SeByDocKy/pvbrain2/configuration_examples/dashboard/YamBMS_HA_Dashboard_page1_YAMBMS.png

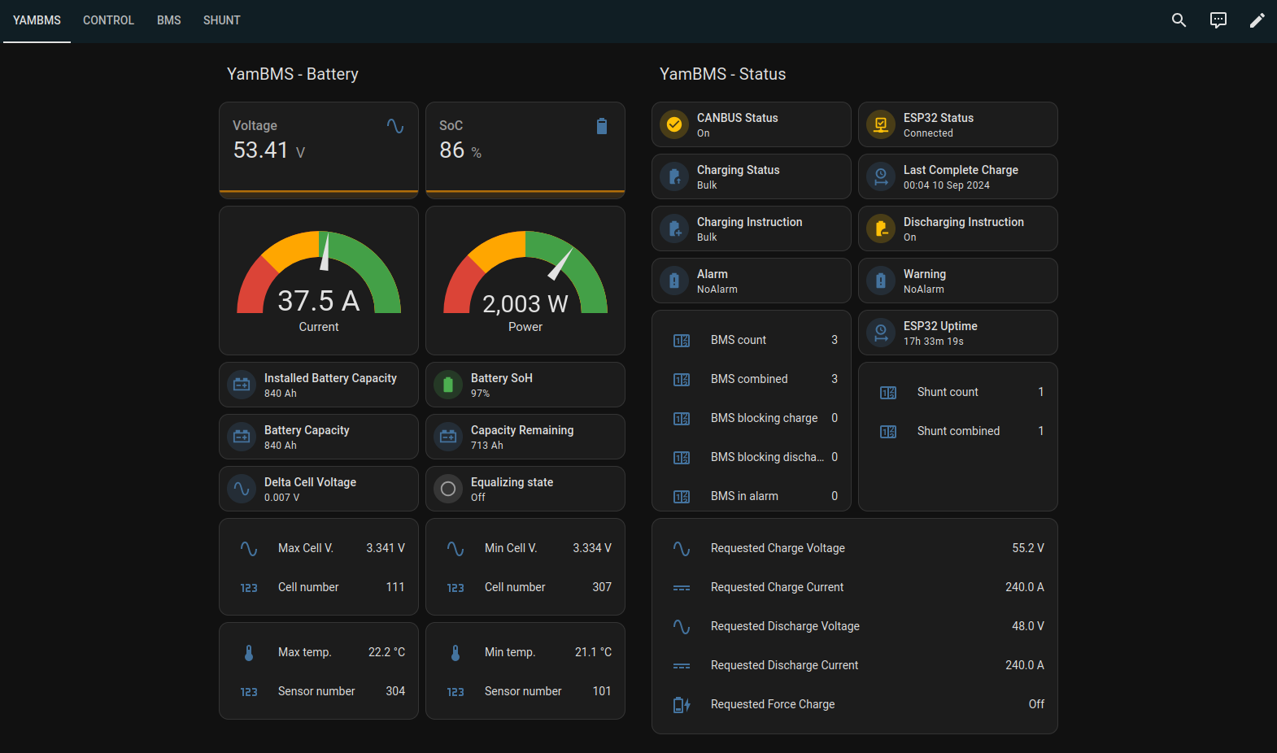
configuration_examples/dashboard/YamBMS_HA_Dashboard_page1_YAMBMS.png
