SeByDocKy/pvbrain2/configuration_examples/dashboard/YamBMS_HA_Dashboard_page2_CONTROL.png

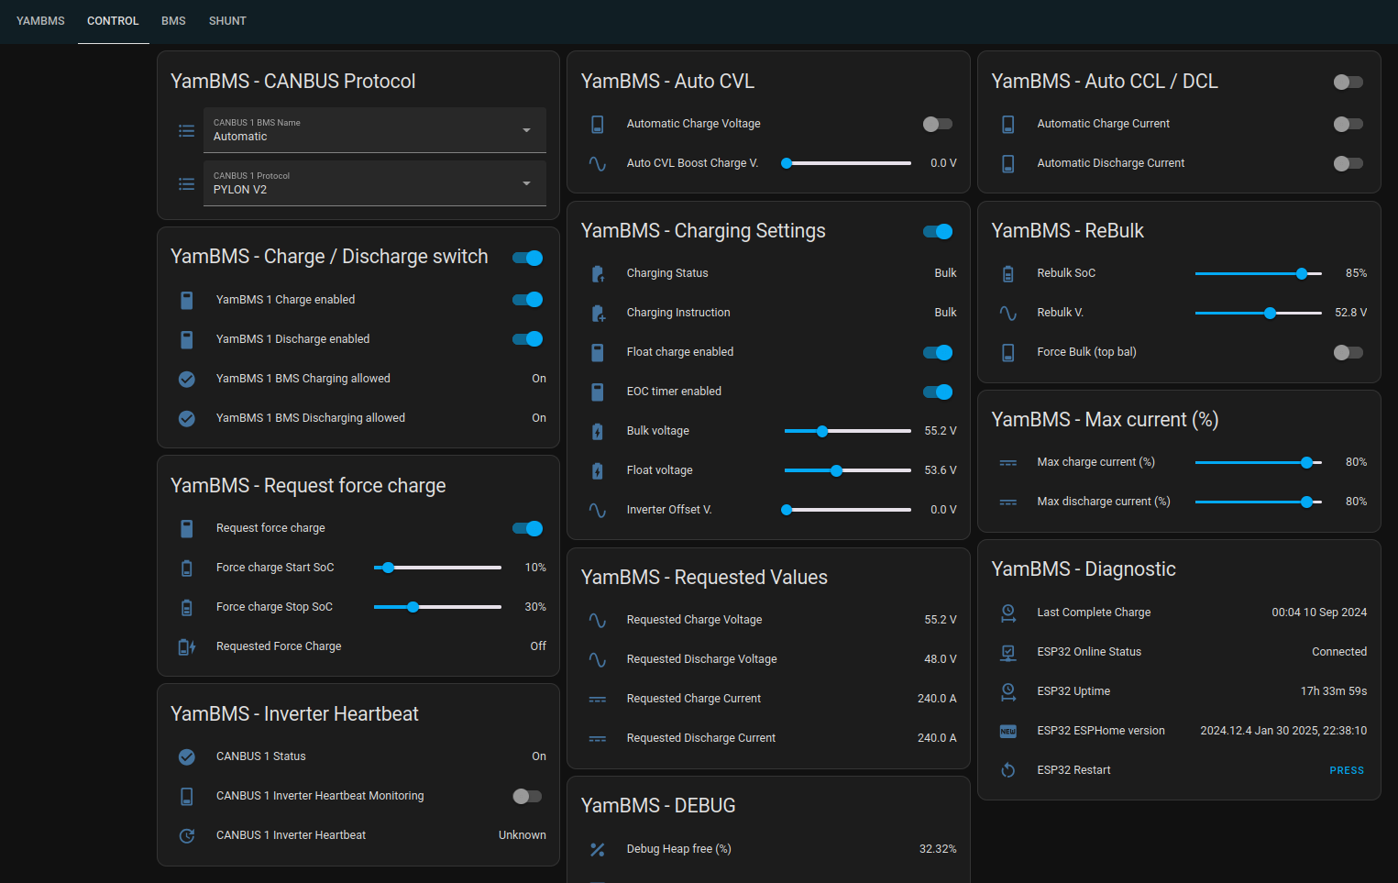
configuration_examples/dashboard/YamBMS_HA_Dashboard_page2_CONTROL.png
