SeByDocKy/pvbrain2/configuration_examples/dashboard/YamBMS_HA_Dashboard_page3_BMS.png

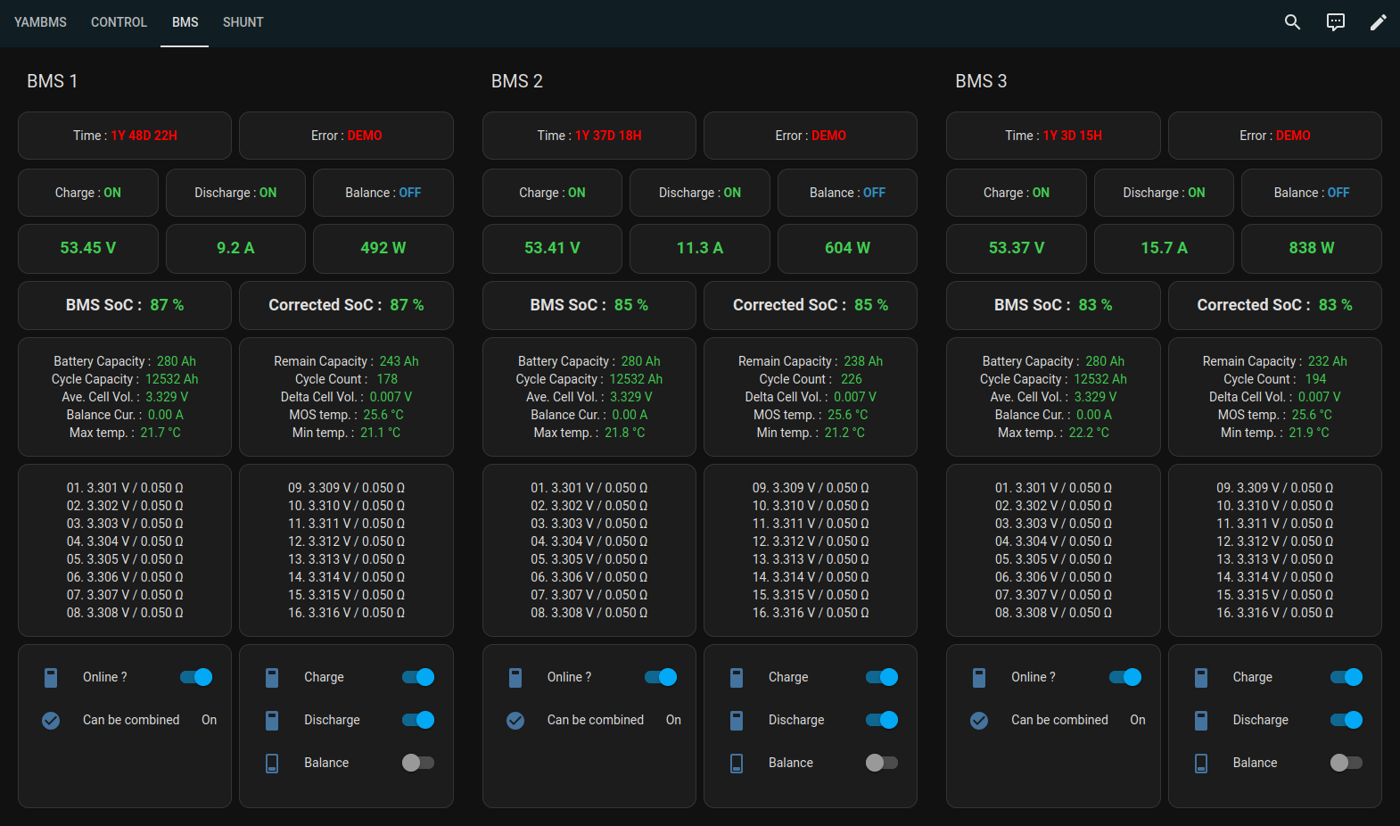
configuration_examples/dashboard/YamBMS_HA_Dashboard_page3_BMS.png
