SeByDocKy/pvbrain2/configuration_examples/dashboard/YamBMS_HA_Dashboard_page4_SHUNT.png

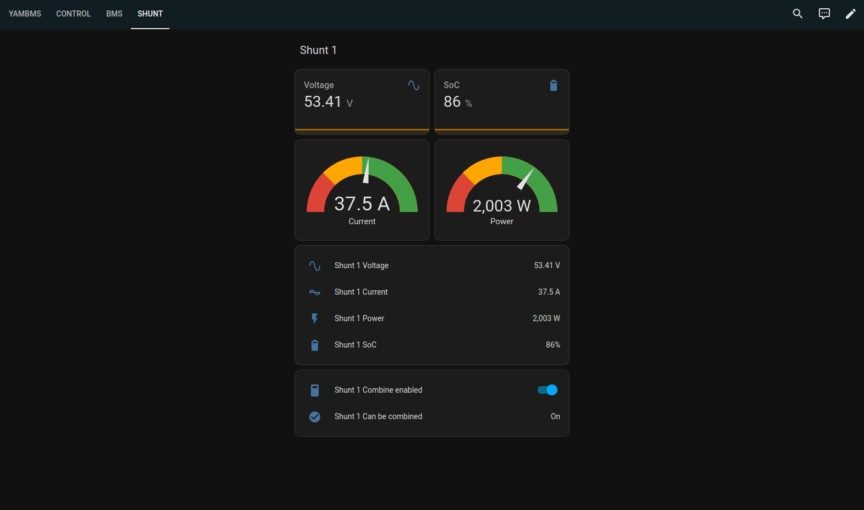
configuration_examples/dashboard/YamBMS_HA_Dashboard_page4_SHUNT.png
