SeByDocKy/pvbrain2/hardware/addon_carte_clamp_meter/clamp_meter_circuit_extend.png

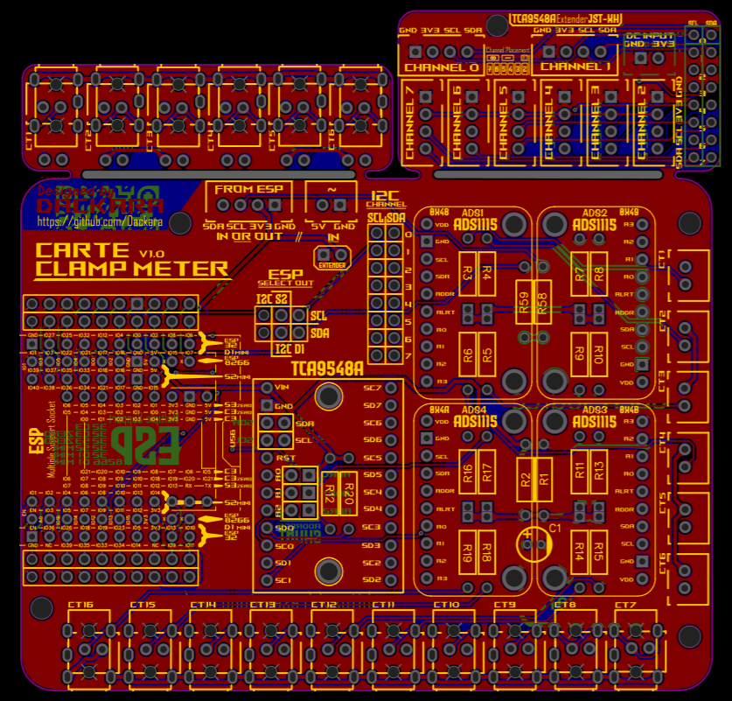
hardware/addon_carte_clamp_meter/clamp_meter_circuit_extend.png
