SeByDocKy/pvbrain2/hardware/addon_carte_fil_pilote/fil_pilote_3d_view.png

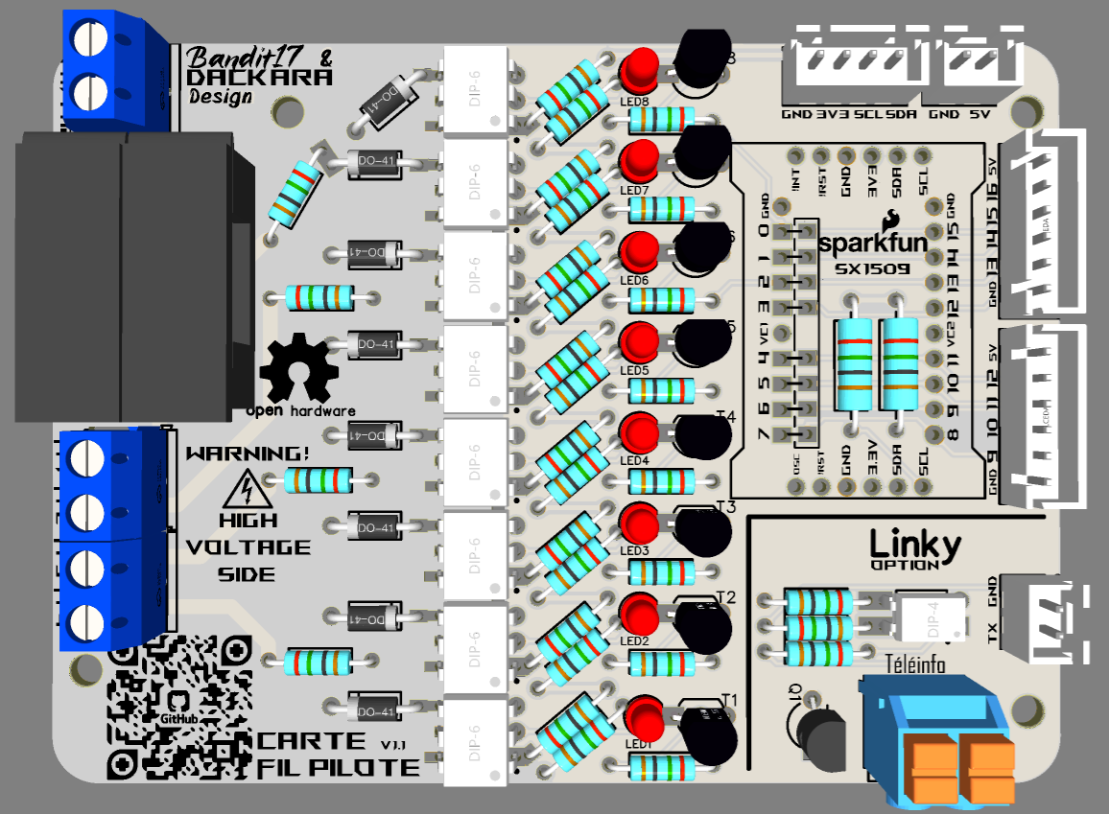
hardware/addon_carte_fil_pilote/fil_pilote_3d_view.png
