SeByDocKy/pvbrain2/hardware/addon_carte_fil_pilote/fil_pilote_photo.jpeg

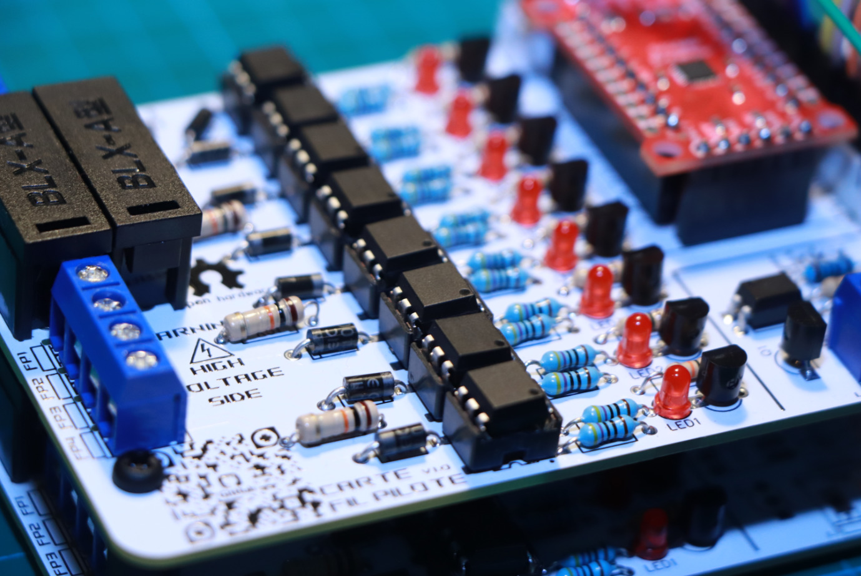
hardware/addon_carte_fil_pilote/fil_pilote_photo.jpeg
