SeByDocKy/pvbrain2/hardware/addon_carte_fil_pilote/fil_pilote_schematic_fp.png

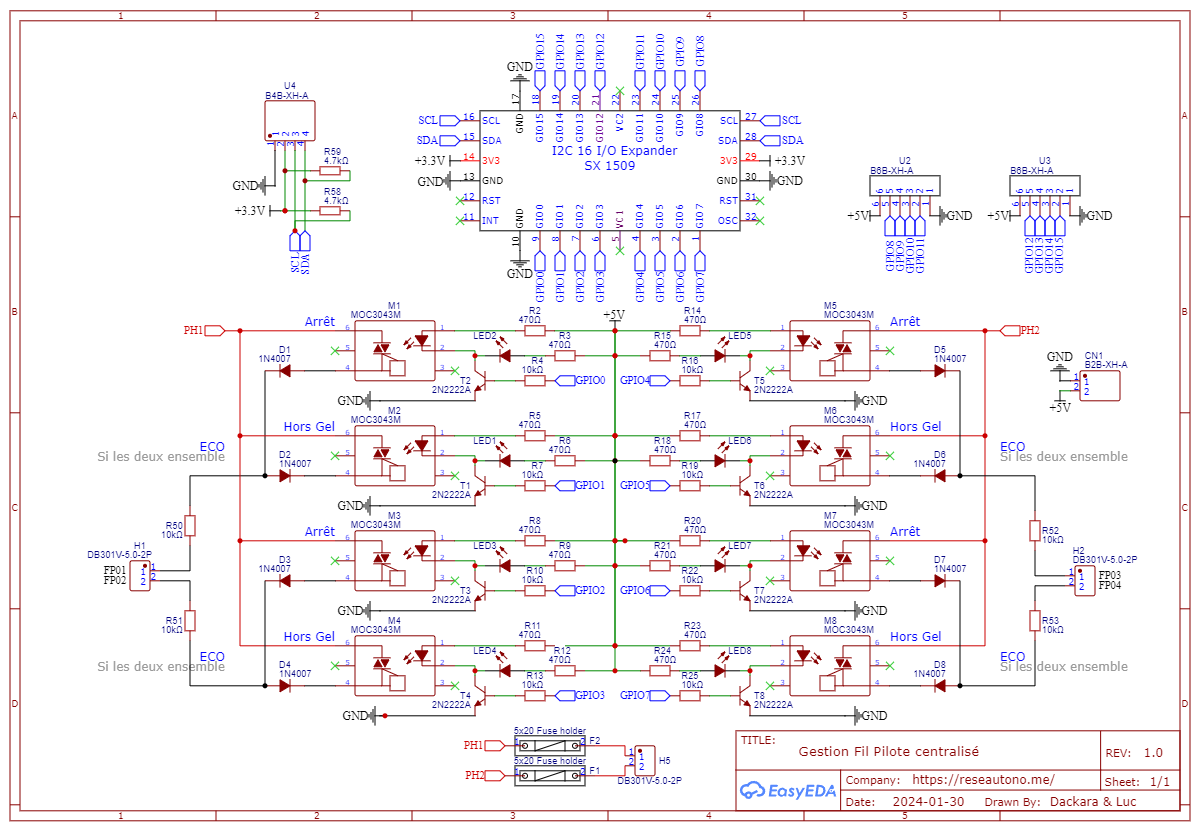
hardware/addon_carte_fil_pilote/fil_pilote_schematic_fp.png
