SeByDocKy/pvbrain2/hardware/addon_carte_fil_pilote/fil_pilote_v1.1_circuit_full.png

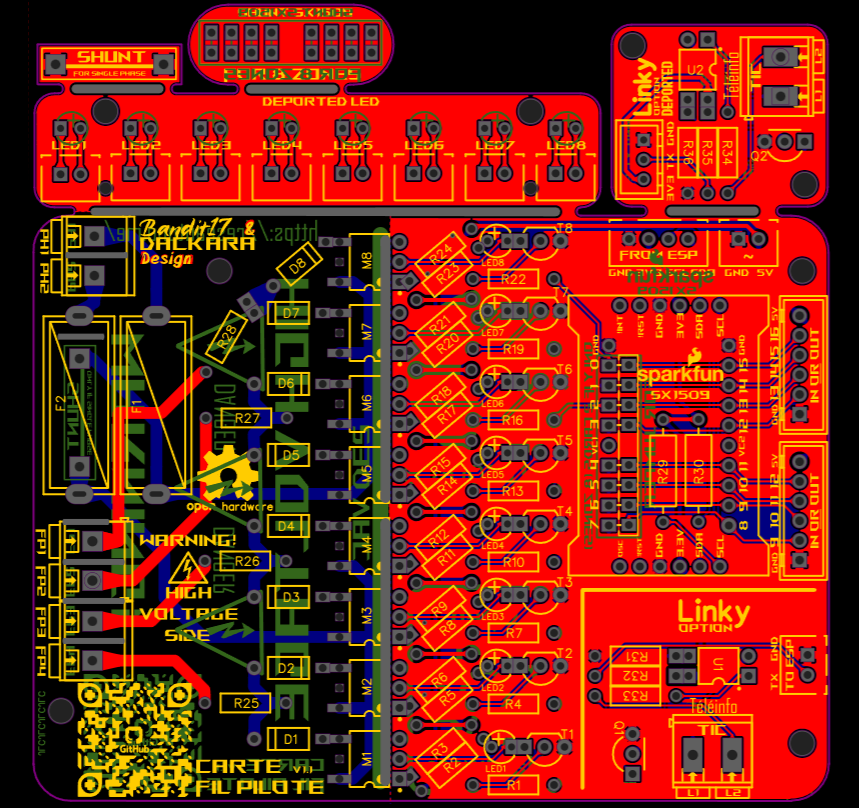
hardware/addon_carte_fil_pilote/fil_pilote_v1.1_circuit_full.png
