SeByDocKy/pvbrain2/hardware/addon_carte_prototype/carte_prototype_front_extend.png

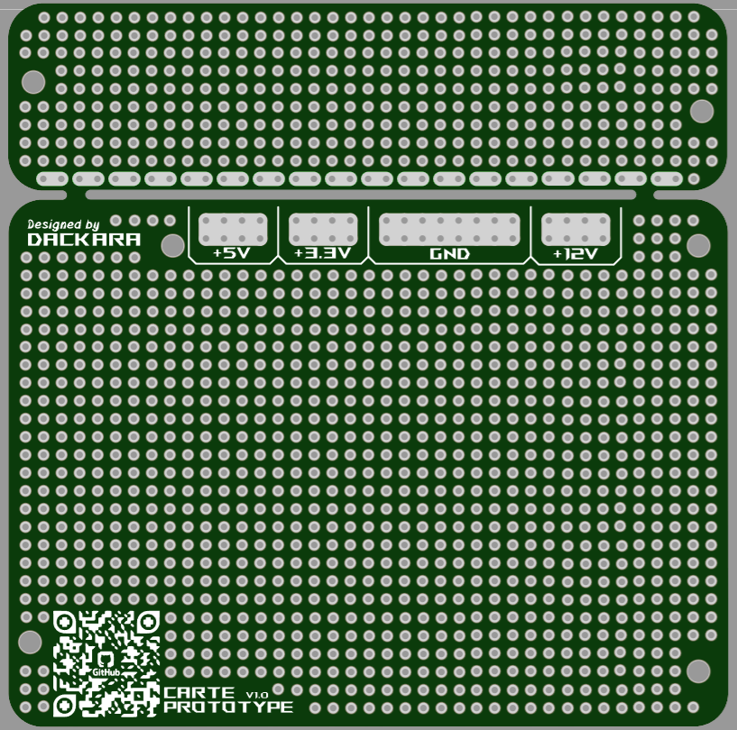
hardware/addon_carte_prototype/carte_prototype_front_extend.png
