SeByDocKy/pvbrain2/hardware/addon_carte_uart_extension/uart_extention_with_isolator-victron/uart_extension_with_victron_3d_view.png

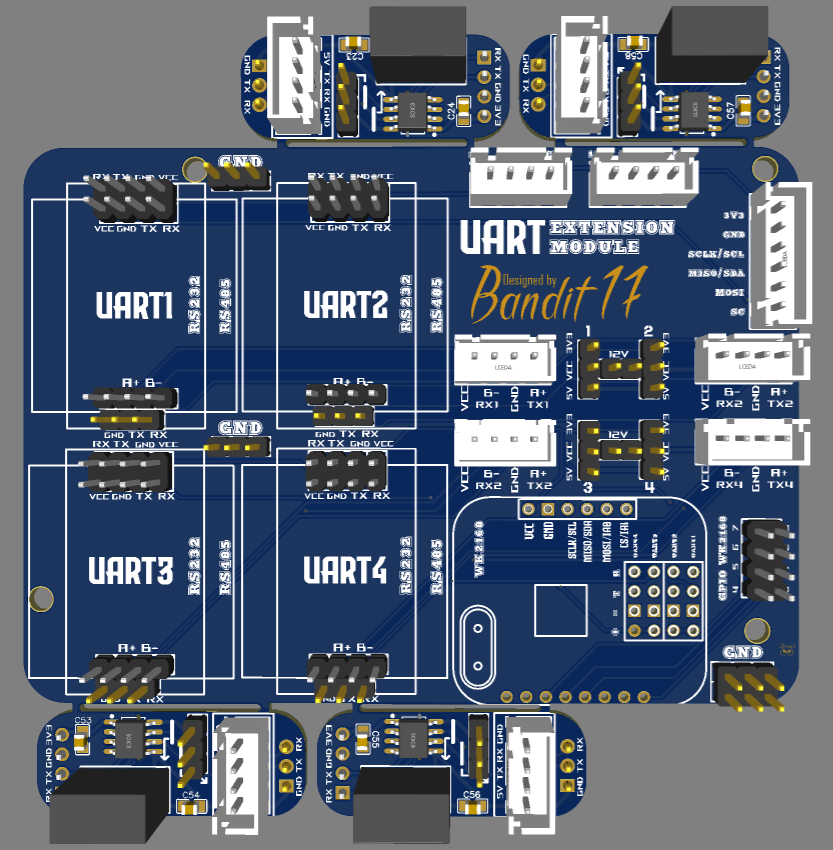
hardware/addon_carte_uart_extension/uart_extention_with_isolator-victron/uart_extension_with_victron_3d_view.png
