SeByDocKy/pvbrain2/hardware/module_wk_2132/wk2132_front.png

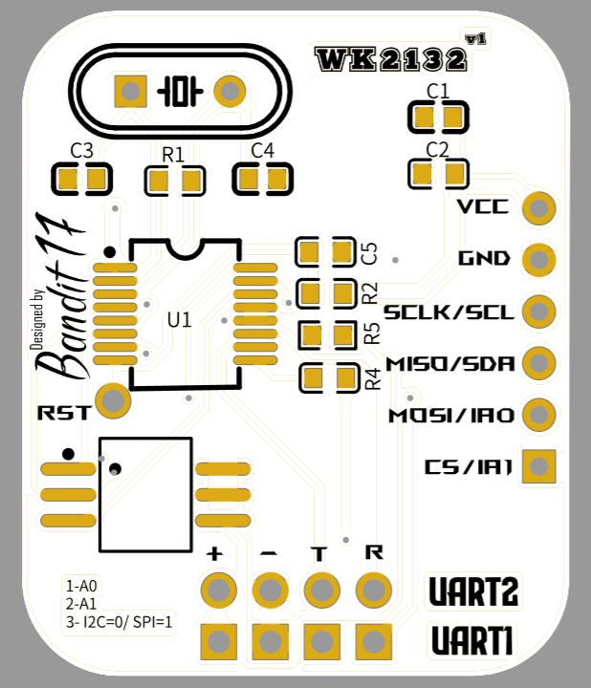
hardware/module_wk_2132/wk2132_front.png
