SeByDocKy/pvbrain2/pictures/pvbrain_all_thing_3d_view.png

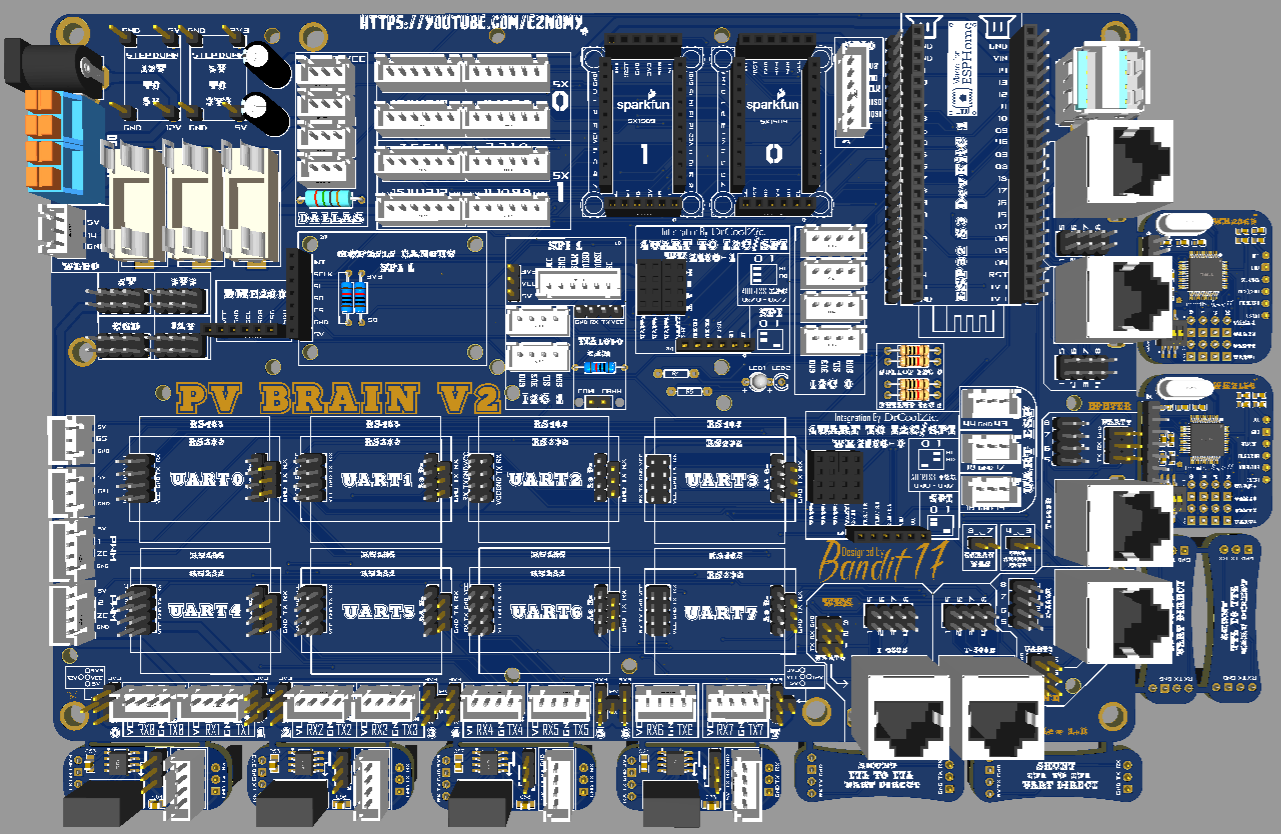
pictures/pvbrain_all_thing_3d_view.png
