SeByDocKy/pvbrain2/pictures/pvbrain_all_thing_back.png

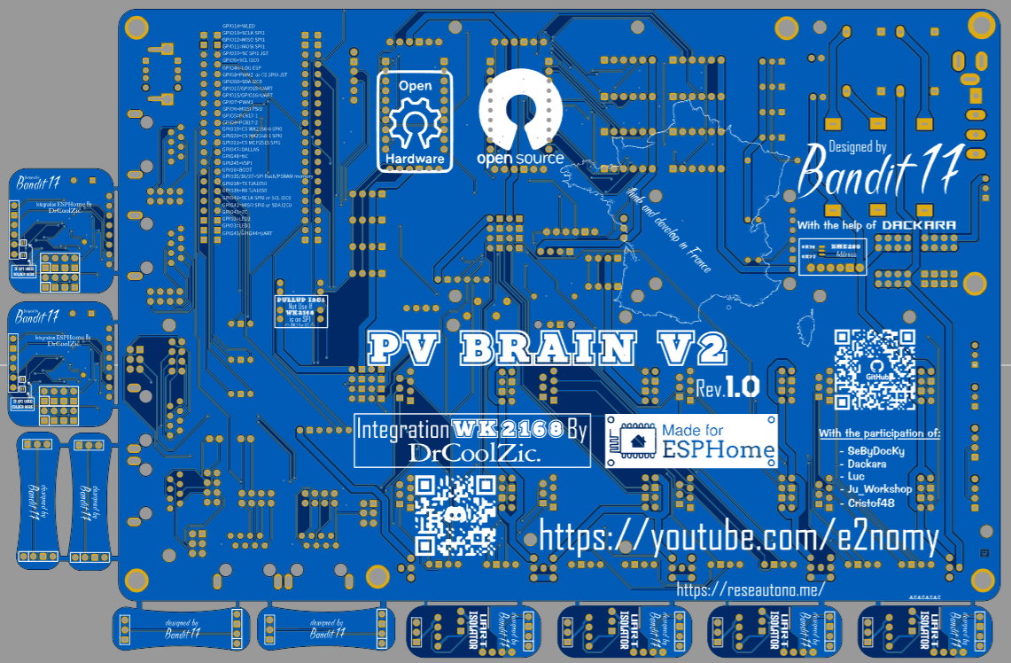
pictures/pvbrain_all_thing_back.png
