SeByDocKy/pvbrain2/pictures/pvbrain_all_thing_front.png

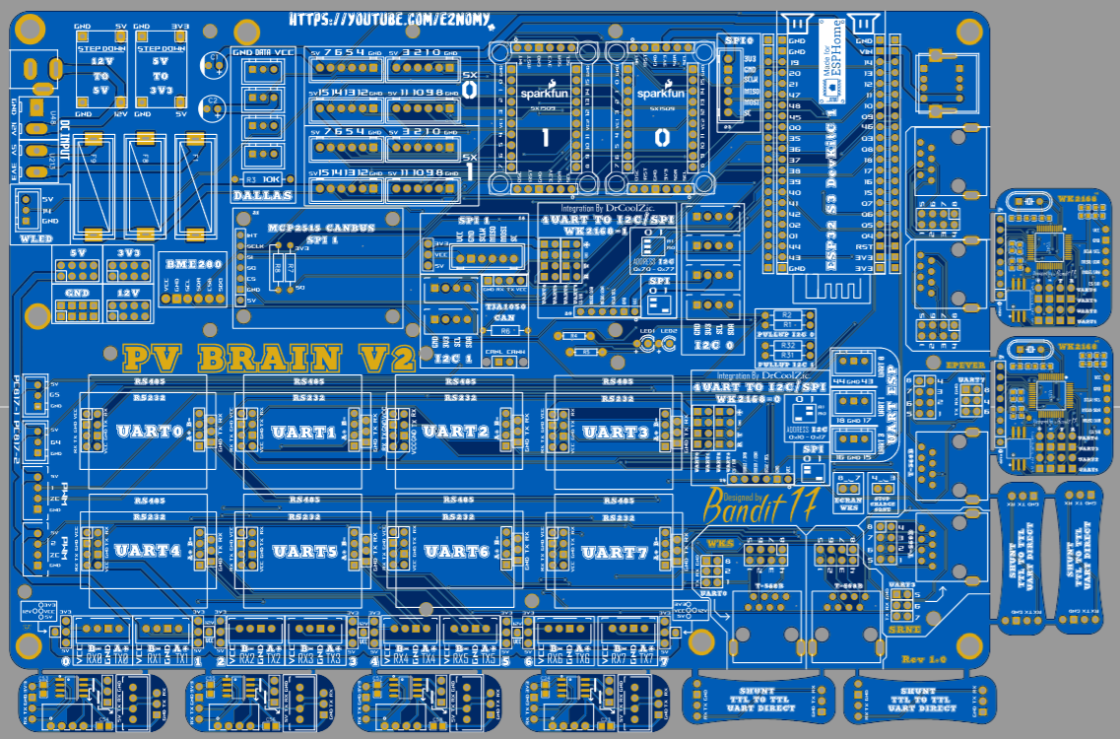
pictures/pvbrain_all_thing_front.png
