SeByDocKy/pvbrain2/pictures/pvbrain_view_bicolor_led.png

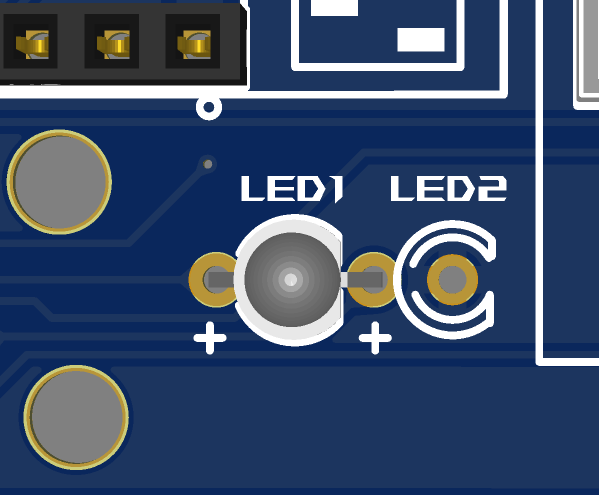
pictures/pvbrain_view_bicolor_led.png
