SeByDocKy/pvbrain2/pictures/pvbrain_view_bme280.png

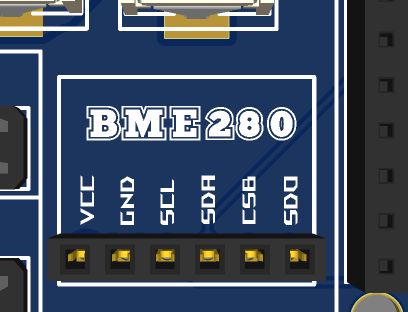
pictures/pvbrain_view_bme280.png
