SeByDocKy/pvbrain2/pictures/pvbrain_view_bme280_change_address.png

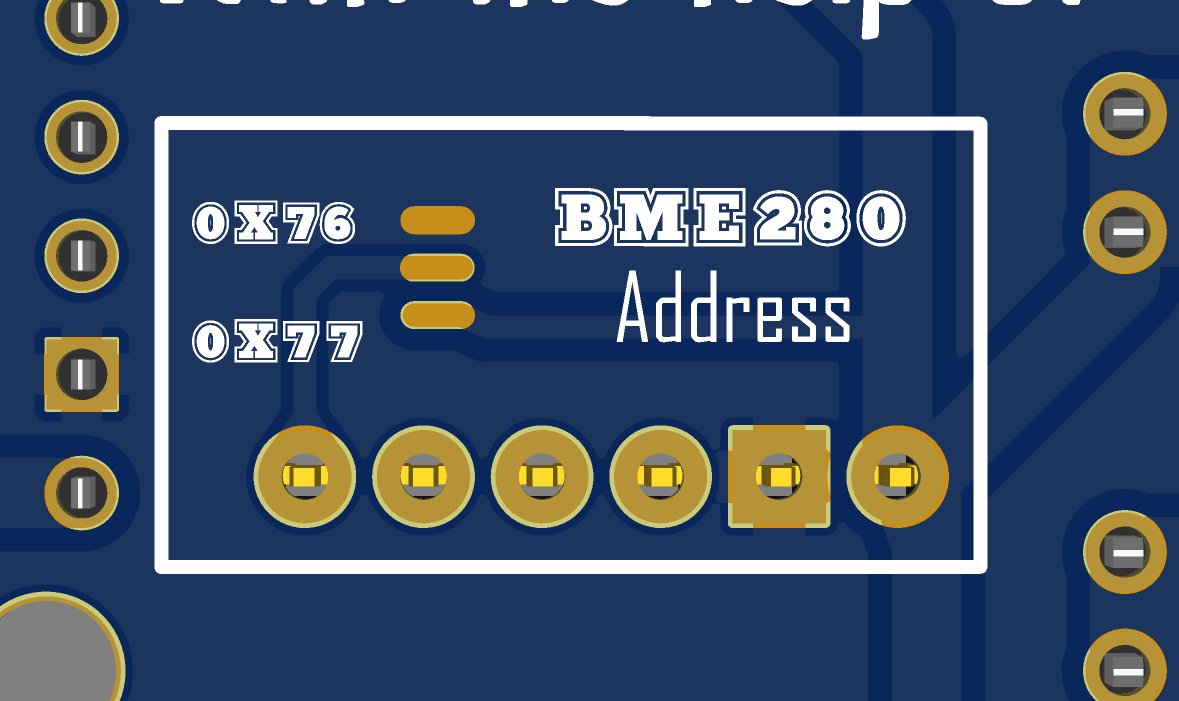
pictures/pvbrain_view_bme280_change_address.png
