SeByDocKy/pvbrain2/pictures/pvbrain_view_can_output.png

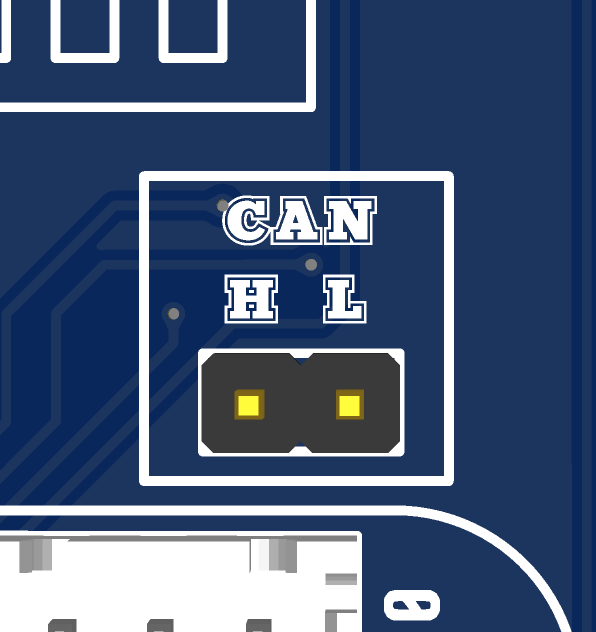
pictures/pvbrain_view_can_output.png
