SeByDocKy/pvbrain2/pictures/pvbrain_view_dallas.png

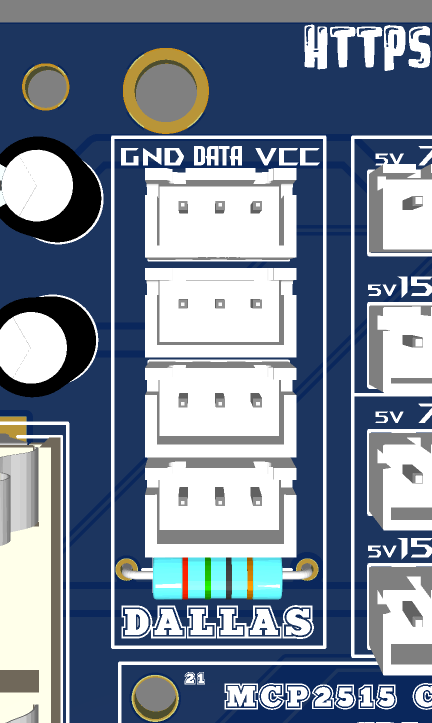
pictures/pvbrain_view_dallas.png
