SeByDocKy/pvbrain2/pictures/pvbrain_view_dc_input.png

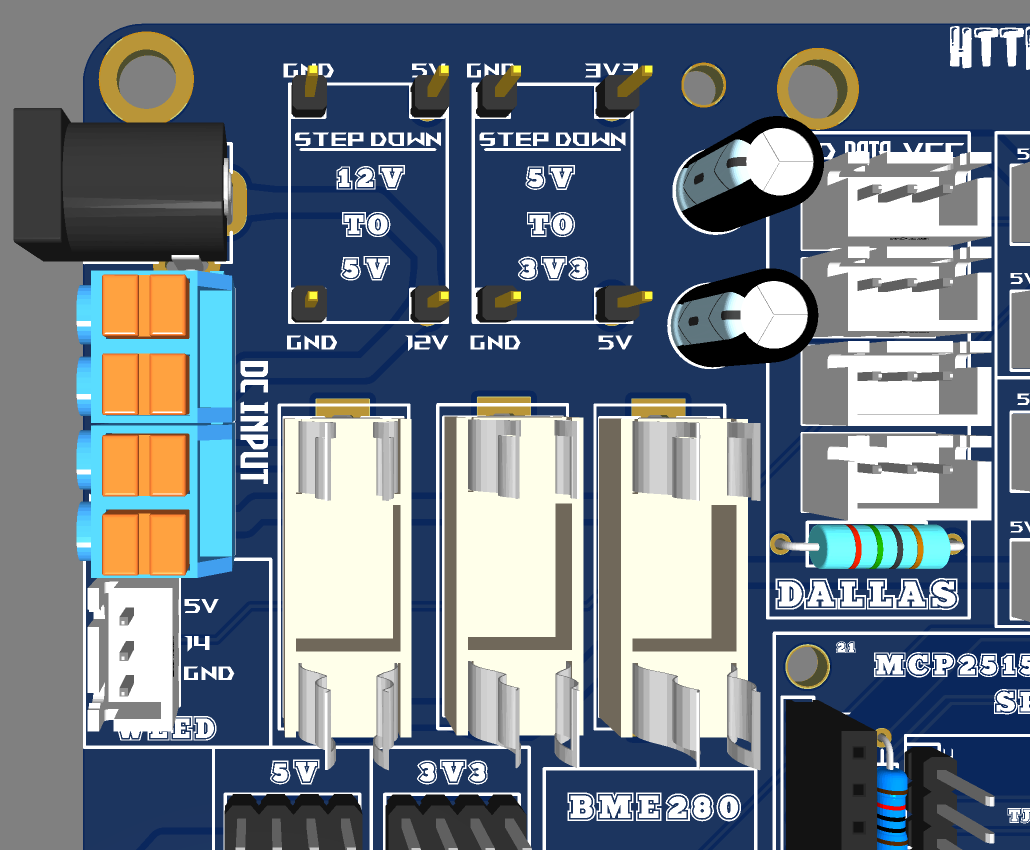
pictures/pvbrain_view_dc_input.png
