SeByDocKy/pvbrain2/pictures/pvbrain_view_dc_output.png

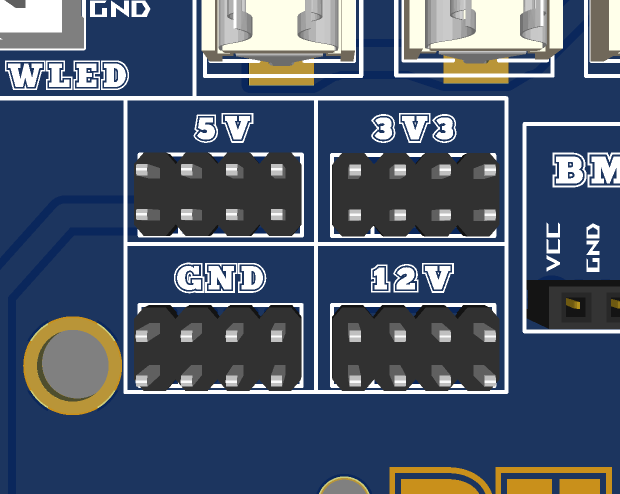
pictures/pvbrain_view_dc_output.png
