SeByDocKy/pvbrain2/pictures/pvbrain_view_epever_output.png

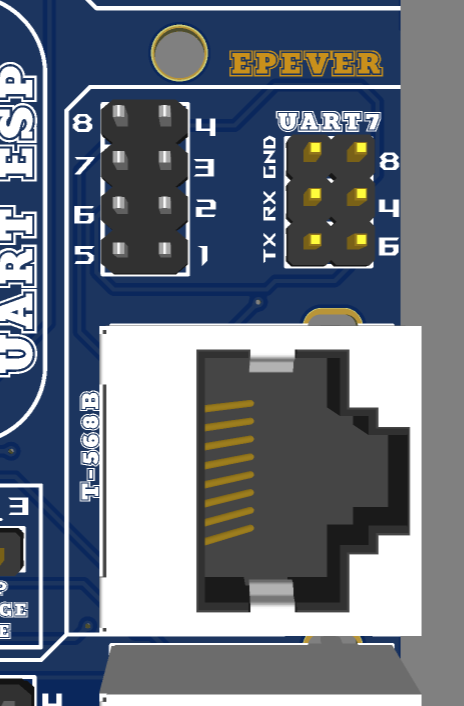
pictures/pvbrain_view_epever_output.png
