SeByDocKy/pvbrain2/pictures/pvbrain_view_esp32s3_socket.png

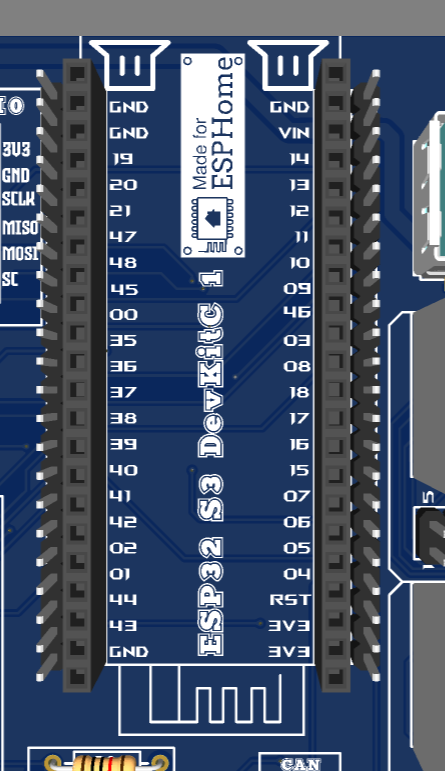
pictures/pvbrain_view_esp32s3_socket.png
