SeByDocKy/pvbrain2/pictures/pvbrain_view_i2c0.png

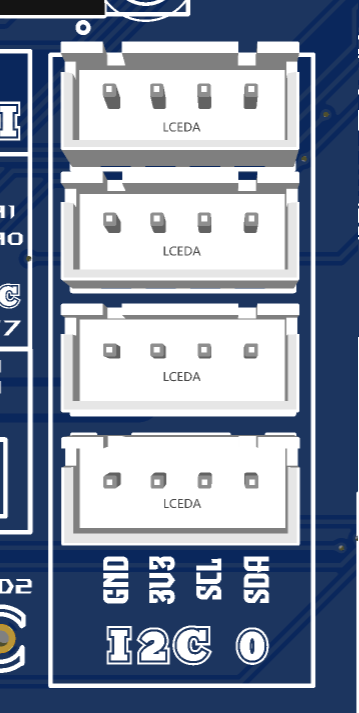
pictures/pvbrain_view_i2c0.png
