SeByDocKy/pvbrain2/pictures/pvbrain_view_i2c1.png

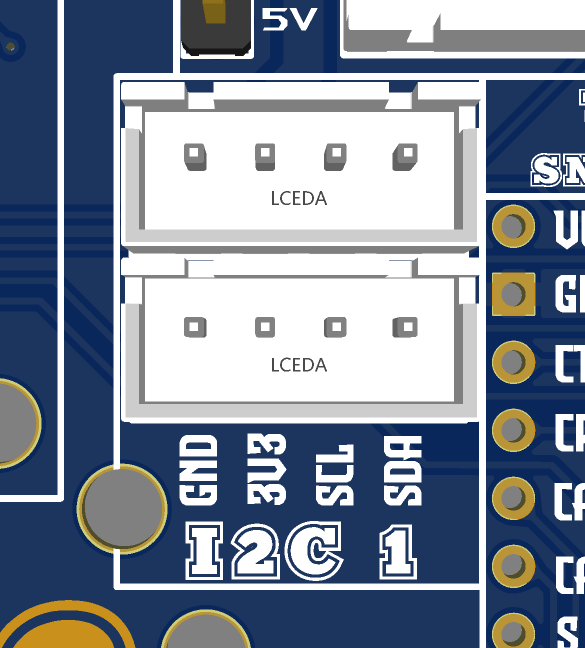
pictures/pvbrain_view_i2c1.png
