SeByDocKy/pvbrain2/pictures/pvbrain_view_isolator_jkbms.png

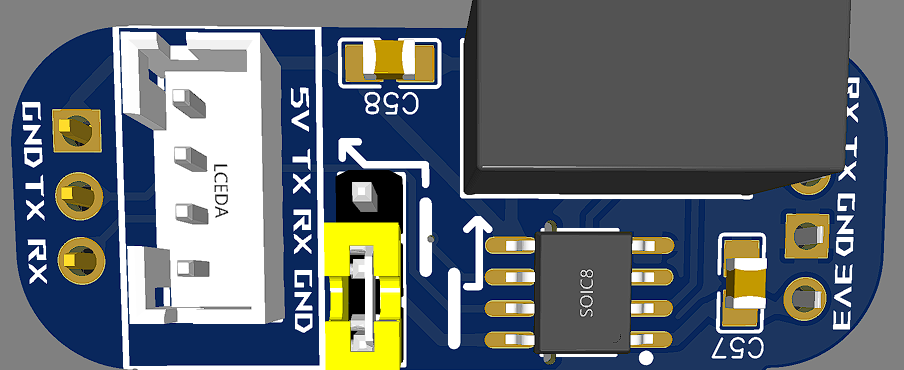
pictures/pvbrain_view_isolator_jkbms.png
