SeByDocKy/pvbrain2/pictures/pvbrain_view_isolator_pzem.png

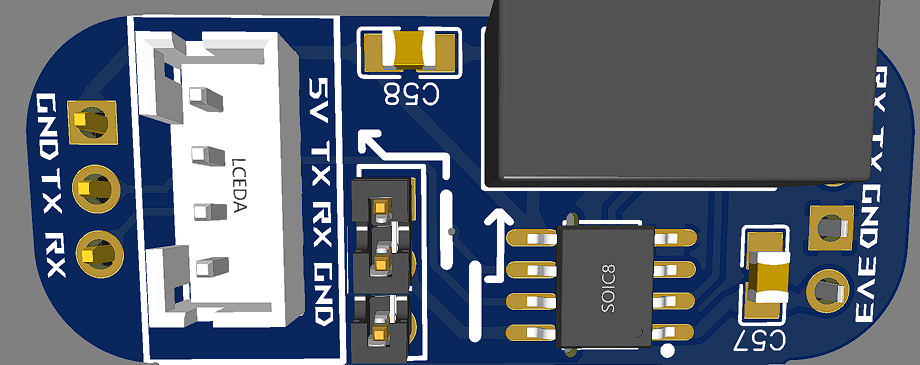
pictures/pvbrain_view_isolator_pzem.png
