SeByDocKy/pvbrain2/pictures/pvbrain_view_isolator_Victron.png

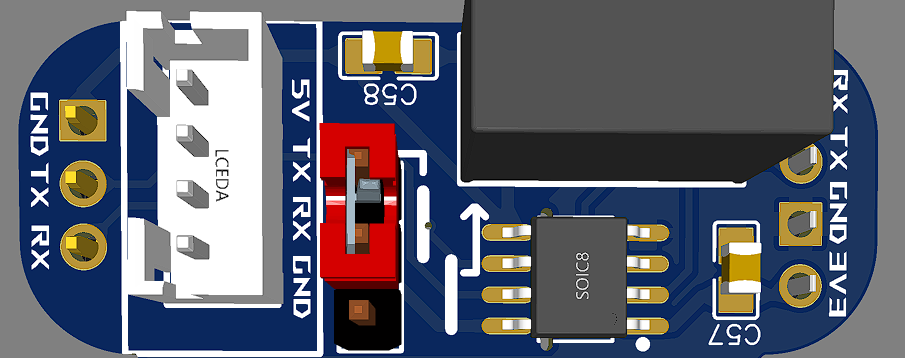
pictures/pvbrain_view_isolator_Victron.png
