SeByDocKy/pvbrain2/pictures/pvbrain_view_mcp2515.png

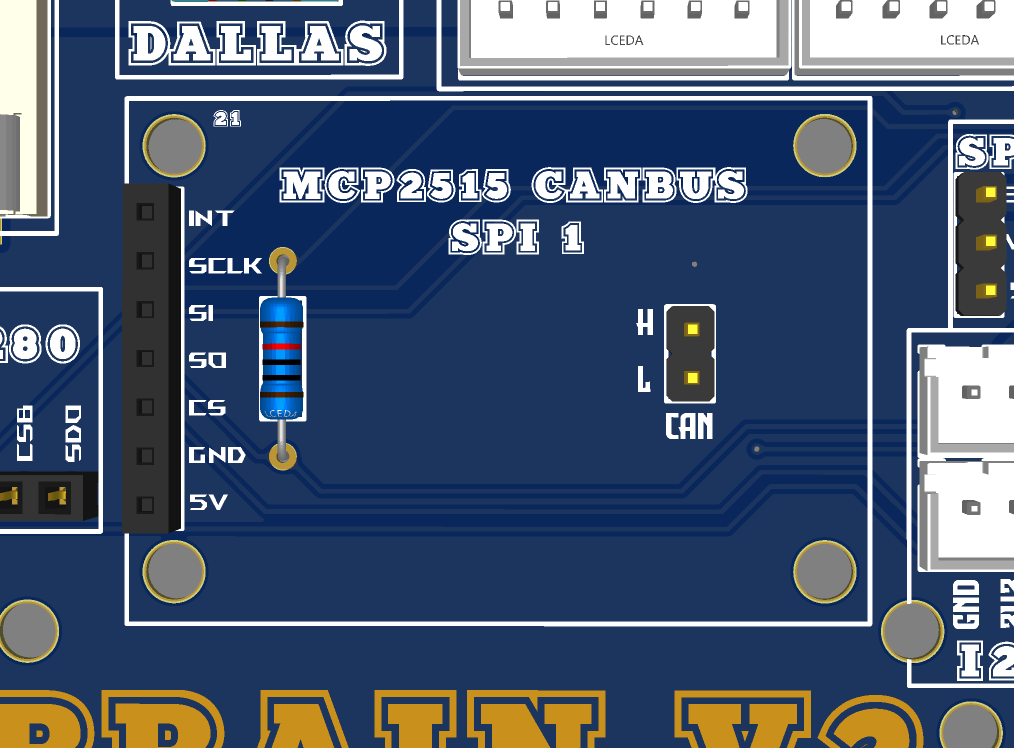
pictures/pvbrain_view_mcp2515.png
