SeByDocKy/pvbrain2/pictures/pvbrain_view_opto_output.png

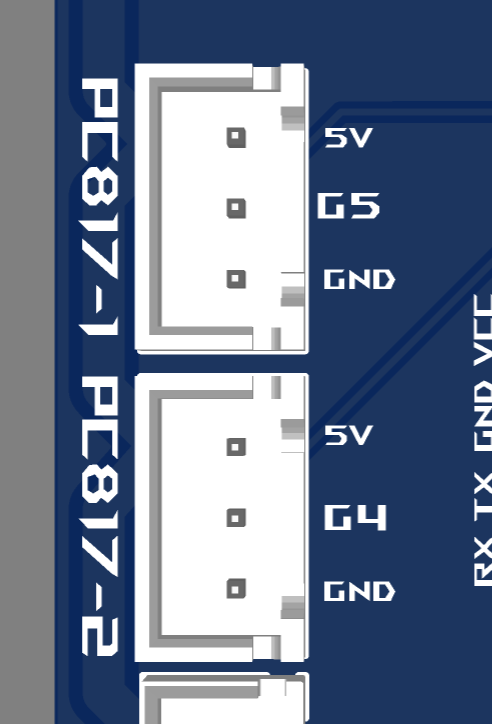
pictures/pvbrain_view_opto_output.png
