SeByDocKy/pvbrain2/pictures/pvbrain_view_physical_uart.png

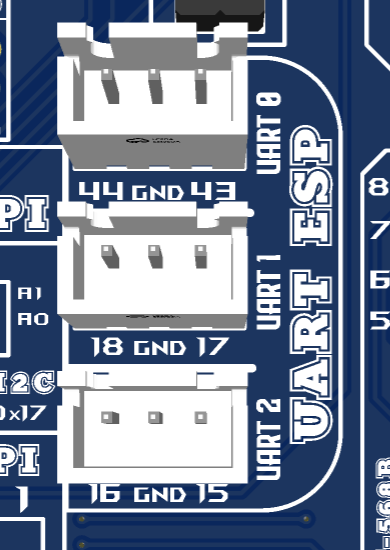
pictures/pvbrain_view_physical_uart.png
