SeByDocKy/pvbrain2/pictures/pvbrain_view_pwm_output.png

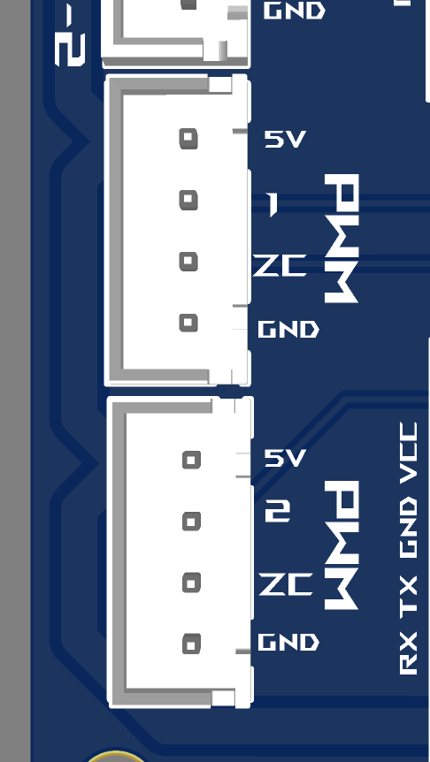
pictures/pvbrain_view_pwm_output.png
