SeByDocKy/pvbrain2/pictures/pvbrain_view_snre_output.png

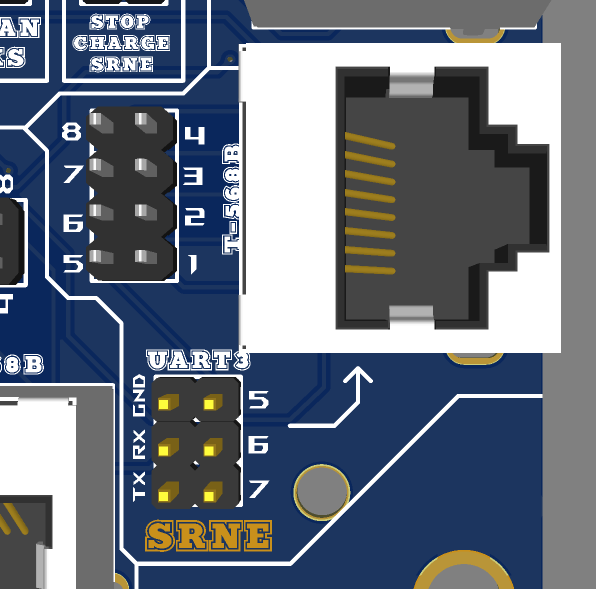
pictures/pvbrain_view_snre_output.png
