SeByDocKy/pvbrain2/pictures/pvbrain_view_spi0.png

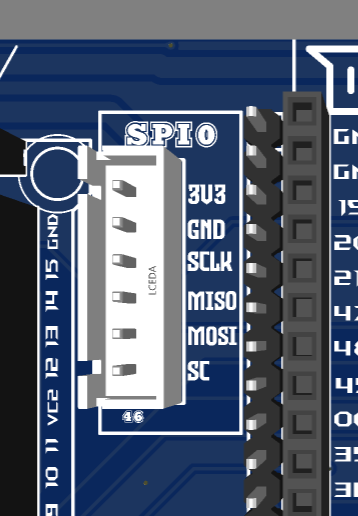
pictures/pvbrain_view_spi0.png
