SeByDocKy/pvbrain2/pictures/pvbrain_view_spi1.png

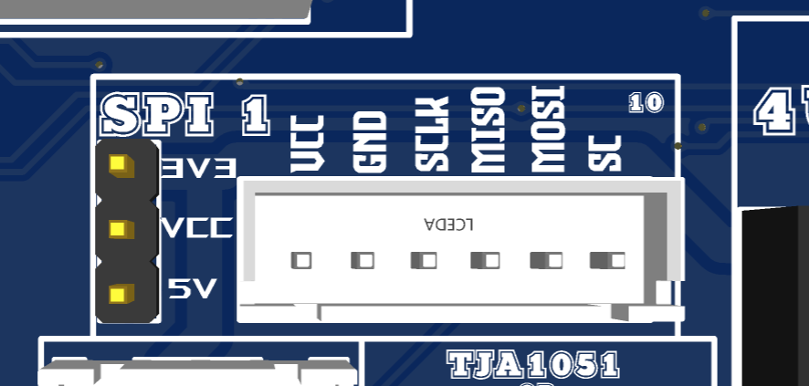
pictures/pvbrain_view_spi1.png
