SeByDocKy/pvbrain2/pictures/pvbrain_view_sx1509.png

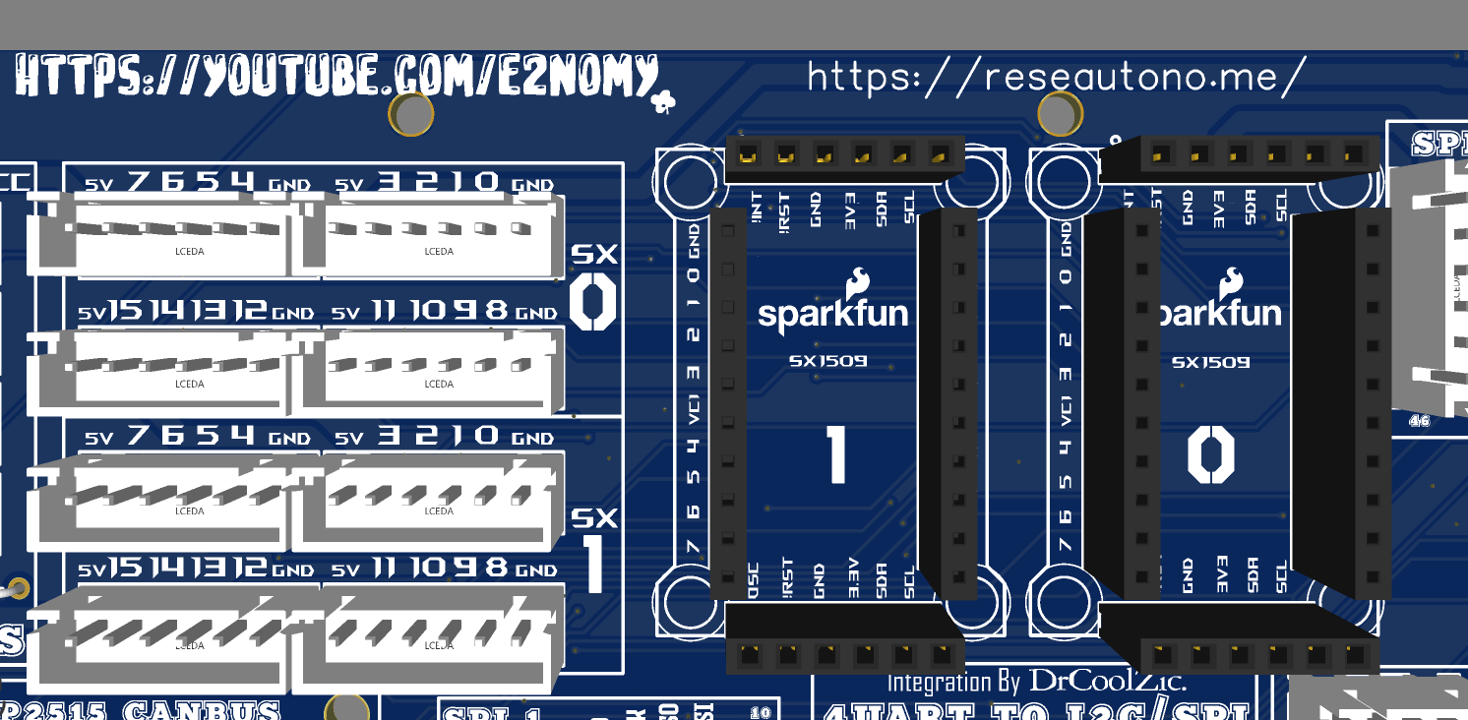
pictures/pvbrain_view_sx1509.png
