SeByDocKy/pvbrain2/pictures/pvbrain_view_tja1051_or_sn65hvd230.png

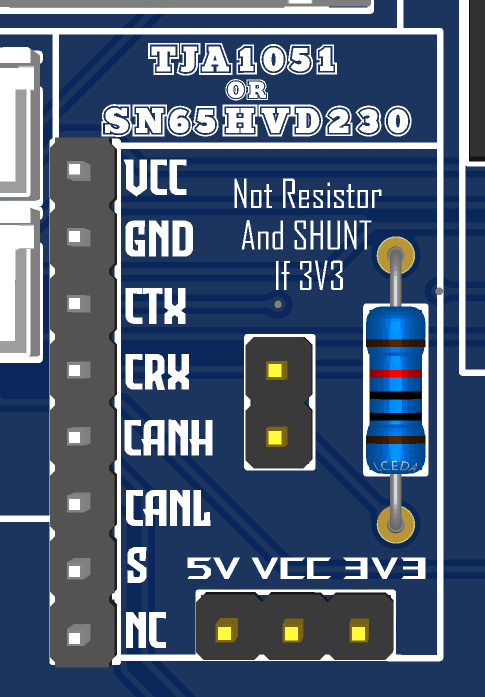
pictures/pvbrain_view_tja1051_or_sn65hvd230.png
