SeByDocKy/pvbrain2/pictures/pvbrain_view_wk2168-1.png

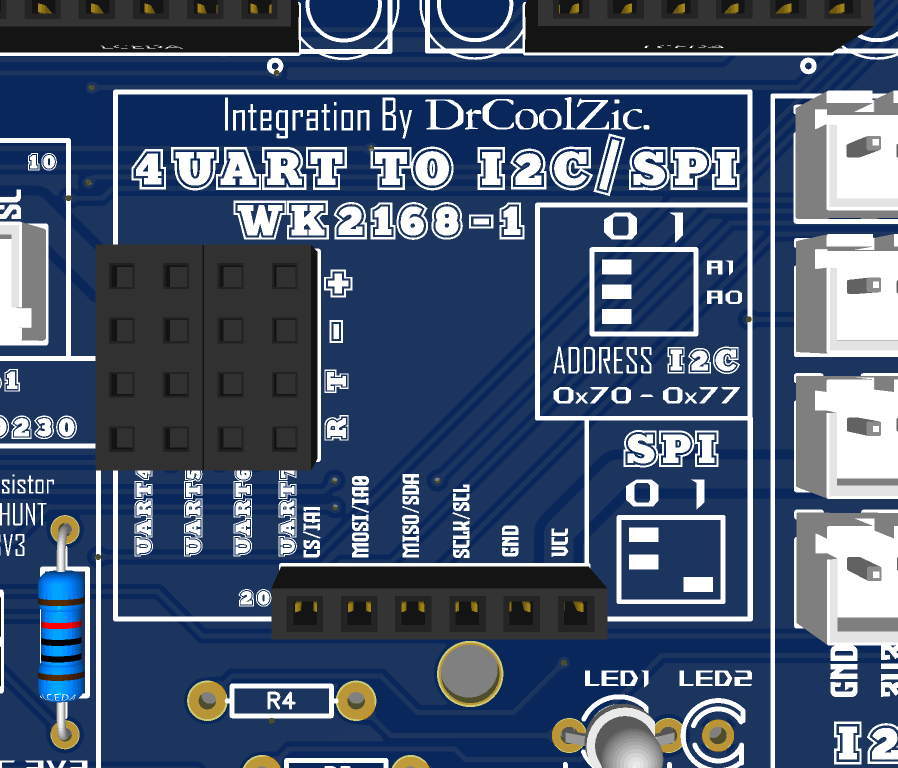
pictures/pvbrain_view_wk2168-1.png
