SeByDocKy/pvbrain2/pictures/pvbrain_view_wk2168_output.png

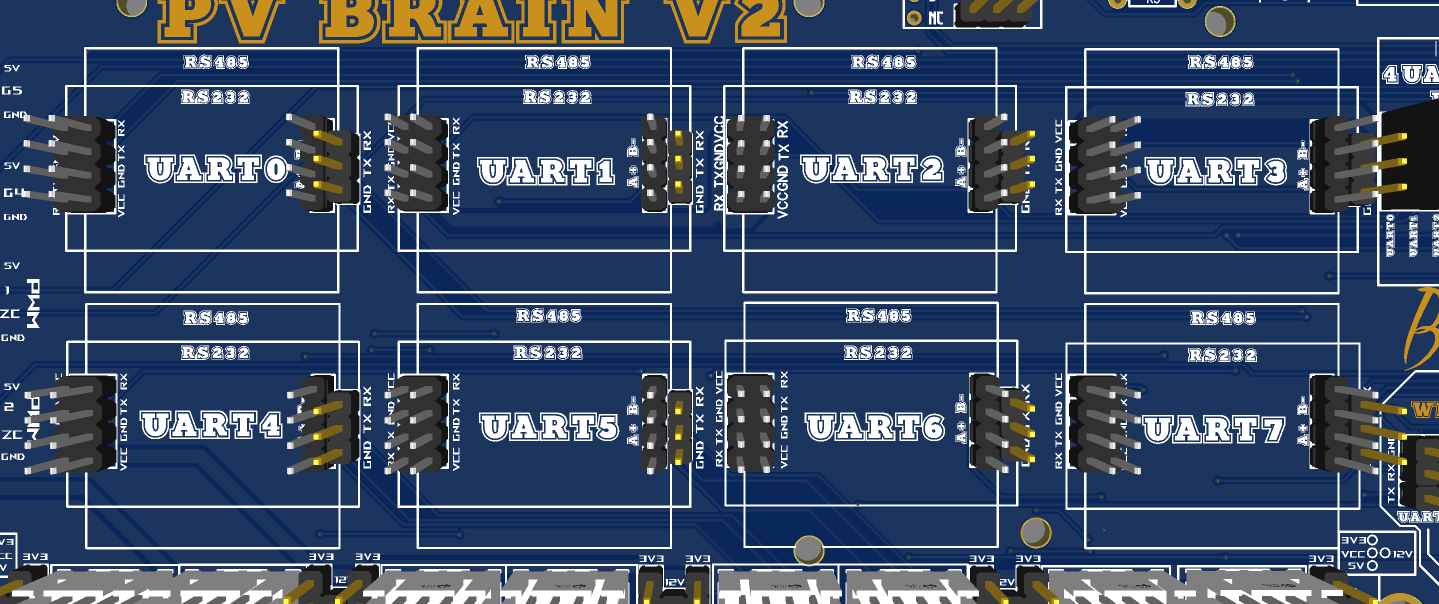
pictures/pvbrain_view_wk2168_output.png
