SeByDocKy/pvbrain2/pictures/pvbrain_view_wks_output.png

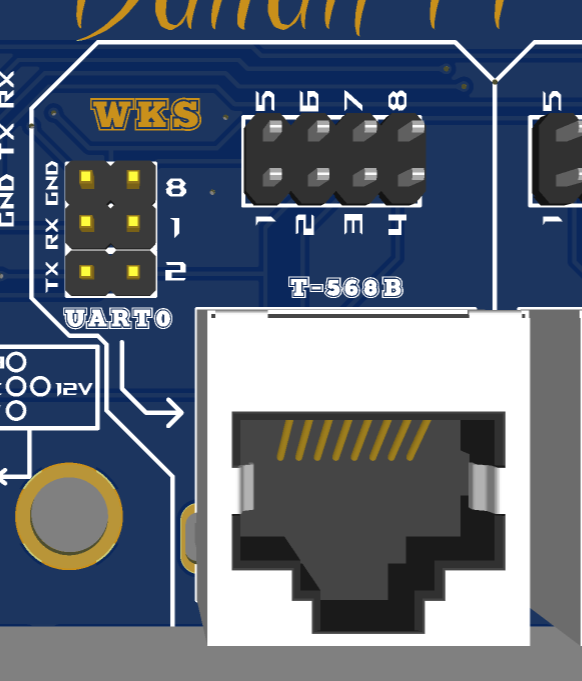
pictures/pvbrain_view_wks_output.png
