SeByDocKy/pvbrain2/pictures/pvbrain_view_wled.png

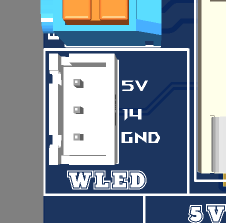
pictures/pvbrain_view_wled.png
