SeByDocKy/pvbrain2/pictures/wk2168_back.PNG

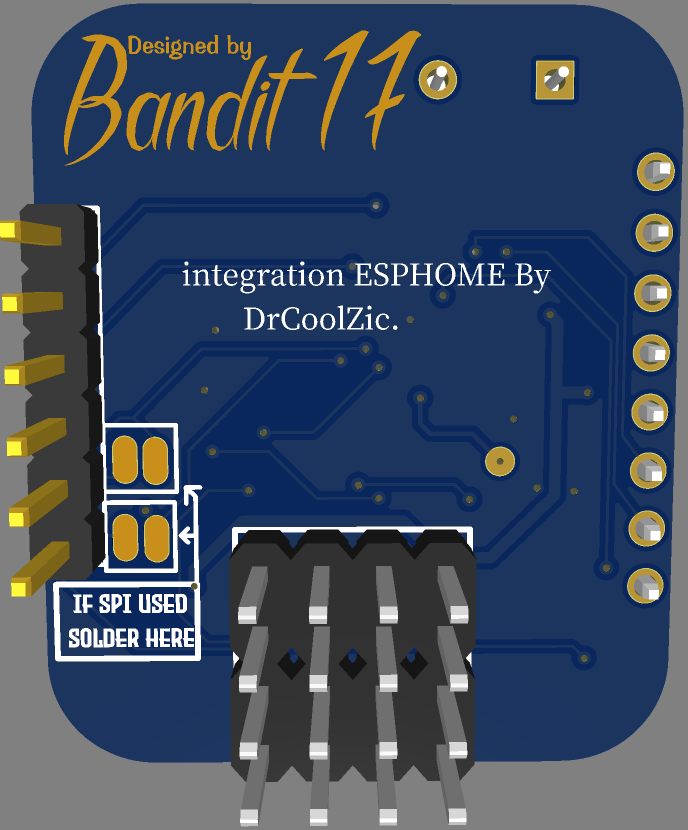
pictures/wk2168_back.PNG
