SeByDocKy/pvbrain2/pvbrain2/environmental/light/teleruptor/pictures/exemple_mount_opto+relay1.jpg

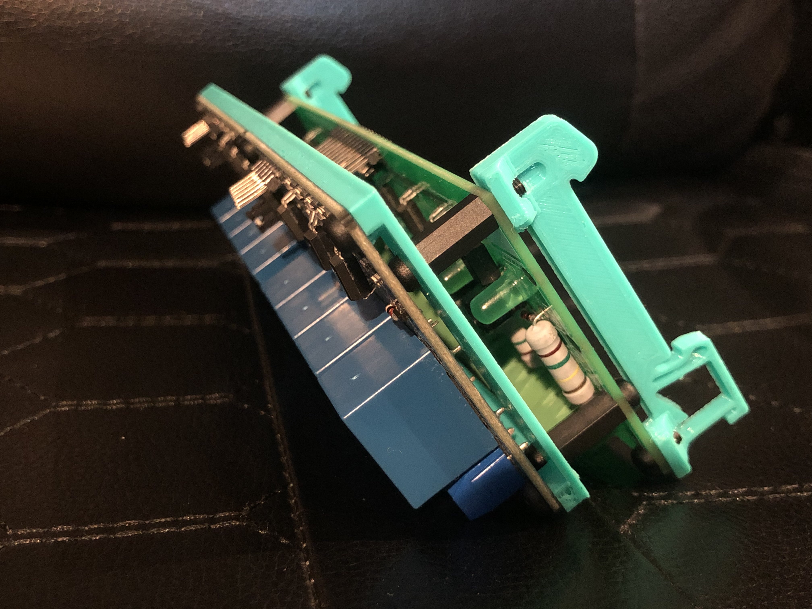
pvbrain2/environmental/light/teleruptor/pictures/exemple_mount_opto+relay1.jpg
