SeByDocKy/pvbrain2/pvbrain2/environmental/light/teleruptor/pictures/exemple_mount_opto+relay3d.png

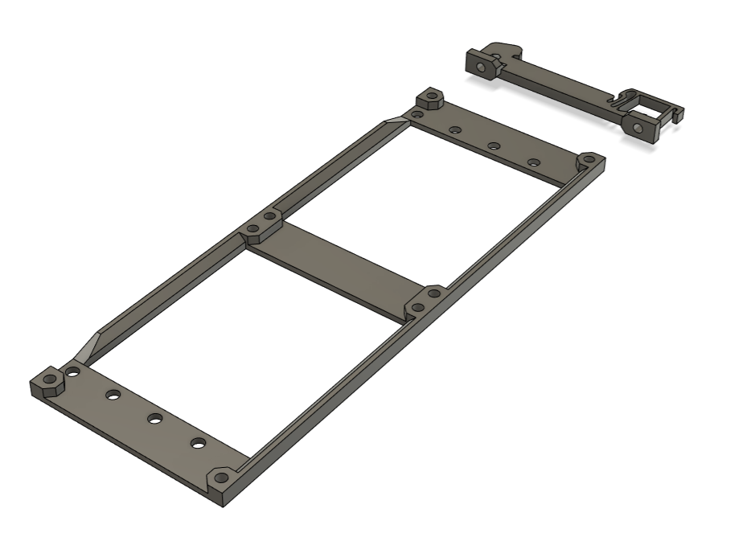
pvbrain2/environmental/light/teleruptor/pictures/exemple_mount_opto+relay3d.png
