SeByDocKy/pvbrain2/pvbrain2/environmental/light/teleruptor/pictures/teleruptor_tree.png

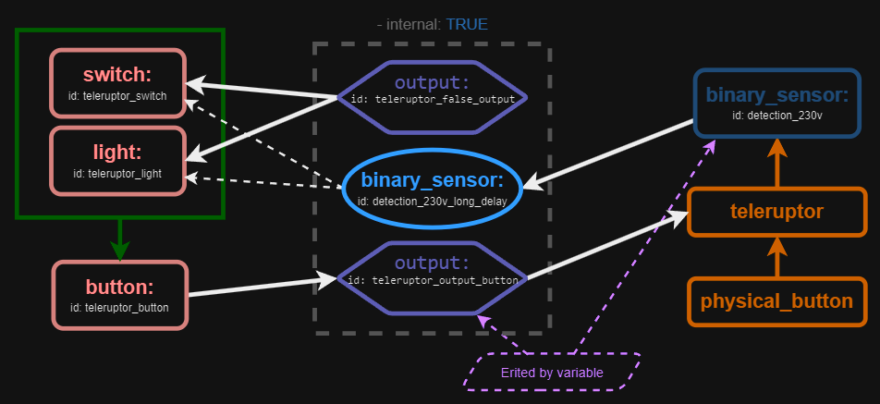
pvbrain2/environmental/light/teleruptor/pictures/teleruptor_tree.png
