SeByDocKy/pvbrain2/pvbrain2/powermeter/ac/sinotimer/dts6619/dts6619-042.jpg

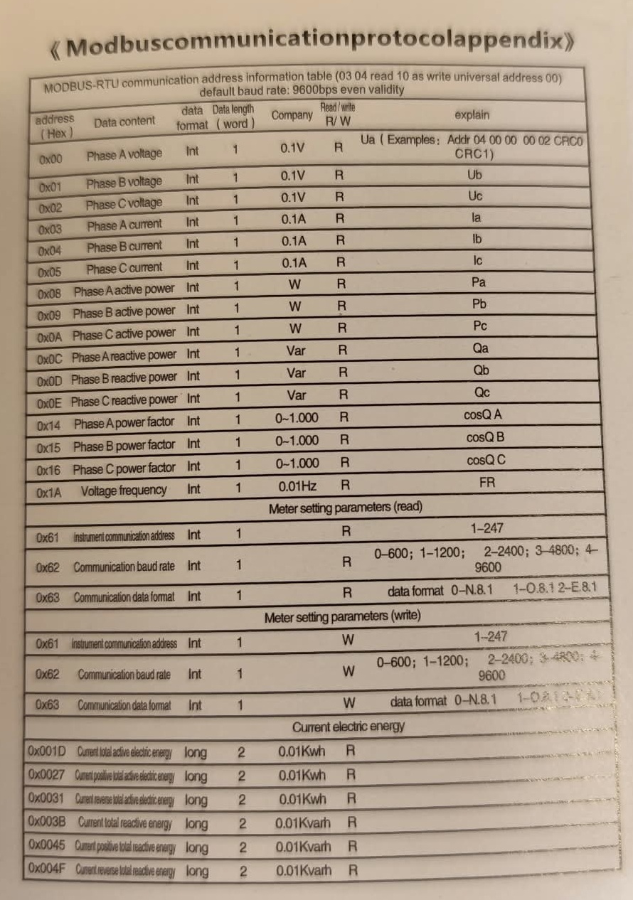
pvbrain2/powermeter/ac/sinotimer/dts6619/dts6619-042.jpg
