SeByDocKy/pvbrain2/hardware/printable_3d_files/JKBMS_Vertical_Support/Support_JKBMS_0.png

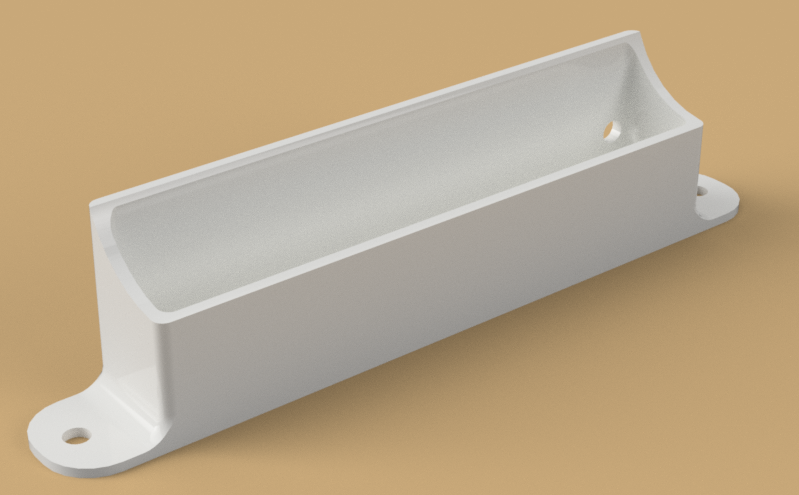
hardware/printable_3d_files/JKBMS_Vertical_Support/Support_JKBMS_0.png
