SeByDocKy/pvbrain2/hardware/printable_3d_files/JKBMS_Vertical_Support/Support_JKBMS_1.png

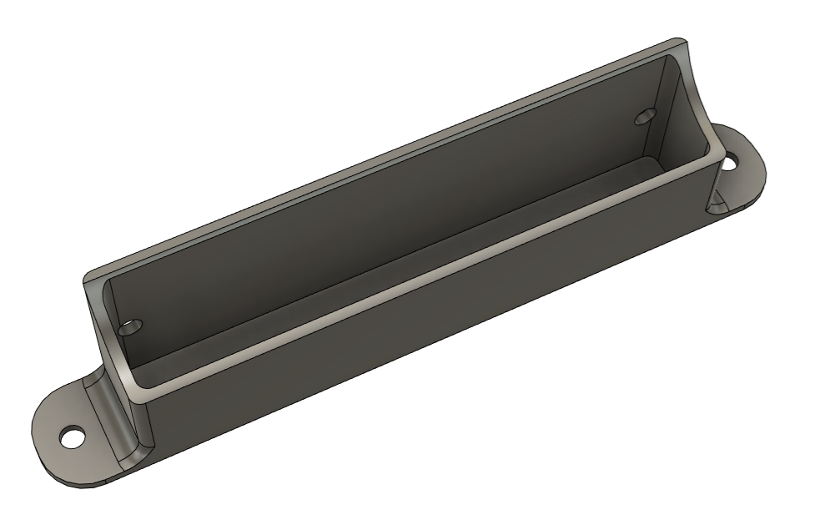
hardware/printable_3d_files/JKBMS_Vertical_Support/Support_JKBMS_1.png
