SeByDocKy/pvbrain2/pvbrain2/inverter/deye/device_deye_tri_nominal.yaml

# ─────────────────────────────────────────────────────────────────────
# device_deye_tri_nominal.yaml — ESPHome 2026.9.0
#   • register_count removed (derived from value_type)
#   • reuse_previous_range: true used to optimise Modbus reads
#   • template numbers migrated to native modbus_controller numbers
#   • modbus_controller::word_from_hex_str → modbus::helpers::word_from_hex_str
#
# Optimised Modbus read ranges (6 total, all holding):
#   Range A:  001       ( 1 reg)  — modbus address
#   Range B:  080–194 (115 regs) — on/off, MPPT, GFDI, battery settings, sell, generator, grid ext, peak shaving, grid status
#   Range C:  213–293  (81 regs) — battery operate, peak shaving power
#   Range D:  340       ( 1 reg)  — max sell power
#   Range E:  500–609 (110 regs) — overall state, battery/grid/load/PV energy stats, temperatures, battery data, grid data
#   Range F:  630–679  (50 regs) — AC output, load, PV power/voltage/current
# ─────────────────────────────────────────────────────────────────────
modbus_controller:
 - id: ${inverter_name}_modbus_controller
   address: ${inverter_modbus_address}
   modbus_id: ${inverter_modbus_id}
   setup_priority: -10
   update_interval: ${inverter_update_interval}

globals:  
  - id: ${inverter_name}_pv_energy_total_yesterday_global
    type: float
    restore_value: yes    
  - id: ${inverter_name}_ac_output_energy_yesterday_global
    type: float
    restore_value: yes
  - id: ${inverter_name}_battery_charging_energy_yesterday_global
    type: float
    restore_value: yes
  - id: ${inverter_name}_battery_discharging_energy_yesterday_global
    type: float
    restore_value: yes

time:
  - platform: homeassistant #sntp
    id: !extend my_time
    on_time:
      - seconds: ${my_second}
        minutes: ${my_minute}
        hours: ${my_hours}
        then:           
          - globals.set:
              id: ${inverter_name}_pv_energy_total_yesterday_global
              value: !lambda return ( id(${inverter_name}_pv_energy_total_yesterday_global) =  float( id(${inverter_name}_pv_energy_total_today).state) );                    
          - globals.set:
              id: ${inverter_name}_ac_output_energy_yesterday_global
              value: !lambda return ( id(${inverter_name}_ac_output_energy_yesterday_global) =  float( id(${inverter_name}_ac_output_energy_today).state) );
          - globals.set:
              id: ${inverter_name}_battery_charging_energy_yesterday_global
              value: !lambda return ( id(${inverter_name}_battery_charging_energy_yesterday_global) =  float( id(${inverter_name}_battery_charging_energy_today).state) );                 
          - globals.set:
              id: ${inverter_name}_battery_discharging_energy_yesterday_global
              value: !lambda return ( id(${inverter_name}_battery_discharging_energy_yesterday_global) =  float( id(${inverter_name}_battery_discharging_energy_today).state) ); 

binary_sensor:   

  # - platform: modbus_controller          # 28 
    # modbus_controller_id: ${inverter_name}_modbus_controller
    # name: ${name}_${inverter_name}_mppt_multipoint_scanning
    # # id: ${inverter_name}_mppt_multipoint_scanning
    # register_type: holding
    # address: 28
    # bitmask: 0x20       
    
  - platform: modbus_controller          # 80 Switch on/off enable
    modbus_controller_id: ${inverter_name}_modbus_controller
    name: ${name}_${inverter_name}_switch_on_off
    id: ${name}_${inverter_name}_switch_on_off
    register_type: holding
    # value_type: U_WORD
    address: 80
    # skip: 10
  
  # - platform: modbus_controller          # 46 Istland Protection Mode 
    # modbus_controller_id: ${inverter_name}_modbus_controller
    # name: ${name}_${inverter_name}_island_protection_mode
    # id: ${name}_${inverter_name}_island_protection_mode
    # register_type: holding
    # # value_type: U_WORD
    # address: 46
    # # skip: 10
    
  - platform: modbus_controller          # 84 MPPT number 
    modbus_controller_id: ${inverter_name}_modbus_controller
    name: ${name}_${inverter_name}_mppt_number
    id: ${name}_${inverter_name}_mppt_number
    register_type: holding
    # value_type: U_WORD
    address: 84
    reuse_previous_range: true

  - platform: modbus_controller          # 85 GFDI mode
    modbus_controller_id: ${inverter_name}_modbus_controller
    name: ${name}_${inverter_name}_GFDI_mode
    id: ${name}_${inverter_name}_GFDI_mode
    register_type: holding
    # value_type: U_WORD
    address: 85
    reuse_previous_range: true
    # skip: 10
    
  - platform: modbus_controller            # 194 Grid Connected Status
    modbus_controller_id: ${inverter_name}_modbus_controller
    name: ${name}_${inverter_name}_grid_connected_status
    id: ${inverter_name}_grid_connected_status
    register_type: holding
    address: 194  
    reuse_previous_range: true

sensor:

  - platform: modbus_controller            # 01 Modbus address
    modbus_controller_id: ${inverter_name}_modbus_controller
    name: ${name}_${inverter_name}_modbus_address
    id: ${inverter_name}_modbus_address
    register_type: holding
    value_type: U_WORD
    address: 01
    # filters:
      # - offset: 1
    
  # - platform: modbus_controller            # 55/01 Limiter
    # modbus_controller_id: ${inverter_name}_modbus_controller
    # name: ${name}_${inverter_name}_limiter
    # id: ${inverter_name}_limiter
    # register_type: holding
    # value_type: U_WORD
    # unit_of_measurement: 'W'
    # accuracy_decimals: 2
    # device_class: power
    # address: 55 
  
      #### battery statistics 
      
  - platform: template
    name: ${name}_${inverter_name}_battery_charging_current
    id: ${inverter_name}_battery_charging_current
    unit_of_measurement: 'A'
    accuracy_decimals: 2
    update_interval: ${inverter_template_update}
    icon: mdi:current-dc  
    lambda: |-
      if (id(${inverter_name}_battery_current).state >= 0) {
        return (id(${inverter_name}_battery_current).state );
      }
      else{
       return 0.0;
      }      
      
  - platform: template
    name: ${name}_${inverter_name}_battery_charging_power
    id: ${inverter_name}_battery_charging_power
    unit_of_measurement: 'W'
    accuracy_decimals: 2
    update_interval: ${inverter_template_update}
    icon: mdi:power  
    lambda: return ( (id(${inverter_name}_battery_voltage).state) * (id(${inverter_name}_battery_charging_current).state) );
   
  - platform: modbus_controller            # 514 Battery Charge TpDay
    modbus_controller_id: ${inverter_name}_modbus_controller
    name: ${name}_${inverter_name}_battery_charging_energy_today
    id: ${inverter_name}_battery_charging_energy_today
    register_type: holding
    address: 514
    reuse_previous_range: true
    unit_of_measurement: 'kWh'
    accuracy_decimals: 1
    device_class: energy
    state_class: total_increasing
    value_type: U_WORD
    filters:
      - multiply: 0.1
      
  - platform: template
    name: ${name}_${inverter_name}_battery_charging_energy_yesterday
    id: ${inverter_name}_battery_charging_energy_yesterday
    unit_of_measurement: 'kWh'
    accuracy_decimals: 1
    icon: mdi:counter
    update_interval: ${inverter_template_update}
    lambda: |-
      return ( id(${inverter_name}_battery_charging_energy_yesterday).state = id(${inverter_name}_battery_charging_energy_yesterday_global) );    

  - platform: template
    name: ${name}_${inverter_name}_battery_discharging_current
    id: ${inverter_name}_battery_discharging_current
    unit_of_measurement: 'A'
    accuracy_decimals: 2
    update_interval: ${inverter_template_update}
    icon: mdi:current-dc  
    lambda: |-
      if (id(${inverter_name}_battery_current).state < 0) {
        return ( - id(${inverter_name}_battery_current).state );
      }
      else{
       return 0.0;
      }

  - platform: template
    name: ${name}_${inverter_name}_battery_discharging_power
    id: ${inverter_name}_battery_discharging_power
    unit_of_measurement: 'W'
    accuracy_decimals: 2
    update_interval: ${inverter_template_update}
    icon: mdi:power  
    lambda: return ( (id(${inverter_name}_battery_voltage).state) * (id(${inverter_name}_battery_discharging_current).state) );

  - platform: modbus_controller            # 515 Battery Discharge TpDay
    modbus_controller_id: ${inverter_name}_modbus_controller
    name: ${name}_${inverter_name}_battery_discharging_energy_today
    id: ${inverter_name}_battery_discharging_energy_today
    register_type: holding
    address: 515
    reuse_previous_range: true
    unit_of_measurement: 'kWh'
    icon: mdi:counter
    accuracy_decimals: 1
    device_class: energy
    state_class: total_increasing
    value_type: U_WORD
    filters:
      - multiply: 0.1
      
  - platform: template
    name: ${name}_${inverter_name}_battery_discharging_energy_yesterday
    id: ${inverter_name}_battery_discharging_energy_yesterday
    unit_of_measurement: 'kWh'
    accuracy_decimals: 1
    icon: mdi:counter
    update_interval: ${inverter_template_update}
    lambda: |-
      return ( id(${inverter_name}_battery_discharging_energy_yesterday).state = id(${inverter_name}_battery_discharging_energy_yesterday_global) );      

  - platform: modbus_controller            # 516 Battery Charge Energy Total
    modbus_controller_id: ${inverter_name}_modbus_controller
    name: ${name}_${inverter_name}_battery_charging_total
    id: ${inverter_name}_battery_charging_total
    register_type: holding
    address: 516
    reuse_previous_range: true
    unit_of_measurement: 'kWh'
    icon: mdi:counter
    accuracy_decimals: 1
    device_class: energy
    state_class: total_increasing
    value_type: U_DWORD_R
    filters:
     - multiply: 0.1

  - platform: modbus_controller            # 518 Battery Discharge Energy Total
    modbus_controller_id: ${inverter_name}_modbus_controller
    name: ${name}_${inverter_name}_battery_discharging_total
    id: ${inverter_name}_battery_discharging_total
    register_type: holding
    address: 518
    reuse_previous_range: true
    unit_of_measurement: 'kWh'
    accuracy_decimals: 1
    device_class: energy
    state_class: total_increasing
    value_type: U_DWORD_R
    filters:
     - multiply: 0.1
     
    ########### Battery  #############
    
  - platform: modbus_controller            # 586 Battery Temperature
    modbus_controller_id: ${inverter_name}_modbus_controller
    name: ${name}_${inverter_name}_battery_temperature
    id: ${inverter_name}_battery_temperature
    register_type: holding
    address: 586
    reuse_previous_range: true
    unit_of_measurement: '°C'
    icon: mdi:thermometer
    accuracy_decimals: 1
    device_class: temperature
    state_class: measurement
    value_type: U_WORD 
    filters:
      - offset: -1000
      - multiply: 0.1

  - platform: modbus_controller            # 587 Battery Voltage
    modbus_controller_id: ${inverter_name}_modbus_controller
    name: ${name}_${inverter_name}_battery_voltage
    id: ${inverter_name}_battery_voltage
    register_type: holding
    address: 587
    reuse_previous_range: true
    unit_of_measurement: 'V'
    icon: mdi:sine-wave
    accuracy_decimals: 1
    device_class: voltage
    state_class: measurement
    filters:
      - multiply: 0.01
    value_type: U_WORD

  - platform: modbus_controller            # 588 Battery SOC
    modbus_controller_id: ${inverter_name}_modbus_controller
    name: ${name}_${inverter_name}_battery_soc
    id: ${inverter_name}_battery_soc
    register_type: holding
    address: 588
    reuse_previous_range: true
    unit_of_measurement: '%'
    icon: mdi:percent
    accuracy_decimals: 0
    device_class: battery
    value_type: U_WORD
    
  - platform: modbus_controller            # 590 Battery Output Power
    modbus_controller_id: ${inverter_name}_modbus_controller
    name: ${name}_${inverter_name}_battery_power
    id: ${inverter_name}_battery_power
    register_type: holding
    address: 590
    reuse_previous_range: true
    unit_of_measurement: 'W'
    icon: mdi:power
    accuracy_decimals: 2
    device_class: power
    value_type: S_WORD
    filters:
      - multiply: -1

  - platform: modbus_controller            # 591 Battery Output Current
    modbus_controller_id: ${inverter_name}_modbus_controller
    name: ${name}_${inverter_name}_battery_current
    id: ${inverter_name}_battery_current
    register_type: holding
    address: 591
    reuse_previous_range: true
    unit_of_measurement: 'A'
    accuracy_decimals: 2
    icon: mdi:current-dc
    device_class: current
    state_class: measurement
    value_type: S_WORD
    filters:
      - multiply: -0.01
 
  - platform: modbus_controller           # 99 Battery Equalization Voltage
    modbus_controller_id: ${inverter_name}_modbus_controller
    # icon: mdi:battery
    name: ${name}_${inverter_name}_battery_equalization_voltage
    id: ${inverter_name}_battery_equalization_voltage
    address: 99
    reuse_previous_range: true
    unit_of_measurement: 'V'
    icon: mdi:sine-wave
    register_type: holding
    value_type: U_WORD
    accuracy_decimals: 1
    device_class: voltage
    state_class: measurement
    filters:
      - multiply: 0.01
 
  - platform: modbus_controller         # 108 Battery Max Charge current
    modbus_controller_id: ${inverter_name}_modbus_controller
    name: ${name}_${inverter_name}_battery_max_charge_current
    register_type: holding
    unit_of_measurement: 'A'
    icon: mdi:current-dc
    accuracy_decimals: 0
    device_class: current
    address: 108
    reuse_previous_range: true
    value_type: U_WORD
    
  - platform: modbus_controller         # 109 Battery Max Discharge current
    modbus_controller_id: ${inverter_name}_modbus_controller
    name: ${name}_${inverter_name}_battery_max_discharge_current
    register_type: holding
    unit_of_measurement: 'A'
    icon: mdi:current-dc
    accuracy_decimals: 0
    device_class: current
    address: 109
    reuse_previous_range: true
    value_type: U_WORD

  - platform: modbus_controller         # 126 Grid Charge Starting Voltage
    modbus_controller_id: ${inverter_name}_modbus_controller
    name: ${name}_${inverter_name}_grid_charge_starting_voltage
    register_type: holding
    address: 126
    reuse_previous_range: true
    unit_of_measurement: 'V'
    icon: mdi:sine-wave
    value_type: U_WORD
    accuracy_decimals: 1
    device_class: voltage
    state_class: measurement
    filters:
      - multiply: 0.01     
    
  - platform: modbus_controller         # 128 Grid Charge Battery current
    modbus_controller_id: ${inverter_name}_modbus_controller
    name: ${name}_${inverter_name}_grid_charge_battery_current
    register_type: holding
    unit_of_measurement: 'A'
    icon: mdi:current-dc
    accuracy_decimals: 0
    device_class: current
    address: 128
    reuse_previous_range: true
    value_type: U_WORD
       
      
 
  - platform: modbus_controller          # 100 Battery Absorption Voltage
    modbus_controller_id: ${inverter_name}_modbus_controller
    name: ${name}_${inverter_name}_battery_absorption_voltage
    id: ${inverter_name}_battery_absorption_voltage
    address: 100
    reuse_previous_range: true
    unit_of_measurement: 'V'
    icon: mdi:sine-wave
    register_type: holding
    value_type: U_WORD
    accuracy_decimals: 1
    device_class: voltage
    state_class: measurement
    filters:
      - multiply: 0.01

  - platform: modbus_controller            # 101 Battery Float Voltage
    modbus_controller_id: ${inverter_name}_modbus_controller
    name: ${name}_${inverter_name}_battery_float_voltage
    id: ${inverter_name}_battery_float_voltage
    address: 101
    reuse_previous_range: true
    unit_of_measurement: 'V'
    icon: mdi:sine-wave
    register_type: holding
    value_type: U_WORD
    accuracy_decimals: 1
    device_class: voltage
    state_class: measurement
    filters:
      - multiply: 0.01
      
  - platform: modbus_controller            # 115 Battery Capacity Shutdown
    modbus_controller_id: ${inverter_name}_modbus_controller
    name: ${name}_${inverter_name}_battery_capacity_shutdown
    id: ${inverter_name}_battery_capacity_shutdown
    register_type: holding
    address: 115
    reuse_previous_range: true
    unit_of_measurement: '%'
    icon: mdi:percent
    accuracy_decimals: 0
    device_class: battery

  - platform: modbus_controller           # 118 Battery Shuntdown Voltage
    modbus_controller_id: ${inverter_name}_modbus_controller
    name: ${name}_${inverter_name}_battery_shutdown_voltage
    id: ${inverter_name}_battery_shutdown_voltage
    address: 118
    reuse_previous_range: true
    unit_of_measurement: 'V'
    icon: mdi:sine-wave
    register_type: holding
    value_type: U_WORD
    accuracy_decimals: 1
    device_class: voltage
    state_class: measurement
    filters:
      - multiply: 0.01

  - platform: modbus_controller          # 120 Battery Low Voltage
    modbus_controller_id: ${inverter_name}_modbus_controller
    name: ${name}_${inverter_name}_battery_low_voltage
    id: ${inverter_name}_battery_low_voltage
    address: 120
    reuse_previous_range: true
    unit_of_measurement: 'V'
    icon: mdi:sine-wave
    register_type: holding
    value_type: U_WORD
    accuracy_decimals: 1
    device_class: voltage
    state_class: measurement
    filters:
      - multiply: 0.01    
     
     ##### Grid data & statistics ####
     
  - platform: modbus_controller            # 520 Grid Import Today (Buy)
    modbus_controller_id: ${inverter_name}_modbus_controller
    name: ${name}_${inverter_name}_grid_energy_imported_today
    id: ${inverter_name}_grid_energy_imported_today
    register_type: holding
    address: 520
    reuse_previous_range: true
    unit_of_measurement: 'kWh'
    icon: mdi:counter
    accuracy_decimals: 1
    device_class: energy
    state_class: total_increasing
    value_type: U_WORD
    filters:
      - multiply: 0.1
      
  - platform: modbus_controller            # 521 Grid Export Today (Sell)
    modbus_controller_id: ${inverter_name}_modbus_controller
    name: ${name}_${inverter_name}_grid_energy_exported_today
    id: ${inverter_name}_grid_energy_exported_today
    register_type: holding
    address: 521
    reuse_previous_range: true
    unit_of_measurement: 'kWh'
    icon: mdi:counter
    accuracy_decimals: 1
    device_class: energy
    state_class: total_increasing
    value_type: U_WORD
    filters:
      - multiply: 0.1    
     
  - platform: modbus_controller            # 522 Grid Import Energy Total (Buy)
    modbus_controller_id: ${inverter_name}_modbus_controller
    name: ${name}_${inverter_name}_grid_energy_imported_total
    id: ${inverter_name}_grid_energy_imported_total
    register_type: holding
    address: 522
    reuse_previous_range: true
    unit_of_measurement: 'kWh'
    accuracy_decimals: 1
    icon: mdi:counter
    device_class: energy
    state_class: total_increasing
    value_type: U_DWORD_R
    filters:
      - multiply: 0.1  
    
  - platform: modbus_controller            # 524 Grid Export Energy Total (Sell)
    modbus_controller_id: ${inverter_name}_modbus_controller
    name: ${name}_${inverter_name}_grid_energy_exported_total
    id: ${inverter_name}_grid_energy_exported_total
    register_type: holding
    address: 524
    reuse_previous_range: true
    unit_of_measurement: 'kWh'
    accuracy_decimals: 1
    icon: mdi:counter
    device_class: energy
    state_class: total_increasing
    value_type: U_DWORD_R
    filters:
      - multiply: 0.1

  - platform: modbus_controller            # 609 Grid Frequency
    modbus_controller_id: ${inverter_name}_modbus_controller
    name: ${name}_${inverter_name}_grid_frequency
    id: ${inverter_name}_grid_frequency
    register_type: holding
    address: 609
    reuse_previous_range: true
    unit_of_measurement: 'Hz'
    icon: mdi:sine-wave
    accuracy_decimals: 2
    filters:
      - multiply: 0.01
    value_type: U_WORD
    state_class: measurement
    
  - platform: modbus_controller            # 598 Grid phase A Voltage
    modbus_controller_id: ${inverter_name}_modbus_controller
    name: ${name}_${inverter_name}_grid_phaseA_voltage
    id: ${inverter_name}_grid_phaseA_voltage
    register_type: holding
    address: 598
    reuse_previous_range: true
    unit_of_measurement: 'V'
    icon: mdi:sine-wave
    accuracy_decimals: 1
    device_class: voltage
    state_class: measurement
    filters:
      - multiply: 0.1
    value_type: U_WORD

  - platform: modbus_controller            # 599 Grid phase B Voltage
    modbus_controller_id: ${inverter_name}_modbus_controller
    name: ${name}_${inverter_name}_grid_phaseB_voltage
    id: ${inverter_name}_grid_phaseB_voltage
    register_type: holding
    address: 599
    reuse_previous_range: true
    unit_of_measurement: 'V'
    icon: mdi:sine-wave
    accuracy_decimals: 1
    device_class: voltage
    state_class: measurement
    filters:
      - multiply: 0.1
    value_type: U_WORD
    
  - platform: modbus_controller            # 600 Grid phase C Voltage
    modbus_controller_id: ${inverter_name}_modbus_controller
    name: ${name}_${inverter_name}_grid_phaseC_voltage
    id: ${inverter_name}_grid_phaseC_voltage
    register_type: holding
    address: 600
    reuse_previous_range: true
    unit_of_measurement: 'V'
    icon: mdi:sine-wave
    accuracy_decimals: 1
    device_class: voltage
    state_class: measurement
    filters:
      - multiply: 0.1
    value_type: U_WORD  
    
   

  - platform: modbus_controller             # 604 Grid PhaseA Power
    modbus_controller_id: ${inverter_name}_modbus_controller
    name: ${name}_${inverter_name}_grid_phaseA_power
    id: ${inverter_name}_grid_phaseA_power
    register_type: holding
    address: 604
    reuse_previous_range: true
    unit_of_measurement: 'W'
    icon: mdi:power
    accuracy_decimals: 2
    device_class: power
    state_class: measurement
    value_type: S_WORD
    
  - platform: modbus_controller             # 605 Grid PhaseB Power
    modbus_controller_id: ${inverter_name}_modbus_controller
    name: ${name}_${inverter_name}_grid_phaseB_power
    id: ${inverter_name}_grid_phaseB_power
    register_type: holding
    address: 605
    reuse_previous_range: true
    unit_of_measurement: 'W'
    icon: mdi:power
    accuracy_decimals: 2
    device_class: power
    state_class: measurement
    value_type: S_WORD

  - platform: modbus_controller             # 606 Grid PhaseC Power
    modbus_controller_id: ${inverter_name}_modbus_controller
    name: ${name}_${inverter_name}_grid_phaseC_power
    id: ${inverter_name}_grid_phaseC_power
    register_type: holding
    address: 606
    reuse_previous_range: true
    unit_of_measurement: 'W'
    icon: mdi:power
    accuracy_decimals: 2
    device_class: power
    state_class: measurement
    value_type: S_WORD
    
  - platform: modbus_controller             # 607 Grid Power
    modbus_controller_id: ${inverter_name}_modbus_controller
    name: ${name}_${inverter_name}_grid_power
    id: ${inverter_name}_grid_power
    register_type: holding
    address: 607
    reuse_previous_range: true
    unit_of_measurement: 'W'
    icon: mdi:power
    accuracy_decimals: 2
    device_class: power
    state_class: measurement
    value_type: S_WORD    
    
  - platform: modbus_controller            # 172 Grid External Power
    modbus_controller_id: ${inverter_name}_modbus_controller
    name: ${name}_${inverter_name}_grid_external_power
    id: ${inverter_name}_grid_external_power
    register_type: holding
    address: 172
    reuse_previous_range: true
    unit_of_measurement: 'W'
    icon: mdi:power
    accuracy_decimals: 2
    device_class: power
    state_class: measurement
    value_type: S_WORD
          
  - platform: modbus_controller        # 255 Grid Peak Shaving raw register value
    modbus_controller_id: ${inverter_name}_modbus_controller
    id: ${inverter_name}_grid_peak_shaving_raw
    register_type: holding
    address: 280
    reuse_previous_range: true
    value_type: U_WORD
    
  - platform: modbus_controller            # 293 Grid Peak Shaving Power
    modbus_controller_id: ${inverter_name}_modbus_controller
    name: ${name}_${inverter_name}_grid_peak_shaving_power
    id: ${inverter_name}_grid_peak_shaving_power
    address: 293
    reuse_previous_range: true
    register_type: holding
    value_type: U_WORD
    unit_of_measurement: 'W'
    accuracy_decimals: 2
    device_class: power
    state_class: measurement
    icon: mdi:power   
    
  # - platform: modbus_controller            # 520 Grid Import Energy Today (Buy)
    # modbus_controller_id: ${inverter_name}_modbus_controller
    # name: ${name}_${inverter_name}_grid_energy_imported_today
    # id: ${inverter_name}_grid_energy_imported_today
    # register_type: holding
    # address: 520
    # unit_of_measurement: 'kWh'
    # accuracy_decimals: 1
    # icon: mdi:counter
    # device_class: energy
    # state_class: total_increasing
    # value_type: U_WORD
    # filters:
      # - multiply: 0.1  
    
  # - platform: modbus_controller            # 521 Grid Export Energy Today (Sell)
    # modbus_controller_id: ${inverter_name}_modbus_controller
    # name: ${name}_${inverter_name}_grid_energy_exported_today
    # id: ${inverter_name}_grid_energy_exported_total
    # register_type: holding
    # address: 521
    # unit_of_measurement: 'kWh'
    # accuracy_decimals: 1
    # icon: mdi:counter
    # device_class: energy
    # state_class: total_increasing
    # value_type: U_WORD
    # filters:
      # - multiply: 0.1  
      
 
      
    ####### House load data & statistics  #####  

  - platform: modbus_controller            # 526 Daily Load
    modbus_controller_id: ${inverter_name}_modbus_controller
    name: ${name}_${inverter_name}_load_energy_today
    id: ${inverter_name}_load_energy_today
    register_type: holding
    address: 526
    reuse_previous_range: true
    unit_of_measurement: 'kWh'
    icon: mdi:counter
    accuracy_decimals: 1
    device_class: energy
    state_class: total_increasing
    filters:
      - multiply: 0.1
    value_type: U_WORD
    
  - platform: modbus_controller            # 527 Total Load
    modbus_controller_id: ${inverter_name}_modbus_controller
    name: ${name}_${inverter_name}_load_energy_total
    id: ${inverter_name}_load_energy_total
    register_type: holding
    address: 527
    reuse_previous_range: true
    unit_of_measurement: 'kWh'
    icon: mdi:counter
    accuracy_decimals: 1
    device_class: energy
    state_class: total_increasing
    filters:
      - multiply: 0.1
    value_type: U_DWORD_R  
    
  - platform: modbus_controller            # 644 Load PhaseA voltage
    modbus_controller_id: ${inverter_name}_modbus_controller
    name: ${name}_${inverter_name}_load_phaseA_voltage
    id: ${inverter_name}_load_phaseA_voltage
    register_type: holding
    address: 644
    reuse_previous_range: true
    unit_of_measurement: 'V'
    icon: mdi:sine-wave
    accuracy_decimals: 1
    device_class: voltage
    state_class: measurement
    filters:
      - multiply: 0.1
    value_type: U_WORD

  - platform: modbus_controller            # 644 Load PhaseB voltage
    modbus_controller_id: ${inverter_name}_modbus_controller
    name: ${name}_${inverter_name}_load_phaseB_voltage
    id: ${inverter_name}_load_phaseB_voltage
    register_type: holding
    address: 645
    reuse_previous_range: true
    unit_of_measurement: 'V'
    icon: mdi:sine-wave
    accuracy_decimals: 1
    device_class: voltage
    state_class: measurement
    filters:
      - multiply: 0.1
    value_type: U_WORD

  - platform: modbus_controller            # 646 Load PhaseB voltage
    modbus_controller_id: ${inverter_name}_modbus_controller
    name: ${name}_${inverter_name}_load_phaseC_voltage
    id: ${inverter_name}_load_phaseC_voltage
    register_type: holding
    address: 646
    reuse_previous_range: true
    unit_of_measurement: 'V'
    icon: mdi:sine-wave
    accuracy_decimals: 1
    device_class: voltage
    state_class: measurement
    filters:
      - multiply: 0.1
    value_type: U_WORD    

  # - platform: modbus_controller            # 085 Total Load Power
    # modbus_controller_id: ${inverter_name}_modbus_controller
    # name: ${name}_${inverter_name}_total_load_power
    # id: ${inverter_name}_total_load_power
    # register_type: holding
    # address: 85
    # unit_of_measurement: 'W'
    # icon: mdi:power
    # accuracy_decimals: 2
    # device_class: energy
    # state_class: total_increasing
    # value_type: U_DWORD_R
    # filters:
      # - multiply: 0.1
      
    ###### inverter builtin temperature data ####
    
  - platform: modbus_controller            # 540 DC Transformer Temperature
    modbus_controller_id: ${inverter_name}_modbus_controller
    name: ${name}_${inverter_name}_dc_transformer_temperature
    id: ${inverter_name}_dc_transformer_temperature
    register_type: holding
    address: 540
    reuse_previous_range: true
    unit_of_measurement: '°C'
    icon: mdi:thermometer
    accuracy_decimals: 1
    device_class: temperature
    state_class: measurement
    value_type: S_WORD
    filters:
      - offset: -1000
      - multiply:  0.1

  - platform: modbus_controller            # 541 Radiator Temperature
    modbus_controller_id: ${inverter_name}_modbus_controller
    name: ${name}_${inverter_name}_dc_radiator_temperature
    id: ${inverter_name}_dc_radiator_temperature
    register_type: holding
    address: 541
    reuse_previous_range: true
    unit_of_measurement: '°C'
    icon: mdi:thermometer
    accuracy_decimals: 1
    device_class: temperature
    state_class: measurement
    value_type: S_WORD
    filters:
      - offset: -1000
      - multiply:  0.1
    
      ######## PV statistics   ##########
      
  - platform: modbus_controller            # 529 Day PV Energy
    modbus_controller_id: ${inverter_name}_modbus_controller
    name: ${name}_${inverter_name}_pv_energy_today
    id: ${inverter_name}_pv_energy_today
    register_type: holding
    address: 529
    reuse_previous_range: true
    unit_of_measurement: 'kWh'
    icon: mdi:counter
    accuracy_decimals: 1
    device_class: energy
    state_class: total_increasing
    filters:
      - multiply: 0.1
    value_type: U_WORD

      
  - platform: modbus_controller            # 534 PV Energy Total Power
    modbus_controller_id: ${inverter_name}_modbus_controller
    name: ${name}_${inverter_name}_pv_energy_total
    id: ${inverter_name}_pv_energy_total
    register_type: holding
    address: 534
    reuse_previous_range: true
    unit_of_measurement: 'kWh'
    accuracy_decimals: 1
    icon: mdi:counter
    device_class: energy
    state_class: total_increasing
    filters:
      - multiply: 0.1
    value_type: U_DWORD_R  

        
    ######## PV data ######
    
  - platform: modbus_controller            # 672 PV1 Power
    modbus_controller_id: ${inverter_name}_modbus_controller
    name: ${name}_${inverter_name}_pv1_power
    id: ${inverter_name}_pv1_power
    register_type: holding
    address: 672
    reuse_previous_range: true
    unit_of_measurement: 'W'
    icon: mdi:power
    accuracy_decimals: 2
    device_class: power
    state_class: measurement
    value_type: U_WORD
    
  - platform: modbus_controller            # 673 PV2 Power
    modbus_controller_id: ${inverter_name}_modbus_controller
    name: ${name}_${inverter_name}_pv2_power
    id: ${inverter_name}_pv2_power
    register_type: holding
    address: 673
    reuse_previous_range: true
    unit_of_measurement: 'W'
    icon: mdi:power
    accuracy_decimals: 2
    device_class: power
    state_class: measurement
    value_type: U_WORD

  - platform: template                   # Sum of PV1 and PV2 to get total PV Power
    name: ${name}_${inverter_name}_pv_power_total
    id: ${inverter_name}_pv_power_total
    unit_of_measurement: 'W'
    icon: mdi:power
    accuracy_decimals: 2
    device_class: power
    state_class: measurement
    lambda: |-
      return (id(${inverter_name}_pv1_power).state + id(${inverter_name}_pv2_power).state);
    update_interval: ${inverter_template_update}
    
    
  - platform: modbus_controller            # 676 PV1 Voltage
    modbus_controller_id: ${inverter_name}_modbus_controller
    name: ${name}_${inverter_name}_pv1_voltage
    id: ${inverter_name}_pv1_voltage
    register_type: holding
    address: 676
    reuse_previous_range: true
    unit_of_measurement: 'V'
    icon: mdi:sine-wave
    accuracy_decimals: 1
    device_class: voltage
    state_class: measurement
    filters:
      - multiply: 0.1
    value_type: U_WORD
    
  - platform: modbus_controller            # 677 PV1 Output Current
    modbus_controller_id: ${inverter_name}_modbus_controller
    name: ${name}_${inverter_name}_pv1_current
    id: ${inverter_name}_pv1_current
    register_type: holding
    address: 677
    reuse_previous_range: true
    unit_of_measurement: 'A'
    accuracy_decimals: 2
    icon: mdi:current-dc
    device_class: current
    state_class: measurement
    filters:
      - multiply: 0.1
    value_type: U_WORD
    

  - platform: modbus_controller            # 678 PV2 Voltage
    modbus_controller_id: ${inverter_name}_modbus_controller
    name: ${name}_${inverter_name}_pv2_voltage
    id: ${inverter_name}_pv2_voltage
    register_type: holding
    address: 678
    reuse_previous_range: true
    unit_of_measurement: 'V'
    icon: mdi:sine-wave
    filters:
      - multiply: 0.1
    accuracy_decimals: 1
    device_class: voltage
    state_class: measurement
    value_type: U_WORD


  - platform: modbus_controller            # 679 PV2 Output Current
    modbus_controller_id: ${inverter_name}_modbus_controller
    name: ${name}_${inverter_name}_pv2_current
    id: ${inverter_name}_pv2_current
    register_type: holding
    address: 679
    reuse_previous_range: true
    unit_of_measurement: 'A'
    icon: mdi:current-dc
    accuracy_decimals: 2
    device_class: current
    state_class: measurement
    filters:
      - multiply: 0.1
    value_type: U_WORD
    
   
  - platform: total_daily_energy
    name: ${name}_${inverter_name}_pv_energy_total_today
    id: ${inverter_name}_pv_energy_total_today
    power_id: ${inverter_name}_pv_power_total
    unit_of_measurement: 'kWh'
    icon: mdi:counter
    accuracy_decimals: 1
    method: trapezoid
    filters:
       # Multiplication factor from W to kW is 0.001
       - multiply: 0.001
    
  - platform: template
    name: ${name}_${inverter_name}_pv_energy_total_yesterday
    id: ${inverter_name}_pv_energy_total_yesterday
    unit_of_measurement: 'kWh'
    icon: mdi:counter
    accuracy_decimals: 1
    update_interval: ${inverter_template_update}
    lambda: |-
      return ( id(${inverter_name}_pv_energy_total_yesterday).state = id(${inverter_name}_pv_energy_total_yesterday_global) );  
   
  - platform: total_daily_energy
    name: ${name}_${inverter_name}_ac_output_energy_today
    id: ${inverter_name}_ac_output_energy_today
    power_id: ${inverter_name}_ac_output_power
    unit_of_measurement: 'kWh'
    icon: mdi:counter
    accuracy_decimals: 1   
    method: trapezoid
    filters:
       # Multiplication factor from W to kW is 0.001
       - multiply: 0.001

    
  - platform: template
    name: ${name}_${inverter_name}_ac_output_energy_yesterday
    id: ${inverter_name}_ac_output_energy_yesterday
    unit_of_measurement: 'kWh'
    accuracy_decimals: 1
    icon: mdi:counter
    update_interval: ${inverter_template_update}
    lambda: |-
      return ( id(${inverter_name}_ac_output_energy_yesterday).state = id(${inverter_name}_ac_output_energy_yesterday_global) );  
    
   ############### ACout & aux data & statistics  #####
 
  - platform: modbus_controller            # 630 Inverter Output PhaseA Current
    modbus_controller_id: ${inverter_name}_modbus_controller
    name: ${name}_${inverter_name}_ac_output_phaseA_current
    id: ${inverter_name}_ac_output_phaseA_current
    register_type: holding
    address: 630
    unit_of_measurement: 'A'
    icon: mdi:current-dc
    accuracy_decimals: 2
    device_class: current
    state_class: measurement
    value_type: S_WORD
    filters:
      - multiply: 0.01
      
  - platform: modbus_controller            # 631 Inverter Output PhaseB Current
    modbus_controller_id: ${inverter_name}_modbus_controller
    name: ${name}_${inverter_name}_ac_output_phaseB_current
    id: ${inverter_name}_ac_output_phaseB_current
    register_type: holding
    address: 631
    reuse_previous_range: true
    unit_of_measurement: 'A'
    icon: mdi:current-dc
    accuracy_decimals: 2
    device_class: current
    state_class: measurement
    value_type: S_WORD
    filters:
      - multiply: 0.01

  - platform: modbus_controller            # 632 Inverter Output PhaseC Current
    modbus_controller_id: ${inverter_name}_modbus_controller
    name: ${name}_${inverter_name}_ac_output_phaseC_current
    id: ${inverter_name}_ac_output_phaseC_current
    register_type: holding
    address: 632
    reuse_previous_range: true
    unit_of_measurement: 'A'
    icon: mdi:current-dc
    accuracy_decimals: 2
    device_class: current
    state_class: measurement
    value_type: S_WORD
    filters:
      - multiply: 0.01      
      
  # - platform: modbus_controller            # 166 Aux Output Power
    # modbus_controller_id: ${inverter_name}_modbus_controller
    # name: ${name}_${inverter_name}_aux_output_power
    # id: ${inverter_name}_aux_output_power
    # register_type: holding
    # address: 166
    # unit_of_measurement: 'W'
    # icon: mdi:power
    # accuracy_decimals: 2
    # device_class: power
    # state_class: measurement
    # value_type: S_WORD
   
  - platform: modbus_controller            # 636 Inverter Output Power
    modbus_controller_id: ${inverter_name}_modbus_controller
    name: ${name}_${inverter_name}_ac_output_power
    id: ${inverter_name}_ac_output_power
    register_type: holding
    address: 636
    reuse_previous_range: true
    unit_of_measurement: 'W'
    icon: mdi:power
    accuracy_decimals: 2
    device_class: power
    value_type: S_WORD

  - platform: modbus_controller            # 653 Load Power
    modbus_controller_id: ${inverter_name}_modbus_controller
    name: ${name}_${inverter_name}_load_power
    id: ${inverter_name}_load_power
    register_type: holding
    address: 653
    reuse_previous_range: true
    unit_of_measurement: 'W'
    icon: mdi:power
    accuracy_decimals: 2
    device_class: power
    state_class: measurement
    value_type: S_WORD
    
  - platform: modbus_controller            # 655 Load Frequency
    modbus_controller_id: ${inverter_name}_modbus_controller
    name: ${name}_${inverter_name}_load_frequency
    id: ${inverter_name}_load_frequency
    register_type: holding
    address: 655
    reuse_previous_range: true
    unit_of_measurement: 'Hz'
    icon: mdi:sine-wave
    accuracy_decimals: 2
    filters:
      - multiply: 0.01
    value_type: U_WORD
    state_class: measurement
    
  - platform: modbus_controller            # 638 AC output Frequency
    modbus_controller_id: ${inverter_name}_modbus_controller
    name: ${name}_${inverter_name}_ac_output_frequency
    id: ${inverter_name}_ac_output_frequency
    register_type: holding
    address: 638
    reuse_previous_range: true
    unit_of_measurement: 'Hz'
    icon: mdi:alpha-Hz-circle-outline
    accuracy_decimals: 2
    filters:
      - multiply: 0.01
    value_type: U_WORD
    state_class: measurement

  # - platform: modbus_controller            # 194 Grid connexion
    # modbus_controller_id: ${inverter_name}_modbus_controller
    # name: ${name}_${inverter_name}_grid_connexion
    # id: ${inverter_name}_grid_connexion
    # register_type: holding
    # address: 194
    # accuracy_decimals: 0
    # value_type: U_WORD
    # state_class: measurement    
    
  # - platform: template                   # Essential Power based on register 175 + 167 -166
    # name: ${name}_${inverter_name}_essential_power
    # unit_of_measurement: 'W'
    # accuracy_decimals: 2
    # device_class: power
    # icon: mdi:power
    # state_class: measurement
    # lambda: |-
      # return (id(${inverter_name}_ac_output_power).state + id(${inverter_name}_grid_power_167).state - id(${inverter_name}_aux_output_power).state);
    # update_interval: ${inverter_template_update}

  # - platform: template                   # Essential Power based on register 175 + 169 -166
    # name: ${name}_${inverter_name}_essential_power_1
    # unit_of_measurement: 'W'
    # accuracy_decimals: 2
    # icon: mdi:power
    # device_class: power
    # state_class: measurement
    # lambda: |-
      # return (id(${inverter_name}_ac_output_power).state + id(${inverter_name}_grid_power).state - id(${inverter_name}_aux_output_power).state);
    # update_interval: ${inverter_template_update}

  # - platform: template                   # Nonessential Power 175 - 167
    # name: ${name}_${inverter_name}_nonessential_power
    # unit_of_measurement: 'W'
    # icon: mdi:power
    # accuracy_decimals: 2
    # device_class: power
    # state_class: measurement
    # lambda: |-
      # return (id(${inverter_name}_grid_external_power).state - id(${inverter_name}_grid_power_167).state);
    # update_interval: ${inverter_template_update}

  # - platform: template                   # Nonessential Power 175 - 169
    # name: ${name}_${inverter_name}_nonessential_power_1
    # unit_of_measurement: 'W'
    # icon: mdi:power
    # accuracy_decimals: 2
    # device_class: power
    # state_class: measurement
    # lambda: |-
      # return (id(${inverter_name}_grid_external_power).state - id(${inverter_name}_grid_power).state);
    # update_interval: ${inverter_template_update}
    
switch:

  # - platform: modbus_controller          # 28 
    # use_write_multiple: true
    # modbus_controller_id: ${inverter_name}_modbus_controller
    # name: ${name}_${inverter_name}_low_power_mode
    # id: ${inverter_name}_low_power_mode
    # register_type: holding
    # address: 28
    # bitmask: 0x04
    # icon: mdi:toggle-switch
    
  # - platform: modbus_controller          # 28 
    # use_write_multiple: true
    # modbus_controller_id: ${inverter_name}_modbus_controller
    # name: ${name}_${inverter_name}_mppt_multipoint_scanning
    # id: ${inverter_name}_mppt_multipoint_scanning
    # register_type: holding
    # address: 28
    # bitmask: 0X20
    # icon: mdi:toggle-switch
    
  # - platform: modbus_controller          #34 
    # use_write_multiple: true
    # modbus_controller_id: ${inverter_name}_modbus_controller
    # name: ${name}_${inverter_name}_low_noise_mode
    # id: ${inverter_name}_low_noise_mode
    # register_type: holding
    # address: 34
    # bitmask: 0x01
    # icon: mdi:toggle-switch  
  

  - platform: modbus_controller          # 145 Toggle Solar Sell
    use_write_multiple: true
    modbus_controller_id: ${inverter_name}_modbus_controller
    name: ${name}_${inverter_name}_toggle_solar_sell
    id: ${inverter_name}_toggle_solar_sell
    register_type: holding
    address: 145
    reuse_previous_range: true
    bitmask: 0x01
    entity_category: config
    icon: mdi:toggle-switch
    
  - platform: modbus_controller          # 132 Toggle Force Generator
    use_write_multiple: true
    modbus_controller_id: ${inverter_name}_modbus_controller
    name: ${name}_${inverter_name}_toggle_force_generator
    id: ${inverter_name}_toggle_force_generator
    register_type: holding
    address: 132
    reuse_previous_range: true
    bitmask: 0x01
    icon: mdi:toggle-switch 

number:

  - platform: modbus_controller                     # 99 Battery Equalization Voltage
    use_write_multiple: true
    modbus_controller_id: ${inverter_name}_modbus_controller
    name: ${name}_${inverter_name}_battery_equalization_voltage
    id: ${inverter_name}_battery_equalization_voltage_number
    register_type: holding
    address: 99
    reuse_previous_range: true
    value_type: U_WORD
    unit_of_measurement: 'V'
    icon: mdi:sine-wave
    #multiply: 0.01
    multiply: 100
    min_value: 50.00
    max_value: 61.00
    step: 0.1
    mode: 'slider'
    
  - platform: modbus_controller                     # 100 Battery Absorption Voltage
    use_write_multiple: true
    modbus_controller_id: ${inverter_name}_modbus_controller
    name: ${name}_${inverter_name}_battery_absorption_voltage
    id: ${inverter_name}_battery_absorption_voltage_number
    register_type: holding
    address: 100
    reuse_previous_range: true
    value_type: U_WORD
    unit_of_measurement: 'V'
    icon: mdi:sine-wave
    #multiply: 0.01
    multiply: 100
    min_value: 50.00
    max_value: 61.00
    step: 0.1
    mode: 'slider'
    
  - platform: modbus_controller                     # 101 Battery Float Voltage
    use_write_multiple: true
    modbus_controller_id: ${inverter_name}_modbus_controller
    name: ${name}_${inverter_name}_battery_float_voltage
    id: ${inverter_name}_battery_float_voltage_number
    register_type: holding
    address: 101
    reuse_previous_range: true
    value_type: U_WORD
    unit_of_measurement: 'V'
    icon: mdi:sine-wave
    #multiply: 0.01
    multiply: 100
    min_value: 50.00
    max_value: 61.00
    step: 0.1
    mode: 'slider'
    
  - platform: modbus_controller                     # 118 Battery Shuntdown Voltage
    use_write_multiple: true
    modbus_controller_id: ${inverter_name}_modbus_controller
    name: ${name}_${inverter_name}_battery_shuntdown_voltage
    id: ${inverter_name}_battery_shuntdown_voltage_number
    register_type: holding
    address: 118
    reuse_previous_range: true
    value_type: U_WORD
    unit_of_measurement: 'V'
    icon: mdi:sine-wave
    #multiply: 0.01
    multiply: 100
    min_value: 40.00
    max_value: 52.00
    step: 0.1
    mode: 'slider'
    
  - platform: modbus_controller                     # 120 Battery Low Voltage
    use_write_multiple: true
    modbus_controller_id: ${inverter_name}_modbus_controller
    name: ${name}_${inverter_name}_battery_low_voltage
    id: ${inverter_name}_battery_low_voltage_number
    register_type: holding
    address: 120
    reuse_previous_range: true
    value_type: U_WORD
    unit_of_measurement: 'V'
    icon: mdi:sine-wave
    #multiply: 0.01
    multiply: 100
    min_value: 40.00
    max_value: 52.00
    step: 0.1
    mode: 'slider'
    
  - platform: modbus_controller                     # 126 Grid Charge Starting Voltage
    use_write_multiple: true
    modbus_controller_id: ${inverter_name}_modbus_controller
    name: ${name}_${inverter_name}_grid_charge_starting_voltage
    id: ${inverter_name}_grid_charge_starting_voltage_number
    register_type: holding
    address: 126
    reuse_previous_range: true
    value_type: U_WORD
    unit_of_measurement: 'V'
    icon: mdi:sine-wave
    #multiply: 0.01
    multiply: 100
    min_value: 44.00
    max_value: 53.00
    step: 0.1
    mode: 'slider'
    
  - platform: modbus_controller         # 108 Battery Max Charge current
    use_write_multiple: true
    modbus_controller_id: ${inverter_name}_modbus_controller
    name: ${name}_${inverter_name}_battery_max_charge_current
    id: ${inverter_name}_battery_max_charge_current_number
    unit_of_measurement: 'A'
    icon: mdi:current-dc
    address: 108
    reuse_previous_range: true
    value_type: U_WORD
    min_value: 5
    max_value: 185
    step: 5
    mode: 'slider'
      
  - platform: modbus_controller         # 109 Battery Max Discharge current
    use_write_multiple: true
    modbus_controller_id: ${inverter_name}_modbus_controller
    name: ${name}_${inverter_name}_battery_max_discharge_current
    id: ${inverter_name}_battery_max_discharge_current_number
    unit_of_measurement: 'A'
    icon: mdi:current-dc
    address: 109
    reuse_previous_range: true
    value_type: U_WORD
    min_value: 0
    max_value: 185
    step: 5
    mode: 'slider'
      
  - platform: modbus_controller         # 128 Grid Charge Battery current
    use_write_multiple: true
    modbus_controller_id: ${inverter_name}_modbus_controller
    name: ${name}_${inverter_name}_grid_charge_battery_current
    id: ${inverter_name}_grid_charge_battery_current_number
    unit_of_measurement: 'A'
    icon: mdi:current-dc
    address: 128
    reuse_previous_range: true
    value_type: U_WORD
    min_value: 0
    max_value: 185
    step: 5
    mode: 'slider'

  - platform: modbus_controller            # 340 Max Sell Power
    use_write_multiple: true
    modbus_controller_id: ${inverter_name}_modbus_controller
    name: ${name}_${inverter_name}_max_sell_power
    id: ${inverter_name}_max_sell_power_number
    address: 340
    value_type: U_WORD
    unit_of_measurement: 'W'
    min_value: 0
    max_value: 8000
    step: 500
    mode: 'slider'
    
  - platform: modbus_controller            # 191 Grid Peak Shaving Power
    use_write_multiple: true
    modbus_controller_id: ${inverter_name}_modbus_controller
    name: ${name}_${inverter_name}_grid_peak_shaving_power
    id: ${inverter_name}_grid_peak_shaving_power_number
    address: 191
    reuse_previous_range: true
    value_type: U_WORD
    unit_of_measurement: 'W'
    icon: mdi:power
    min_value: 0
    max_value: 8000
    step: 500
    mode: 'slider'
    
    
select:

  - platform: modbus_controller
    use_write_multiple: true
    modbus_controller_id: ${inverter_name}_modbus_controller
    name: ${name}_${inverter_name}_switch_on_off
    id: ${inverter_name}_switch_on_off_select
    address: 80
    value_type: S_WORD
    optionsmap:
      "OFF": 0
      "ON": 1
    # skip_updates: 10
  
  - platform: modbus_controller                   #243 Select Energy Pattern
    use_write_multiple: true
    modbus_controller_id: ${inverter_name}_modbus_controller
    name: ${name}_${inverter_name}_battery_operate
    id: ${inverter_name}_battery_operate
    address: 213
    value_type: U_WORD
    optionsmap:
      "According to the voltage": 0
      "According to the capacity": 1
      "No battery": 2
  
  - platform: modbus_controller                   #141 Select Energy Pattern
    use_write_multiple: true
    modbus_controller_id: ${inverter_name}_modbus_controller
    name: ${name}_${inverter_name}_energy_pattern
    id: ${inverter_name}_energy_pattern
    address: 141
    reuse_previous_range: true
    value_type: U_WORD
    optionsmap:
      "Battery first": 0
      "Load first": 1   
         
  # - platform: modbus_controller                   #244 Select Work Mode
    # use_write_multiple: true
    # modbus_controller_id: ${inverter_name}_modbus_controller
    # name: ${name}_${inverter_name}_work_mode
    # id: ${inverter_name}_work_mode
    # address: 244
    # value_type: U_WORD
    # optionsmap:
      # "Selling First": 0
      # "Zero Export + Limit to Load Only": 1
      # "Limited to Home": 2    

  # - platform: modbus_controller                  #280 Select Grid Peak Shaving
    # use_write_multiple: true
    # modbus_controller_id: ${inverter_name}_modbus_controller
    # name: ${name}_${inverter_name}_grid_peak_shaving
    # id: ${inverter_name}_grid_peak_shaving_select
    # address: 280
    # value_type: U_WORD
    # optionsmap:
      # "Disabled": 0
      # "Enabled": 256
    # lambda: |-
      # // we are only interested in the 8th bit binary 0001 0000 0000 need to map the options 0, 256 in select 
      # //ESP_LOGE("main","Modbus Number incoming value = %d",x);
      # //ESP_LOGE("main","Modbus eval value = %d",(x & 0x0100));
      # if ((x & 0x0100) == 0)
        # return  std::string("Disabled");
      # if ((x & 0x0100) == 256)
        # return  std::string("Enabled");
      # return {};
    # write_lambda: |-
      # //ESP_LOGE("main","Modbus write gets = %d",value);
      # uint16_t unmodified =  id(${inverter_name}_grid_peak_shaving_raw).state;
      # //ESP_LOGE("main","Modbus write unmodified = %d", unmodified);
      # // optionsmap should only return 2 values... 0 , 256 so bitmask with complement 0x0100 to ensure we keep the original values in register. Then appply OR with the value that was chosen
      # uint16_t modified = ((unmodified & ~0x0100) | value);
      # //ESP_LOGE("main","Modbus write to write = %d", modified);
      # return modified;    

text_sensor:
  - platform: modbus_controller            # 500 Overall State
    modbus_controller_id: ${inverter_name}_modbus_controller
    name: ${name}_${inverter_name}_overall_state
    id: ${inverter_name}_overall_state
    register_type: holding
    raw_encode: HEXBYTES
    address: 500
    lambda: |- 
      uint16_t value = modbus::helpers::word_from_hex_str(x, 0);
      switch (value) {
        case 0: return std::string("standby");
        case 1: return std::string("selftest");
        case 2: return std::string("normal");
        case 3: return std::string("alarm");
        case 4: return std::string("fault");
        default: return std::string("unknown");
      }      



















# modbus_controller:
#  - id: ${inverter_name}_modbus_controller
#    address: ${inverter_modbus_address}
#    modbus_id: ${inverter_modbus_id}
#    command_throttle: ${inverter_modbus_throttle}
#    setup_priority: -10
#    update_interval: ${inverter_update_interval}

# globals:  
#   - id: ${inverter_name}_pv_energy_total_yesterday_global
#     type: float
#     restore_value: yes    
#   - id: ${inverter_name}_ac_output_energy_yesterday_global
#     type: float
#     restore_value: yes
#   - id: ${inverter_name}_battery_charging_energy_yesterday_global
#     type: float
#     restore_value: yes
#   - id: ${inverter_name}_battery_discharging_energy_yesterday_global
#     type: float
#     restore_value: yes

# time:
#   - platform: homeassistant #sntp
#     id: !extend my_time
#     on_time:
#       - seconds: 59
#         minutes: 59
#         hours: 23
#         then:           
#           - globals.set:
#               id: ${inverter_name}_pv_energy_total_yesterday_global
#               value: !lambda return ( id(${inverter_name}_pv_energy_total_yesterday_global) =  float( id(${inverter_name}_pv_energy_total_today).state) );                    
#           - globals.set:
#               id: ${inverter_name}_ac_output_energy_yesterday_global
#               value: !lambda return ( id(${inverter_name}_ac_output_energy_yesterday_global) =  float( id(${inverter_name}_ac_output_energy_today).state) );
#           - globals.set:
#               id: ${inverter_name}_battery_charging_energy_yesterday_global
#               value: !lambda return ( id(${inverter_name}_battery_charging_energy_yesterday_global) =  float( id(${inverter_name}_battery_charging_energy_today).state) );                 
#           - globals.set:
#               id: ${inverter_name}_battery_discharging_energy_yesterday_global
#               value: !lambda return ( id(${inverter_name}_battery_discharging_energy_yesterday_global) =  float( id(${inverter_name}_battery_discharging_energy_today).state) ); 

# binary_sensor:   

#   # - platform: modbus_controller          # 28 
#     # modbus_controller_id: ${inverter_name}_modbus_controller
#     # name: ${name}_${inverter_name}_mppt_multipoint_scanning
#     # # id: ${inverter_name}_mppt_multipoint_scanning
#     # register_type: holding
#     # address: 28
#     # bitmask: 0x20       
    
#   - platform: modbus_controller          # 80 Switch on/off enable
#     modbus_controller_id: ${inverter_name}_modbus_controller
#     name: ${name}_${inverter_name}_switch_on_off
#     id: ${name}_${inverter_name}_switch_on_off
#     register_type: holding
#     # value_type: U_WORD
#     address: 80
#     # skip: 10
  
#   # - platform: modbus_controller          # 46 Istland Protection Mode 
#     # modbus_controller_id: ${inverter_name}_modbus_controller
#     # name: ${name}_${inverter_name}_island_protection_mode
#     # id: ${name}_${inverter_name}_island_protection_mode
#     # register_type: holding
#     # # value_type: U_WORD
#     # address: 46
#     # # skip: 10
    
#   - platform: modbus_controller          # 84 MPPT number 
#     modbus_controller_id: ${inverter_name}_modbus_controller
#     name: ${name}_${inverter_name}_mppt_number
#     id: ${name}_${inverter_name}_mppt_number
#     register_type: holding
#     # value_type: U_WORD
#     address: 84

#   - platform: modbus_controller          # 85 GFDI mode
#     modbus_controller_id: ${inverter_name}_modbus_controller
#     name: ${name}_${inverter_name}_GFDI_mode
#     id: ${name}_${inverter_name}_GFDI_mode
#     register_type: holding
#     # value_type: U_WORD
#     address: 85
#     # skip: 10
    
#   - platform: modbus_controller            # 194 Grid Connected Status
#     modbus_controller_id: ${inverter_name}_modbus_controller
#     name: ${name}_${inverter_name}_grid_connected_status
#     id: ${inverter_name}_grid_connected_status
#     register_type: holding
#     address: 194  

# sensor:

#   - platform: modbus_controller            # 01 Modbus address
#     modbus_controller_id: ${inverter_name}_modbus_controller
#     name: ${name}_${inverter_name}_modbus_address
#     id: ${inverter_name}_modbus_address
#     register_type: holding
#     value_type: U_WORD
#     address: 01
#     # filters:
#       # - offset: 1
    
#   # - platform: modbus_controller            # 55/01 Limiter
#     # modbus_controller_id: ${inverter_name}_modbus_controller
#     # name: ${name}_${inverter_name}_limiter
#     # id: ${inverter_name}_limiter
#     # register_type: holding
#     # value_type: U_WORD
#     # unit_of_measurement: 'W'
#     # accuracy_decimals: 2
#     # device_class: power
#     # address: 55 
  
#       #### battery statistics 
      
#   - platform: template
#     name: ${name}_${inverter_name}_battery_charging_current
#     id: ${inverter_name}_battery_charging_current
#     unit_of_measurement: 'A'
#     accuracy_decimals: 2
#     update_interval: ${inverter_template_update}
#     icon: mdi:current-dc  
#     lambda: |-
#       if (id(${inverter_name}_battery_current).state >= 0) {
#         return (id(${inverter_name}_battery_current).state );
#       }
#       else{
#        return 0.0;
#       }      
      
#   - platform: template
#     name: ${name}_${inverter_name}_battery_charging_power
#     id: ${inverter_name}_battery_charging_power
#     unit_of_measurement: 'W'
#     accuracy_decimals: 2
#     update_interval: ${inverter_template_update}
#     icon: mdi:power  
#     lambda: return ( (id(${inverter_name}_battery_voltage).state) * (id(${inverter_name}_battery_charging_current).state) );
   
#   - platform: modbus_controller            # 514 Battery Charge TpDay
#     modbus_controller_id: ${inverter_name}_modbus_controller
#     name: ${name}_${inverter_name}_battery_charging_energy_today
#     id: ${inverter_name}_battery_charging_energy_today
#     register_type: holding
#     address: 514
#     unit_of_measurement: 'kWh'
#     accuracy_decimals: 1
#     device_class: energy
#     state_class: total_increasing
#     value_type: U_WORD
#     filters:
#       - multiply: 0.1
      
#   - platform: template
#     name: ${name}_${inverter_name}_battery_charging_energy_yesterday
#     id: ${inverter_name}_battery_charging_energy_yesterday
#     unit_of_measurement: 'kWh'
#     accuracy_decimals: 1
#     icon: mdi:counter
#     update_interval: ${inverter_template_update}
#     lambda: |-
#       return ( id(${inverter_name}_battery_charging_energy_yesterday).state = id(${inverter_name}_battery_charging_energy_yesterday_global) );    

#   - platform: template
#     name: ${name}_${inverter_name}_battery_discharging_current
#     id: ${inverter_name}_battery_discharging_current
#     unit_of_measurement: 'A'
#     accuracy_decimals: 2
#     update_interval: ${inverter_template_update}
#     icon: mdi:current-dc  
#     lambda: |-
#       if (id(${inverter_name}_battery_current).state < 0) {
#         return ( - id(${inverter_name}_battery_current).state );
#       }
#       else{
#        return 0.0;
#       }

#   - platform: template
#     name: ${name}_${inverter_name}_battery_discharging_power
#     id: ${inverter_name}_battery_discharging_power
#     unit_of_measurement: 'W'
#     accuracy_decimals: 2
#     update_interval: ${inverter_template_update}
#     icon: mdi:power  
#     lambda: return ( (id(${inverter_name}_battery_voltage).state) * (id(${inverter_name}_battery_discharging_current).state) );

#   - platform: modbus_controller            # 515 Battery Discharge TpDay
#     modbus_controller_id: ${inverter_name}_modbus_controller
#     name: ${name}_${inverter_name}_battery_discharging_energy_today
#     id: ${inverter_name}_battery_discharging_energy_today
#     register_type: holding
#     address: 515
#     unit_of_measurement: 'kWh'
#     icon: mdi:counter
#     accuracy_decimals: 1
#     device_class: energy
#     state_class: total_increasing
#     value_type: U_WORD
#     filters:
#       - multiply: 0.1
      
#   - platform: template
#     name: ${name}_${inverter_name}_battery_discharging_energy_yesterday
#     id: ${inverter_name}_battery_discharging_energy_yesterday
#     unit_of_measurement: 'kWh'
#     accuracy_decimals: 1
#     icon: mdi:counter
#     update_interval: ${inverter_template_update}
#     lambda: |-
#       return ( id(${inverter_name}_battery_discharging_energy_yesterday).state = id(${inverter_name}_battery_discharging_energy_yesterday_global) );      

#   - platform: modbus_controller            # 516 Battery Charge Energy Total
#     modbus_controller_id: ${inverter_name}_modbus_controller
#     name: ${name}_${inverter_name}_battery_charging_total
#     id: ${inverter_name}_battery_charging_total
#     register_type: holding
#     address: 516
#     unit_of_measurement: 'kWh'
#     icon: mdi:counter
#     accuracy_decimals: 1
#     device_class: energy
#     state_class: total_increasing
#     value_type: U_DWORD_R
#     filters:
#      - multiply: 0.1

#   - platform: modbus_controller            # 518 Battery Discharge Energy Total
#     modbus_controller_id: ${inverter_name}_modbus_controller
#     name: ${name}_${inverter_name}_battery_discharging_total
#     id: ${inverter_name}_battery_discharging_total
#     register_type: holding
#     address: 518
#     unit_of_measurement: 'kWh'
#     accuracy_decimals: 1
#     device_class: energy
#     state_class: total_increasing
#     value_type: U_DWORD_R
#     filters:
#      - multiply: 0.1
     
#     ########### Battery  #############
    
#   - platform: modbus_controller            # 586 Battery Temperature
#     modbus_controller_id: ${inverter_name}_modbus_controller
#     name: ${name}_${inverter_name}_battery_temperature
#     id: ${inverter_name}_battery_temperature
#     register_type: holding
#     address: 586
#     unit_of_measurement: '°C'
#     icon: mdi:thermometer
#     accuracy_decimals: 1
#     device_class: temperature
#     state_class: measurement
#     value_type: U_WORD 
#     filters:
#       - offset: -1000
#       - multiply: 0.1

#   - platform: modbus_controller            # 587 Battery Voltage
#     modbus_controller_id: ${inverter_name}_modbus_controller
#     name: ${name}_${inverter_name}_battery_voltage
#     id: ${inverter_name}_battery_voltage
#     register_type: holding
#     address: 587
#     unit_of_measurement: 'V'
#     icon: mdi:sine-wave
#     accuracy_decimals: 1
#     device_class: voltage
#     state_class: measurement
#     filters:
#       - multiply: 0.01
#     value_type: U_WORD

#   - platform: modbus_controller            # 588 Battery SOC
#     modbus_controller_id: ${inverter_name}_modbus_controller
#     name: ${name}_${inverter_name}_battery_soc
#     id: ${inverter_name}_battery_soc
#     register_type: holding
#     address: 588
#     unit_of_measurement: '%'
#     icon: mdi:percent
#     accuracy_decimals: 0
#     device_class: battery
#     value_type: U_WORD
    
#   - platform: modbus_controller            # 590 Battery Output Power
#     modbus_controller_id: ${inverter_name}_modbus_controller
#     name: ${name}_${inverter_name}_battery_power
#     id: ${inverter_name}_battery_power
#     register_type: holding
#     address: 590
#     unit_of_measurement: 'W'
#     icon: mdi:power
#     accuracy_decimals: 2
#     device_class: power
#     value_type: S_WORD
#     filters:
#       - multiply: -1

#   - platform: modbus_controller            # 591 Battery Output Current
#     modbus_controller_id: ${inverter_name}_modbus_controller
#     name: ${name}_${inverter_name}_battery_current
#     id: ${inverter_name}_battery_current
#     register_type: holding
#     address: 591
#     unit_of_measurement: 'A'
#     accuracy_decimals: 2
#     icon: mdi:current-dc
#     device_class: current
#     state_class: measurement
#     value_type: S_WORD
#     filters:
#       - multiply: -0.01
 
#   - platform: modbus_controller           # 99 Battery Equalization Voltage
#     modbus_controller_id: ${inverter_name}_modbus_controller
#     # icon: mdi:battery
#     name: ${name}_${inverter_name}_battery_equalization_voltage
#     id: ${inverter_name}_battery_equalization_voltage
#     address: 99
#     unit_of_measurement: 'V'
#     icon: mdi:sine-wave
#     register_type: holding
#     value_type: U_WORD
#     accuracy_decimals: 1
#     device_class: voltage
#     state_class: measurement
#     filters:
#       - multiply: 0.01
 
#   - platform: modbus_controller         # 108 Battery Max Charge current
#     modbus_controller_id: ${inverter_name}_modbus_controller
#     name: ${name}_${inverter_name}_battery_max_charge_current
#     register_type: holding
#     unit_of_measurement: 'A'
#     icon: mdi:current-dc
#     accuracy_decimals: 0
#     device_class: current
#     address: 108
#     value_type: U_WORD
    
#   - platform: modbus_controller         # 109 Battery Max Discharge current
#     modbus_controller_id: ${inverter_name}_modbus_controller
#     name: ${name}_${inverter_name}_battery_max_discharge_current
#     register_type: holding
#     unit_of_measurement: 'A'
#     icon: mdi:current-dc
#     accuracy_decimals: 0
#     device_class: current
#     address: 109
#     value_type: U_WORD

#   - platform: modbus_controller         # 126 Grid Charge Starting Voltage
#     modbus_controller_id: ${inverter_name}_modbus_controller
#     name: ${name}_${inverter_name}_grid_charge_starting_voltage
#     register_type: holding
#     address: 126
#     unit_of_measurement: 'V'
#     icon: mdi:sine-wave
#     value_type: U_WORD
#     accuracy_decimals: 1
#     device_class: voltage
#     state_class: measurement
#     filters:
#       - multiply: 0.01     
    
#   - platform: modbus_controller         # 128 Grid Charge Battery current
#     modbus_controller_id: ${inverter_name}_modbus_controller
#     name: ${name}_${inverter_name}_grid_charge_battery_current
#     register_type: holding
#     unit_of_measurement: 'A'
#     icon: mdi:current-dc
#     accuracy_decimals: 0
#     device_class: current
#     address: 128
#     value_type: U_WORD
       
      
 
#   - platform: modbus_controller          # 100 Battery Absorption Voltage
#     modbus_controller_id: ${inverter_name}_modbus_controller
#     name: ${name}_${inverter_name}_battery_absorption_voltage
#     id: ${inverter_name}_battery_absorption_voltage
#     address: 100
#     unit_of_measurement: 'V'
#     icon: mdi:sine-wave
#     register_type: holding
#     value_type: U_WORD
#     accuracy_decimals: 1
#     device_class: voltage
#     state_class: measurement
#     filters:
#       - multiply: 0.01

#   - platform: modbus_controller            # 101 Battery Float Voltage
#     modbus_controller_id: ${inverter_name}_modbus_controller
#     name: ${name}_${inverter_name}_battery_float_voltage
#     id: ${inverter_name}_battery_float_voltage
#     address: 101
#     unit_of_measurement: 'V'
#     icon: mdi:sine-wave
#     register_type: holding
#     value_type: U_WORD
#     accuracy_decimals: 1
#     device_class: voltage
#     state_class: measurement
#     filters:
#       - multiply: 0.01
      
#   - platform: modbus_controller            # 115 Battery Capacity Shutdown
#     modbus_controller_id: ${inverter_name}_modbus_controller
#     name: ${name}_${inverter_name}_battery_capacity_shutdown
#     id: ${inverter_name}_battery_capacity_shutdown
#     register_type: holding
#     address: 115
#     unit_of_measurement: '%'
#     icon: mdi:percent
#     accuracy_decimals: 0
#     device_class: battery

#   - platform: modbus_controller           # 118 Battery Shuntdown Voltage
#     modbus_controller_id: ${inverter_name}_modbus_controller
#     name: ${name}_${inverter_name}_battery_shutdown_voltage
#     id: ${inverter_name}_battery_shutdown_voltage
#     address: 118
#     unit_of_measurement: 'V'
#     icon: mdi:sine-wave
#     register_type: holding
#     value_type: U_WORD
#     accuracy_decimals: 1
#     device_class: voltage
#     state_class: measurement
#     filters:
#       - multiply: 0.01

#   - platform: modbus_controller          # 120 Battery Low Voltage
#     modbus_controller_id: ${inverter_name}_modbus_controller
#     name: ${name}_${inverter_name}_battery_low_voltage
#     id: ${inverter_name}_battery_low_voltage
#     address: 120
#     unit_of_measurement: 'V'
#     icon: mdi:sine-wave
#     register_type: holding
#     value_type: U_WORD
#     accuracy_decimals: 1
#     device_class: voltage
#     state_class: measurement
#     filters:
#       - multiply: 0.01    
     
#      ##### Grid data & statistics ####
     
#   - platform: modbus_controller            # 520 Grid Import Today (Buy)
#     modbus_controller_id: ${inverter_name}_modbus_controller
#     name: ${name}_${inverter_name}_grid_energy_imported_today
#     id: ${inverter_name}_grid_energy_imported_today
#     register_type: holding
#     address: 520
#     unit_of_measurement: 'kWh'
#     icon: mdi:counter
#     accuracy_decimals: 1
#     device_class: energy
#     state_class: total_increasing
#     value_type: U_WORD
#     filters:
#       - multiply: 0.1
      
#   - platform: modbus_controller            # 521 Grid Export Today (Sell)
#     modbus_controller_id: ${inverter_name}_modbus_controller
#     name: ${name}_${inverter_name}_grid_energy_exported_today
#     id: ${inverter_name}_grid_energy_exported_today
#     register_type: holding
#     address: 521
#     unit_of_measurement: 'kWh'
#     icon: mdi:counter
#     accuracy_decimals: 1
#     device_class: energy
#     state_class: total_increasing
#     value_type: U_WORD
#     filters:
#       - multiply: 0.1    
     
#   - platform: modbus_controller            # 522 Grid Import Energy Total (Buy)
#     modbus_controller_id: ${inverter_name}_modbus_controller
#     name: ${name}_${inverter_name}_grid_energy_imported_total
#     id: ${inverter_name}_grid_energy_imported_total
#     register_type: holding
#     address: 522
#     unit_of_measurement: 'kWh'
#     accuracy_decimals: 1
#     icon: mdi:counter
#     device_class: energy
#     state_class: total_increasing
#     value_type: U_DWORD_R
#     filters:
#       - multiply: 0.1  
    
#   - platform: modbus_controller            # 524 Grid Export Energy Total (Sell)
#     modbus_controller_id: ${inverter_name}_modbus_controller
#     name: ${name}_${inverter_name}_grid_energy_exported_total
#     id: ${inverter_name}_grid_energy_exported_total
#     register_type: holding
#     address: 524
#     unit_of_measurement: 'kWh'
#     accuracy_decimals: 1
#     icon: mdi:counter
#     device_class: energy
#     state_class: total_increasing
#     value_type: U_DWORD_R
#     filters:
#       - multiply: 0.1

#   - platform: modbus_controller            # 609 Grid Frequency
#     modbus_controller_id: ${inverter_name}_modbus_controller
#     name: ${name}_${inverter_name}_grid_frequency
#     id: ${inverter_name}_grid_frequency
#     register_type: holding
#     address: 609
#     unit_of_measurement: 'Hz'
#     icon: mdi:sine-wave
#     accuracy_decimals: 2
#     filters:
#       - multiply: 0.01
#     value_type: U_WORD
#     state_class: measurement
    
#   - platform: modbus_controller            # 598 Grid phase A Voltage
#     modbus_controller_id: ${inverter_name}_modbus_controller
#     name: ${name}_${inverter_name}_grid_phaseA_voltage
#     id: ${inverter_name}_grid_phaseA_voltage
#     register_type: holding
#     address: 598
#     unit_of_measurement: 'V'
#     icon: mdi:sine-wave
#     accuracy_decimals: 1
#     device_class: voltage
#     state_class: measurement
#     filters:
#       - multiply: 0.1
#     value_type: U_WORD

#   - platform: modbus_controller            # 599 Grid phase B Voltage
#     modbus_controller_id: ${inverter_name}_modbus_controller
#     name: ${name}_${inverter_name}_grid_phaseB_voltage
#     id: ${inverter_name}_grid_phaseB_voltage
#     register_type: holding
#     address: 599
#     unit_of_measurement: 'V'
#     icon: mdi:sine-wave
#     accuracy_decimals: 1
#     device_class: voltage
#     state_class: measurement
#     filters:
#       - multiply: 0.1
#     value_type: U_WORD
    
#   - platform: modbus_controller            # 600 Grid phase C Voltage
#     modbus_controller_id: ${inverter_name}_modbus_controller
#     name: ${name}_${inverter_name}_grid_phaseC_voltage
#     id: ${inverter_name}_grid_phaseC_voltage
#     register_type: holding
#     address: 600
#     unit_of_measurement: 'V'
#     icon: mdi:sine-wave
#     accuracy_decimals: 1
#     device_class: voltage
#     state_class: measurement
#     filters:
#       - multiply: 0.1
#     value_type: U_WORD  
    
   

#   - platform: modbus_controller             # 604 Grid PhaseA Power
#     modbus_controller_id: ${inverter_name}_modbus_controller
#     name: ${name}_${inverter_name}_grid_phaseA_power
#     id: ${inverter_name}_grid_phaseA_power
#     register_type: holding
#     address: 604
#     unit_of_measurement: 'W'
#     icon: mdi:power
#     accuracy_decimals: 2
#     device_class: power
#     state_class: measurement
#     value_type: S_WORD
    
#   - platform: modbus_controller             # 605 Grid PhaseB Power
#     modbus_controller_id: ${inverter_name}_modbus_controller
#     name: ${name}_${inverter_name}_grid_phaseB_power
#     id: ${inverter_name}_grid_phaseB_power
#     register_type: holding
#     address: 605
#     unit_of_measurement: 'W'
#     icon: mdi:power
#     accuracy_decimals: 2
#     device_class: power
#     state_class: measurement
#     value_type: S_WORD

#   - platform: modbus_controller             # 606 Grid PhaseC Power
#     modbus_controller_id: ${inverter_name}_modbus_controller
#     name: ${name}_${inverter_name}_grid_phaseC_power
#     id: ${inverter_name}_grid_phaseC_power
#     register_type: holding
#     address: 606
#     unit_of_measurement: 'W'
#     icon: mdi:power
#     accuracy_decimals: 2
#     device_class: power
#     state_class: measurement
#     value_type: S_WORD
    
#   - platform: modbus_controller             # 607 Grid Power
#     modbus_controller_id: ${inverter_name}_modbus_controller
#     name: ${name}_${inverter_name}_grid_power
#     id: ${inverter_name}_grid_power
#     register_type: holding
#     address: 607
#     unit_of_measurement: 'W'
#     icon: mdi:power
#     accuracy_decimals: 2
#     device_class: power
#     state_class: measurement
#     value_type: S_WORD    
    
#   - platform: modbus_controller            # 172 Grid External Power
#     modbus_controller_id: ${inverter_name}_modbus_controller
#     name: ${name}_${inverter_name}_grid_external_power
#     id: ${inverter_name}_grid_external_power
#     register_type: holding
#     address: 172
#     unit_of_measurement: 'W'
#     icon: mdi:power
#     accuracy_decimals: 2
#     device_class: power
#     state_class: measurement
#     value_type: S_WORD
          
#   - platform: modbus_controller        # 255 Grid Peak Shaving raw register value
#     modbus_controller_id: ${inverter_name}_modbus_controller
#     id: ${inverter_name}_grid_peak_shaving_raw
#     register_type: holding
#     address: 280
#     value_type: U_WORD
    
#   - platform: modbus_controller            # 293 Grid Peak Shaving Power
#     modbus_controller_id: ${inverter_name}_modbus_controller
#     name: ${name}_${inverter_name}_grid_peak_shaving_power
#     id: ${inverter_name}_grid_peak_shaving_power
#     address: 293
#     register_type: holding
#     value_type: U_WORD
#     unit_of_measurement: 'W'
#     accuracy_decimals: 2
#     device_class: power
#     state_class: measurement
#     icon: mdi:power   
    
#   # - platform: modbus_controller            # 520 Grid Import Energy Today (Buy)
#     # modbus_controller_id: ${inverter_name}_modbus_controller
#     # name: ${name}_${inverter_name}_grid_energy_imported_today
#     # id: ${inverter_name}_grid_energy_imported_today
#     # register_type: holding
#     # address: 520
#     # unit_of_measurement: 'kWh'
#     # accuracy_decimals: 1
#     # icon: mdi:counter
#     # device_class: energy
#     # state_class: total_increasing
#     # value_type: U_WORD
#     # filters:
#       # - multiply: 0.1  
    
#   # - platform: modbus_controller            # 521 Grid Export Energy Today (Sell)
#     # modbus_controller_id: ${inverter_name}_modbus_controller
#     # name: ${name}_${inverter_name}_grid_energy_exported_today
#     # id: ${inverter_name}_grid_energy_exported_total
#     # register_type: holding
#     # address: 521
#     # unit_of_measurement: 'kWh'
#     # accuracy_decimals: 1
#     # icon: mdi:counter
#     # device_class: energy
#     # state_class: total_increasing
#     # value_type: U_WORD
#     # filters:
#       # - multiply: 0.1  
      
 
      
#     ####### House load data & statistics  #####  

#   - platform: modbus_controller            # 526 Daily Load
#     modbus_controller_id: ${inverter_name}_modbus_controller
#     name: ${name}_${inverter_name}_load_energy_today
#     id: ${inverter_name}_load_energy_today
#     register_type: holding
#     address: 526
#     unit_of_measurement: 'kWh'
#     icon: mdi:counter
#     accuracy_decimals: 1
#     device_class: energy
#     state_class: total_increasing
#     filters:
#       - multiply: 0.1
#     value_type: U_WORD
    
#   - platform: modbus_controller            # 527 Total Load
#     modbus_controller_id: ${inverter_name}_modbus_controller
#     name: ${name}_${inverter_name}_load_energy_total
#     id: ${inverter_name}_load_energy_total
#     register_type: holding
#     address: 527
#     unit_of_measurement: 'kWh'
#     icon: mdi:counter
#     accuracy_decimals: 1
#     device_class: energy
#     state_class: total_increasing
#     filters:
#       - multiply: 0.1
#     value_type: U_DWORD_R  
    
#   - platform: modbus_controller            # 644 Load PhaseA voltage
#     modbus_controller_id: ${inverter_name}_modbus_controller
#     name: ${name}_${inverter_name}_load_phaseA_voltage
#     id: ${inverter_name}_load_phaseA_voltage
#     register_type: holding
#     address: 644
#     unit_of_measurement: 'V'
#     icon: mdi:sine-wave
#     accuracy_decimals: 1
#     device_class: voltage
#     state_class: measurement
#     filters:
#       - multiply: 0.1
#     value_type: U_WORD

#   - platform: modbus_controller            # 644 Load PhaseB voltage
#     modbus_controller_id: ${inverter_name}_modbus_controller
#     name: ${name}_${inverter_name}_load_phaseB_voltage
#     id: ${inverter_name}_load_phaseB_voltage
#     register_type: holding
#     address: 645
#     unit_of_measurement: 'V'
#     icon: mdi:sine-wave
#     accuracy_decimals: 1
#     device_class: voltage
#     state_class: measurement
#     filters:
#       - multiply: 0.1
#     value_type: U_WORD

#   - platform: modbus_controller            # 646 Load PhaseB voltage
#     modbus_controller_id: ${inverter_name}_modbus_controller
#     name: ${name}_${inverter_name}_load_phaseC_voltage
#     id: ${inverter_name}_load_phaseC_voltage
#     register_type: holding
#     address: 646
#     unit_of_measurement: 'V'
#     icon: mdi:sine-wave
#     accuracy_decimals: 1
#     device_class: voltage
#     state_class: measurement
#     filters:
#       - multiply: 0.1
#     value_type: U_WORD    

#   # - platform: modbus_controller            # 085 Total Load Power
#     # modbus_controller_id: ${inverter_name}_modbus_controller
#     # name: ${name}_${inverter_name}_total_load_power
#     # id: ${inverter_name}_total_load_power
#     # register_type: holding
#     # address: 85
#     # unit_of_measurement: 'W'
#     # icon: mdi:power
#     # accuracy_decimals: 2
#     # device_class: energy
#     # state_class: total_increasing
#     # value_type: U_DWORD_R
#     # filters:
#       # - multiply: 0.1
      
#     ###### inverter builtin temperature data ####
    
#   - platform: modbus_controller            # 540 DC Transformer Temperature
#     modbus_controller_id: ${inverter_name}_modbus_controller
#     name: ${name}_${inverter_name}_dc_transformer_temperature
#     id: ${inverter_name}_dc_transformer_temperature
#     register_type: holding
#     address: 540
#     unit_of_measurement: '°C'
#     icon: mdi:thermometer
#     accuracy_decimals: 1
#     device_class: temperature
#     state_class: measurement
#     value_type: S_WORD
#     filters:
#       - offset: -1000
#       - multiply:  0.1

#   - platform: modbus_controller            # 541 Radiator Temperature
#     modbus_controller_id: ${inverter_name}_modbus_controller
#     name: ${name}_${inverter_name}_dc_radiator_temperature
#     id: ${inverter_name}_dc_radiator_temperature
#     register_type: holding
#     address: 541
#     unit_of_measurement: '°C'
#     icon: mdi:thermometer
#     accuracy_decimals: 1
#     device_class: temperature
#     state_class: measurement
#     value_type: S_WORD
#     filters:
#       - offset: -1000
#       - multiply:  0.1
    
#       ######## PV statistics   ##########
      
#   - platform: modbus_controller            # 529 Day PV Energy
#     modbus_controller_id: ${inverter_name}_modbus_controller
#     name: ${name}_${inverter_name}_pv_energy_today
#     id: ${inverter_name}_pv_energy_today
#     register_type: holding
#     address: 529
#     unit_of_measurement: 'kWh'
#     icon: mdi:counter
#     accuracy_decimals: 1
#     device_class: energy
#     state_class: total_increasing
#     filters:
#       - multiply: 0.1
#     value_type: U_WORD

      
#   - platform: modbus_controller            # 534 PV Energy Total Power
#     modbus_controller_id: ${inverter_name}_modbus_controller
#     name: ${name}_${inverter_name}_pv_energy_total
#     id: ${inverter_name}_pv_energy_total
#     register_type: holding
#     address: 534
#     unit_of_measurement: 'kWh'
#     accuracy_decimals: 1
#     icon: mdi:counter
#     device_class: energy
#     state_class: total_increasing
#     filters:
#       - multiply: 0.1
#     value_type: U_DWORD_R  

        
#     ######## PV data ######
    
#   - platform: modbus_controller            # 672 PV1 Power
#     modbus_controller_id: ${inverter_name}_modbus_controller
#     name: ${name}_${inverter_name}_pv1_power
#     id: ${inverter_name}_pv1_power
#     register_type: holding
#     address: 672
#     unit_of_measurement: 'W'
#     icon: mdi:power
#     accuracy_decimals: 2
#     device_class: power
#     state_class: measurement
#     value_type: U_WORD
    
#   - platform: modbus_controller            # 673 PV2 Power
#     modbus_controller_id: ${inverter_name}_modbus_controller
#     name: ${name}_${inverter_name}_pv2_power
#     id: ${inverter_name}_pv2_power
#     register_type: holding
#     address: 673
#     unit_of_measurement: 'W'
#     icon: mdi:power
#     accuracy_decimals: 2
#     device_class: power
#     state_class: measurement
#     value_type: U_WORD

#   - platform: template                   # Sum of PV1 and PV2 to get total PV Power
#     name: ${name}_${inverter_name}_pv_power_total
#     id: ${inverter_name}_pv_power_total
#     unit_of_measurement: 'W'
#     icon: mdi:power
#     accuracy_decimals: 2
#     device_class: power
#     state_class: measurement
#     lambda: |-
#       return (id(${inverter_name}_pv1_power).state + id(${inverter_name}_pv2_power).state);
#     update_interval: ${inverter_template_update}
    
    
#   - platform: modbus_controller            # 676 PV1 Voltage
#     modbus_controller_id: ${inverter_name}_modbus_controller
#     name: ${name}_${inverter_name}_pv1_voltage
#     id: ${inverter_name}_pv1_voltage
#     register_type: holding
#     address: 676
#     unit_of_measurement: 'V'
#     icon: mdi:sine-wave
#     accuracy_decimals: 1
#     device_class: voltage
#     state_class: measurement
#     filters:
#       - multiply: 0.1
#     value_type: U_WORD
    
#   - platform: modbus_controller            # 677 PV1 Output Current
#     modbus_controller_id: ${inverter_name}_modbus_controller
#     name: ${name}_${inverter_name}_pv1_current
#     id: ${inverter_name}_pv1_current
#     register_type: holding
#     address: 677
#     unit_of_measurement: 'A'
#     accuracy_decimals: 2
#     icon: mdi:current-dc
#     device_class: current
#     state_class: measurement
#     filters:
#       - multiply: 0.1
#     value_type: U_WORD
    

#   - platform: modbus_controller            # 678 PV2 Voltage
#     modbus_controller_id: ${inverter_name}_modbus_controller
#     name: ${name}_${inverter_name}_pv2_voltage
#     id: ${inverter_name}_pv2_voltage
#     register_type: holding
#     address: 678
#     unit_of_measurement: 'V'
#     icon: mdi:sine-wave
#     filters:
#       - multiply: 0.1
#     accuracy_decimals: 1
#     device_class: voltage
#     state_class: measurement
#     value_type: U_WORD


#   - platform: modbus_controller            # 679 PV2 Output Current
#     modbus_controller_id: ${inverter_name}_modbus_controller
#     name: ${name}_${inverter_name}_pv2_current
#     id: ${inverter_name}_pv2_current
#     register_type: holding
#     address: 679
#     unit_of_measurement: 'A'
#     icon: mdi:current-dc
#     accuracy_decimals: 2
#     device_class: current
#     state_class: measurement
#     filters:
#       - multiply: 0.1
#     value_type: U_WORD
    
   
#   - platform: total_daily_energy
#     name: ${name}_${inverter_name}_pv_energy_total_today
#     id: ${inverter_name}_pv_energy_total_today
#     power_id: ${inverter_name}_pv_power_total
#     unit_of_measurement: 'kWh'
#     icon: mdi:counter
#     accuracy_decimals: 1
#     method: trapezoid
#     filters:
#        # Multiplication factor from W to kW is 0.001
#        - multiply: 0.001
    
#   - platform: template
#     name: ${name}_${inverter_name}_pv_energy_total_yesterday
#     id: ${inverter_name}_pv_energy_total_yesterday
#     unit_of_measurement: 'kWh'
#     icon: mdi:counter
#     accuracy_decimals: 1
#     update_interval: ${inverter_template_update}
#     lambda: |-
#       return ( id(${inverter_name}_pv_energy_total_yesterday).state = id(${inverter_name}_pv_energy_total_yesterday_global) );  
   
#   - platform: total_daily_energy
#     name: ${name}_${inverter_name}_ac_output_energy_today
#     id: ${inverter_name}_ac_output_energy_today
#     power_id: ${inverter_name}_ac_output_power
#     unit_of_measurement: 'kWh'
#     icon: mdi:counter
#     accuracy_decimals: 1   
#     method: trapezoid
#     filters:
#        # Multiplication factor from W to kW is 0.001
#        - multiply: 0.001

    
#   - platform: template
#     name: ${name}_${inverter_name}_ac_output_energy_yesterday
#     id: ${inverter_name}_ac_output_energy_yesterday
#     unit_of_measurement: 'kWh'
#     accuracy_decimals: 1
#     icon: mdi:counter
#     update_interval: ${inverter_template_update}
#     lambda: |-
#       return ( id(${inverter_name}_ac_output_energy_yesterday).state = id(${inverter_name}_ac_output_energy_yesterday_global) );  
    
#    ############### ACout & aux data & statistics  #####
 
#   - platform: modbus_controller            # 630 Inverter Output PhaseA Current
#     modbus_controller_id: ${inverter_name}_modbus_controller
#     name: ${name}_${inverter_name}_ac_output_phaseA_current
#     id: ${inverter_name}_ac_output_phaseA_current
#     register_type: holding
#     address: 630
#     unit_of_measurement: 'A'
#     icon: mdi:current-dc
#     accuracy_decimals: 2
#     device_class: current
#     state_class: measurement
#     value_type: S_WORD
#     filters:
#       - multiply: 0.01
      
#   - platform: modbus_controller            # 631 Inverter Output PhaseB Current
#     modbus_controller_id: ${inverter_name}_modbus_controller
#     name: ${name}_${inverter_name}_ac_output_phaseB_current
#     id: ${inverter_name}_ac_output_phaseB_current
#     register_type: holding
#     address: 631
#     unit_of_measurement: 'A'
#     icon: mdi:current-dc
#     accuracy_decimals: 2
#     device_class: current
#     state_class: measurement
#     value_type: S_WORD
#     filters:
#       - multiply: 0.01

#   - platform: modbus_controller            # 632 Inverter Output PhaseC Current
#     modbus_controller_id: ${inverter_name}_modbus_controller
#     name: ${name}_${inverter_name}_ac_output_phaseC_current
#     id: ${inverter_name}_ac_output_phaseC_current
#     register_type: holding
#     address: 632
#     unit_of_measurement: 'A'
#     icon: mdi:current-dc
#     accuracy_decimals: 2
#     device_class: current
#     state_class: measurement
#     value_type: S_WORD
#     filters:
#       - multiply: 0.01      
      
#   # - platform: modbus_controller            # 166 Aux Output Power
#     # modbus_controller_id: ${inverter_name}_modbus_controller
#     # name: ${name}_${inverter_name}_aux_output_power
#     # id: ${inverter_name}_aux_output_power
#     # register_type: holding
#     # address: 166
#     # unit_of_measurement: 'W'
#     # icon: mdi:power
#     # accuracy_decimals: 2
#     # device_class: power
#     # state_class: measurement
#     # value_type: S_WORD
   
#   - platform: modbus_controller            # 636 Inverter Output Power
#     modbus_controller_id: ${inverter_name}_modbus_controller
#     name: ${name}_${inverter_name}_ac_output_power
#     id: ${inverter_name}_ac_output_power
#     register_type: holding
#     address: 636
#     unit_of_measurement: 'W'
#     icon: mdi:power
#     accuracy_decimals: 2
#     device_class: power
#     value_type: S_WORD

#   - platform: modbus_controller            # 653 Load Power
#     modbus_controller_id: ${inverter_name}_modbus_controller
#     name: ${name}_${inverter_name}_load_power
#     id: ${inverter_name}_load_power
#     register_type: holding
#     address: 653
#     unit_of_measurement: 'W'
#     icon: mdi:power
#     accuracy_decimals: 2
#     device_class: power
#     state_class: measurement
#     value_type: S_WORD
    
#   - platform: modbus_controller            # 655 Load Frequency
#     modbus_controller_id: ${inverter_name}_modbus_controller
#     name: ${name}_${inverter_name}_load_frequency
#     id: ${inverter_name}_load_frequency
#     register_type: holding
#     address: 655
#     unit_of_measurement: 'Hz'
#     icon: mdi:sine-wave
#     accuracy_decimals: 2
#     filters:
#       - multiply: 0.01
#     value_type: U_WORD
#     state_class: measurement
    
#   - platform: modbus_controller            # 638 AC output Frequency
#     modbus_controller_id: ${inverter_name}_modbus_controller
#     name: ${name}_${inverter_name}_ac_output_frequency
#     id: ${inverter_name}_ac_output_frequency
#     register_type: holding
#     address: 638
#     unit_of_measurement: 'Hz'
#     icon: mdi:alpha-Hz-circle-outline
#     accuracy_decimals: 2
#     filters:
#       - multiply: 0.01
#     value_type: U_WORD
#     state_class: measurement

#   # - platform: modbus_controller            # 194 Grid connexion
#     # modbus_controller_id: ${inverter_name}_modbus_controller
#     # name: ${name}_${inverter_name}_grid_connexion
#     # id: ${inverter_name}_grid_connexion
#     # register_type: holding
#     # address: 194
#     # accuracy_decimals: 0
#     # value_type: U_WORD
#     # state_class: measurement    
    
#   # - platform: template                   # Essential Power based on register 175 + 167 -166
#     # name: ${name}_${inverter_name}_essential_power
#     # unit_of_measurement: 'W'
#     # accuracy_decimals: 2
#     # device_class: power
#     # icon: mdi:power
#     # state_class: measurement
#     # lambda: |-
#       # return (id(${inverter_name}_ac_output_power).state + id(${inverter_name}_grid_power_167).state - id(${inverter_name}_aux_output_power).state);
#     # update_interval: ${inverter_template_update}

#   # - platform: template                   # Essential Power based on register 175 + 169 -166
#     # name: ${name}_${inverter_name}_essential_power_1
#     # unit_of_measurement: 'W'
#     # accuracy_decimals: 2
#     # icon: mdi:power
#     # device_class: power
#     # state_class: measurement
#     # lambda: |-
#       # return (id(${inverter_name}_ac_output_power).state + id(${inverter_name}_grid_power).state - id(${inverter_name}_aux_output_power).state);
#     # update_interval: ${inverter_template_update}

#   # - platform: template                   # Nonessential Power 175 - 167
#     # name: ${name}_${inverter_name}_nonessential_power
#     # unit_of_measurement: 'W'
#     # icon: mdi:power
#     # accuracy_decimals: 2
#     # device_class: power
#     # state_class: measurement
#     # lambda: |-
#       # return (id(${inverter_name}_grid_external_power).state - id(${inverter_name}_grid_power_167).state);
#     # update_interval: ${inverter_template_update}

#   # - platform: template                   # Nonessential Power 175 - 169
#     # name: ${name}_${inverter_name}_nonessential_power_1
#     # unit_of_measurement: 'W'
#     # icon: mdi:power
#     # accuracy_decimals: 2
#     # device_class: power
#     # state_class: measurement
#     # lambda: |-
#       # return (id(${inverter_name}_grid_external_power).state - id(${inverter_name}_grid_power).state);
#     # update_interval: ${inverter_template_update}
    
# switch:

#   # - platform: modbus_controller          # 28 
#     # use_write_multiple: true
#     # modbus_controller_id: ${inverter_name}_modbus_controller
#     # name: ${name}_${inverter_name}_low_power_mode
#     # id: ${inverter_name}_low_power_mode
#     # register_type: holding
#     # address: 28
#     # bitmask: 0x04
#     # icon: mdi:toggle-switch
    
#   # - platform: modbus_controller          # 28 
#     # use_write_multiple: true
#     # modbus_controller_id: ${inverter_name}_modbus_controller
#     # name: ${name}_${inverter_name}_mppt_multipoint_scanning
#     # id: ${inverter_name}_mppt_multipoint_scanning
#     # register_type: holding
#     # address: 28
#     # bitmask: 0X20
#     # icon: mdi:toggle-switch
    
#   # - platform: modbus_controller          #34 
#     # use_write_multiple: true
#     # modbus_controller_id: ${inverter_name}_modbus_controller
#     # name: ${name}_${inverter_name}_low_noise_mode
#     # id: ${inverter_name}_low_noise_mode
#     # register_type: holding
#     # address: 34
#     # bitmask: 0x01
#     # icon: mdi:toggle-switch  
  

#   - platform: modbus_controller          # 145 Toggle Solar Sell
#     use_write_multiple: true
#     modbus_controller_id: ${inverter_name}_modbus_controller
#     name: ${name}_${inverter_name}_toggle_solar_sell
#     id: ${inverter_name}_toggle_solar_sell
#     register_type: holding
#     address: 145
#     bitmask: 0x01
#     entity_category: config
#     icon: mdi:toggle-switch
    
#   - platform: modbus_controller          # 132 Toggle Force Generator
#     use_write_multiple: true
#     modbus_controller_id: ${inverter_name}_modbus_controller
#     name: ${name}_${inverter_name}_toggle_force_generator
#     id: ${inverter_name}_toggle_force_generator
#     register_type: holding
#     address: 132
#     bitmask: 0x01
#     icon: mdi:toggle-switch 

# number:

#   - platform: template         # 99 Battery Equalization Voltage
#     name: ${name}_${inverter_name}_battery_equalization_voltage
#     id: ${inverter_name}_battery_equalization_voltage_number
#     unit_of_measurement: 'V'
#     optimistic: true
#     icon: mdi:sine-wave
#     min_value: 50.00
#     max_value: 61.00
#     step: 0.1
#     initial_value: 55.90
#     restore_value: true
#     mode: 'slider'
#     on_value:
#       then: 
#         - lambda: |-
#             esphome::modbus_controller::ModbusController *controller = id(${inverter_name}_modbus_controller);
#             std::vector<uint16_t> battery_settings(1);
#             battery_settings[0]  = uint16_t(  (id(${inverter_name}_battery_equalization_voltage_number).state)*100 );
                    
#             esphome::modbus_controller::ModbusCommandItem battery_command = esphome::modbus_controller::ModbusCommandItem::create_write_multiple_command(controller, 99, battery_settings.size() ,
#                                                                                           battery_settings);
#             delay(200);
#             controller->queue_command(battery_command);
#             delay(200);

#   - platform: template         # 100 Battery Absorption Voltage
#     name: ${name}_${inverter_name}_battery_absorption_voltage
#     id: ${inverter_name}_battery_absorption_voltage_number
#     unit_of_measurement: 'V'
#     optimistic: true
#     icon: mdi:sine-wave
#     min_value: 50.00
#     max_value: 61.00
#     step: 0.1
#     initial_value: 55.90
#     restore_value: true
#     mode: 'slider'
#     on_value:
#       then: 
#         - lambda: |-
#             esphome::modbus_controller::ModbusController *controller = id(${inverter_name}_modbus_controller);
#             std::vector<uint16_t> battery_settings(1);
#             battery_settings[0]  = uint16_t(  (id(${inverter_name}_battery_absorption_voltage_number).state)*100 );
                    
#             esphome::modbus_controller::ModbusCommandItem battery_command = esphome::modbus_controller::ModbusCommandItem::create_write_multiple_command(controller, 100, battery_settings.size() ,
#                                                                                           battery_settings);
#             delay(200);
#             controller->queue_command(battery_command);
#             delay(200);
  
#   - platform: template         # 101 Battery Float Voltage
#     name: ${name}_${inverter_name}_battery_float_voltage
#     id: ${inverter_name}_battery_float_voltage_number
#     unit_of_measurement: 'V'
#     optimistic: true
#     icon: mdi:sine-wave
#     min_value: 50.00
#     max_value: 61.00
#     step: 0.1
#     initial_value: 55.90
#     restore_value: true
#     mode: 'slider'
#     on_value:
#       then: 
#         - lambda: |-
#             esphome::modbus_controller::ModbusController *controller = id(${inverter_name}_modbus_controller);
#             std::vector<uint16_t> battery_settings(1);
#             battery_settings[0]  = uint16_t(  (id(${inverter_name}_battery_float_voltage_number).state)*100 );
                    
#             esphome::modbus_controller::ModbusCommandItem battery_command = esphome::modbus_controller::ModbusCommandItem::create_write_multiple_command(controller, 101, battery_settings.size() ,
#                                                                                           battery_settings);
#             delay(200);
#             controller->queue_command(battery_command);
#             delay(200);
            
            
#   - platform: template         # 118 Battery Shuntdown Voltage
#     name: ${name}_${inverter_name}_battery_shuntdown_voltage
#     id: ${inverter_name}_battery_shuntdown_voltage_number
#     unit_of_measurement: 'V'
#     optimistic: true
#     icon: mdi:sine-wave
#     min_value: 40.00
#     max_value: 52.00
#     step: 0.1
#     initial_value: 47.00
#     restore_value: true
#     mode: 'slider'
#     on_value:
#       then: 
#         - lambda: |-
#             esphome::modbus_controller::ModbusController *controller = id(${inverter_name}_modbus_controller);
#             std::vector<uint16_t> battery_settings(1);
#             battery_settings[0]  = uint16_t(  (id(${inverter_name}_battery_shuntdown_voltage_number).state)*100 );
                    
#             esphome::modbus_controller::ModbusCommandItem battery_command = esphome::modbus_controller::ModbusCommandItem::create_write_multiple_command(controller, 118, battery_settings.size() ,
#                                                                                           battery_settings);
#             delay(200);
#             controller->queue_command(battery_command);
#             delay(200);            
            
#   - platform: template         # 120 Battery Low Voltage
#     name: ${name}_${inverter_name}_battery_low_voltage
#     id: ${inverter_name}_battery_low_voltage_number
#     unit_of_measurement: 'V'
#     optimistic: true
#     icon: mdi:sine-wave
#     min_value: 40.00
#     max_value: 52.00
#     step: 0.1
#     initial_value: 48.50
#     restore_value: true
#     mode: 'slider'
#     on_value:
#       then: 
#         - lambda: |-
#             esphome::modbus_controller::ModbusController *controller = id(${inverter_name}_modbus_controller);
#             std::vector<uint16_t> battery_settings(1);
#             battery_settings[0]  = uint16_t(  (id(${inverter_name}_battery_low_voltage_number).state)*100 );
                    
#             esphome::modbus_controller::ModbusCommandItem battery_command = esphome::modbus_controller::ModbusCommandItem::create_write_multiple_command(controller, 120, battery_settings.size() ,
#                                                                                           battery_settings);
#             delay(200);
#             controller->queue_command(battery_command);
#             delay(200);

#   - platform: template         # 126 Grid Charge Starting Voltage
#     name: ${name}_${inverter_name}_grid_charge_starting_voltage
#     id: ${inverter_name}_grid_charge_starting_voltage_number
#     unit_of_measurement: 'V'
#     optimistic: true
#     icon: mdi:sine-wave
#     min_value: 44.00
#     max_value: 53.00
#     step: 0.1
#     initial_value: 49.0
#     restore_value: true
#     mode: 'slider'
#     on_value:
#       then: 
#         - lambda: |-
#             esphome::modbus_controller::ModbusController *controller = id(${inverter_name}_modbus_controller);
#             std::vector<uint16_t> battery_settings(1);
#             battery_settings[0]  = uint16_t(  (id(${inverter_name}_grid_charge_starting_voltage_number).state)*100 );
                    
#             esphome::modbus_controller::ModbusCommandItem battery_command = esphome::modbus_controller::ModbusCommandItem::create_write_multiple_command(controller, 126, battery_settings.size() ,
#                                                                                           battery_settings);
#             delay(200);
#             controller->queue_command(battery_command);
#             delay(200);            
    
  
#   - platform: modbus_controller         # 108 Battery Max Charge current
#     use_write_multiple: true
#     modbus_controller_id: ${inverter_name}_modbus_controller
#     name: ${name}_${inverter_name}_battery_max_charge_current
#     id: ${inverter_name}_battery_max_charge_current_number
#     unit_of_measurement: 'A'
#     icon: mdi:current-dc
#     address: 108
#     value_type: U_WORD
#     min_value: 5
#     max_value: 185
#     step: 5
#     mode: 'slider'
      
#   - platform: modbus_controller         # 109 Battery Max Discharge current
#     use_write_multiple: true
#     modbus_controller_id: ${inverter_name}_modbus_controller
#     name: ${name}_${inverter_name}_battery_max_discharge_current
#     id: ${inverter_name}_battery_max_discharge_current_number
#     unit_of_measurement: 'A'
#     icon: mdi:current-dc
#     address: 109
#     value_type: U_WORD
#     min_value: 0
#     max_value: 185
#     step: 5
#     mode: 'slider'
      
#   - platform: modbus_controller         # 128 Grid Charge Battery current
#     use_write_multiple: true
#     modbus_controller_id: ${inverter_name}_modbus_controller
#     name: ${name}_${inverter_name}_grid_charge_battery_current
#     id: ${inverter_name}_grid_charge_battery_current_number
#     unit_of_measurement: 'A'
#     icon: mdi:current-dc
#     address: 128
#     value_type: U_WORD
#     min_value: 0
#     max_value: 185
#     step: 5
#     mode: 'slider'

#   - platform: modbus_controller            # 340 Max Sell Power
#     use_write_multiple: true
#     modbus_controller_id: ${inverter_name}_modbus_controller
#     name: ${name}_${inverter_name}_max_sell_power
#     id: ${inverter_name}_max_sell_power_number
#     address: 340
#     value_type: U_WORD
#     unit_of_measurement: 'W'
#     min_value: 0
#     max_value: 8000
#     step: 500
#     mode: 'slider'

    
#   - platform: modbus_controller            # 191 Grid Peak Shaving Power
#     use_write_multiple: true
#     modbus_controller_id: ${inverter_name}_modbus_controller
#     name: ${name}_${inverter_name}_grid_peak_shaving_power
#     id: ${inverter_name}_grid_peak_shaving_power_number
#     address: 191
#     value_type: U_WORD
#     unit_of_measurement: 'W'
#     icon: mdi:power
#     min_value: 0
#     max_value: 8000
#     step: 500
#     mode: 'slider'
    
    
# select:

#   - platform: modbus_controller
#     use_write_multiple: true
#     modbus_controller_id: ${inverter_name}_modbus_controller
#     name: ${name}_${inverter_name}_switch_on_off
#     id: ${inverter_name}_switch_on_off_select
#     address: 80
#     value_type: S_WORD
#     optionsmap:
#       "OFF": 0
#       "ON": 1
#     # skip_updates: 10
  
#   - platform: modbus_controller                   #243 Select Energy Pattern
#     use_write_multiple: true
#     modbus_controller_id: ${inverter_name}_modbus_controller
#     name: ${name}_${inverter_name}_battery_operate
#     id: ${inverter_name}_battery_operate
#     address: 213
#     value_type: U_WORD
#     optionsmap:
#       "According to the voltage": 0
#       "According to the capacity": 1
#       "No battery": 2
  
#   - platform: modbus_controller                   #141 Select Energy Pattern
#     use_write_multiple: true
#     modbus_controller_id: ${inverter_name}_modbus_controller
#     name: ${name}_${inverter_name}_energy_pattern
#     id: ${inverter_name}_energy_pattern
#     address: 141
#     value_type: U_WORD
#     optionsmap:
#       "Battery first": 0
#       "Load first": 1   
         
#   # - platform: modbus_controller                   #244 Select Work Mode
#     # use_write_multiple: true
#     # modbus_controller_id: ${inverter_name}_modbus_controller
#     # name: ${name}_${inverter_name}_work_mode
#     # id: ${inverter_name}_work_mode
#     # address: 244
#     # value_type: U_WORD
#     # optionsmap:
#       # "Selling First": 0
#       # "Zero Export + Limit to Load Only": 1
#       # "Limited to Home": 2    

#   # - platform: modbus_controller                  #280 Select Grid Peak Shaving
#     # use_write_multiple: true
#     # modbus_controller_id: ${inverter_name}_modbus_controller
#     # name: ${name}_${inverter_name}_grid_peak_shaving
#     # id: ${inverter_name}_grid_peak_shaving_select
#     # address: 280
#     # value_type: U_WORD
#     # optionsmap:
#       # "Disabled": 0
#       # "Enabled": 256
#     # lambda: |-
#       # // we are only interested in the 8th bit binary 0001 0000 0000 need to map the options 0, 256 in select 
#       # //ESP_LOGE("main","Modbus Number incoming value = %d",x);
#       # //ESP_LOGE("main","Modbus eval value = %d",(x & 0x0100));
#       # if ((x & 0x0100) == 0)
#         # return  std::string("Disabled");
#       # if ((x & 0x0100) == 256)
#         # return  std::string("Enabled");
#       # return {};
#     # write_lambda: |-
#       # //ESP_LOGE("main","Modbus write gets = %d",value);
#       # uint16_t unmodified =  id(${inverter_name}_grid_peak_shaving_raw).state;
#       # //ESP_LOGE("main","Modbus write unmodified = %d", unmodified);
#       # // optionsmap should only return 2 values... 0 , 256 so bitmask with complement 0x0100 to ensure we keep the original values in register. Then appply OR with the value that was chosen
#       # uint16_t modified = ((unmodified & ~0x0100) | value);
#       # //ESP_LOGE("main","Modbus write to write = %d", modified);
#       # return modified;    

# text_sensor:
#   - platform: modbus_controller            # 500 Overall State
#     modbus_controller_id: ${inverter_name}_modbus_controller
#     name: ${name}_${inverter_name}_overall_state
#     id: ${inverter_name}_overall_state
#     register_type: holding
#     raw_encode: HEXBYTES
#     address: 500
#     lambda: |- 
#       // uint16_t value = modbus_controller::word_from_hex_str(x, 0);
#       uint16_t value = modbus::helpers::word_from_hex_str(x, 0);
#       switch (value) {
#         case 0: return std::string("standby");
#         case 1: return std::string("selftest");
#         case 2: return std::string("normal");
#         case 3: return std::string("alarm");
#         case 4: return std::string("fault");
#         default: return std::string("unknown");
#       }      
