SeByDocKy/pvbrain2/pvbrain2/solar_charger/srne/device_srne.yaml

# ─────────────────────────────────────────────────────────────
#  SRNE Solar Charger – ESPHome modbus_controller
#  Optimised for ESPHome 2026.9.0
#   • register_count removed (derived from value_type)
#   • reuse_previous_range: true bridges address gaps
#   • multiply: 100 → 0.01 on numbers (2026.9.0 semantics)
#   • ModbusCommandItem::create_write_multiple_command kept
#     (batch writes E003, E005-E00E — deprecated 2026.9.0,
#      removed 2027.3.0, will need migration)
#
#  Modbus read ranges (holding):
#   A: 0x000A          (1 reg)    system info
#   B: 0x000C          (8 regs)   product model (response_size:16)
#   C: 0x001A          (1 reg)    modbus address
#   D: 0x0100–0x0122  (35 regs)   PV / output / stats / errors
#   E: 0xE001–0xE014  (20 regs)   battery parameters
# ─────────────────────────────────────────────────────────────
# Updated : 2026.08.06
# Version : 1.1.2
# GitHub  : https://github.com/SeByDocKy/pvbrain2

esphome:
  on_boot:
    # IMPORTANT: the list form (- priority:) is required so this trigger
    # MERGES with on_boot triggers declared by other packages.
    - priority: -100.0
      then:
        - script.execute: ${solar_charger_name}_write_E005_E00E_registers_script
    
time:
  - platform: homeassistant #sntp
    id: !extend my_time
    on_time:
      - seconds: ${my_second}
        minutes: ${my_minute}
        hours: ${my_hours}
        then:  
          - globals.set:
              id: ${solar_charger_name}_pv_energy_yesterday_global
              value: !lambda return ( id(${solar_charger_name}_pv_energy_yesterday_global) =  float( id(${solar_charger_name}_pv_energy_today).state) );         
                
          - globals.set:
              id: ${solar_charger_name}_battery_charging_energy_yesterday_global
              value: !lambda return ( id(${solar_charger_name}_battery_charging_energy_yesterday_global) =  float( id(${solar_charger_name}_battery_charging_energy_today).state) );        

globals:
  - id: ${solar_charger_name}_battery_coefficient
    type: int
    restore_value: yes

  - id: ${solar_charger_name}_battery_reco_global
    type: int

  - id: ${solar_charger_name}_current_load_charging_mode_global
    type: int  

  - id: ${solar_charger_name}_pv_energy_yesterday_global
    type: float
    restore_value: yes
    
  - id: ${solar_charger_name}_battery_charging_energy_yesterday_global
    type: float
    restore_value: yes
   
modbus_controller:

  - id: ${solar_charger_name}_modbus_controller
    address: ${solar_charger_modbus_address}
    modbus_id: ${solar_charger_modbus_id} #${solar_charger_name}_modbus
    setup_priority: -10
    update_interval: ${solar_charger_update_interval}
    
    # max_cmd_retries: 1        # default 4: a dead device would block the bus much longer
    # offline_skip_updates: 5   # re-probe every (5+1) x update_interval
    
sensor:

        #################### System Informations ##################

  - platform: modbus_controller
    modbus_controller_id: ${solar_charger_name}_modbus_controller
    id: ${solar_charger_name}_max_voltage_supported
    name: ${name}_${solar_charger_name}_max_voltage_supported
    address: 0x000A
    register_type: holding
    value_type: U_WORD
    accuracy_decimals: 0
    unit_of_measurement: 'V'
    state_class: measurement
    device_class: voltage
    skip_updates: 10
    icon: mdi:sine-wave
    bitmask: 0xFF00 #(Bits 15-8)

  - platform: modbus_controller
    modbus_controller_id: ${solar_charger_name}_modbus_controller
    id: ${solar_charger_name}_rated_charging_current
    name: ${name}_${solar_charger_name}_rated_charging_current
    address: 0x000A
    register_type: holding
    value_type: U_WORD
    skip_updates: 10
    accuracy_decimals: 0
    icon: mdi:current-dc
    unit_of_measurement: 'A'
    state_class: measurement
    device_class: current
    bitmask: 0x00FF #(Bits 7-0)

  # - platform: modbus_controller
    # modbus_controller_id: ${solar_charger_name}_modbus_controller
    # id: ${solar_charger_name}_rated_discharging_current
    # name: ${name}_${solar_charger_name}_rated_discharging_current
    # address: 0x000B
    # register_type: holding
    # value_type: U_WORD
    # skip_updates: 1 
    # accuracy_decimals: 0
    # icon: mdi:current-dc
    # unit_of_measurement: 'A'
    # bitmask: 0xFF00 #(Bits 15-8)  

  # - platform: modbus_controller
    # modbus_controller_id: ${solar_charger_name}_modbus_controller
    # id: ${solar_charger_name}_software_version
    # name: ${name}_${solar_charger_name}_software_version
    # register_type: holding
    # address: 0x014
    # value_type: U_DWORD
    # #response_size: 4
    # register_count: 2
    # skip_updates: 10
    # #raw_encode: NONE   

  # - platform: modbus_controller
    # modbus_controller_id: ${solar_charger_name}_modbus_controller
    # id: ${solar_charger_name}_hardware_version
    # name: ${name}_${solar_charger_name}_hardware_version
    # register_type: holding
    # address: 0x016
    # #response_size: 4
    # value_type: U_DWORD
    # #response_size: 4
    # register_count: 2
    # #raw_encode: NONE   
    
  # - platform: modbus_controller
    # modbus_controller_id: ${solar_charger_name}_modbus_controller
    # id: ${solar_charger_name}_product_serial_number
    # name: ${name}_${solar_charger_name}_product_serial_number
    # register_type: holding
    # address: 0x018
    # value_type: U_DWORD
    # #response_size: 4
    # register_count: 2
    # #response_size: 4
    # #raw_encode: NONE

  - platform: modbus_controller
    modbus_controller_id: ${solar_charger_name}_modbus_controller
    id: ${solar_charger_name}_modbus_adress
    name: ${name}_${solar_charger_name}_modbus_adress
    register_type: holding
    address: 0x01A
    value_type: U_WORD
    bitmask: 0xFF #(Bits 7-0)
    skip_updates: 10
    icon: mdi:numeric
    state_class: measurement

      ################ Controller dynamic information# ##############################

  - platform: modbus_controller
    modbus_controller_id: ${solar_charger_name}_modbus_controller
    id: ${solar_charger_name}_battery_soc
    name: ${name}_${solar_charger_name}_battery_soc
    address: 0x100
    unit_of_measurement: '%'
    register_type: holding
    value_type: U_WORD
    accuracy_decimals: 0
    state_class: measurement
    icon: mdi:percent
    skip_updates: 1 

  - platform: modbus_controller
    modbus_controller_id: ${solar_charger_name}_modbus_controller
    id: ${solar_charger_name}_battery_voltage
    name: ${name}_${solar_charger_name}_battery_voltage
    address: 0x101
    register_type: holding
    value_type: U_WORD
    accuracy_decimals: 2
    unit_of_measurement: 'V'
    state_class: measurement
    device_class: voltage
    skip_updates: 1 
    icon: mdi:sine-wave
    filters:
      - multiply: 0.1

  - platform: modbus_controller
    modbus_controller_id: ${solar_charger_name}_modbus_controller
    id: ${solar_charger_name}_charging_current
    name: ${name}_${solar_charger_name}_charging_current
    address: 0x102
    register_type: holding
    value_type: U_WORD
    skip_updates: 1 
    accuracy_decimals: 1
    state_class: measurement
    device_class: current
    icon: mdi:current-dc
    unit_of_measurement: 'A'
    filters:
      - multiply: 0.01
      
  - platform: template
    id: ${solar_charger_name}_battery_coeff
    name: ${name}_${solar_charger_name}_battery_coefficient
    lambda: |-
      return id(${solar_charger_name}_battery_coefficient);
    state_class: measurement
    icon: mdi:numeric

  - platform: template
    id: ${solar_charger_name}_charging_power
    name: ${name}_${solar_charger_name}_charging_power
    accuracy_decimals: 2
    icon: mdi:power
    unit_of_measurement: 'W'
    device_class: power
    state_class: measurement
    update_interval: ${solar_charger_template_update}
    lambda: |-
      return id(${solar_charger_name}_charging_current).state*id(${solar_charger_name}_battery_voltage).state;

  - platform: template
    id: ${solar_charger_name}_pv_battery_ratio
    name: ${name}_${solar_charger_name}_pv_battery_ratio
    accuracy_decimals: 1
    unit_of_measurement: '%'
    icon: mdi:percent
    state_class: measurement
    update_interval: ${solar_charger_template_update}
    lambda: |-
      if (id(${solar_charger_name}_pv_power).state != 0.0) {
        return (id(${solar_charger_name}_charging_power).state/id(${solar_charger_name}_pv_power).state)*100.0;    
      }
      else{
        return 0.0;
      }

  - platform: total_daily_energy
    id: ${solar_charger_name}_battery_charging_energy_today
    name: ${name}_${solar_charger_name}_battery_charging_energy_today
    power_id: ${solar_charger_name}_charging_power
    unit_of_measurement: 'kWh'
    state_class: total_increasing
    device_class: energy
    accuracy_decimals: 1
    icon: mdi:counter
    method: trapezoid
    filters:
      - multiply: 0.001
    
  - platform: template
    name: ${name}_${solar_charger_name}_battery_charging_energy_yesterday
    id: ${solar_charger_name}_battery_charging_energy_yesterday
    unit_of_measurement: 'kWh'
    state_class: total_increasing
    device_class: energy
    accuracy_decimals: 1
    icon: mdi:counter
    update_interval: ${solar_charger_template_update}
    lambda: |-
      return (id(${solar_charger_name}_battery_charging_energy_yesterday).state = id(${solar_charger_name}_battery_charging_energy_yesterday_global));

  - platform: modbus_controller
    modbus_controller_id: ${solar_charger_name}_modbus_controller
    id: ${solar_charger_name}_device_temperature
    name: ${name}_${solar_charger_name}_device_temperature
    address: 0x103
    unit_of_measurement: '°C'
    device_class: temperature
    state_class: measurement
    icon: mdi:thermometer
    register_type: holding
    value_type: U_WORD
    accuracy_decimals: 1
    bitmask: 0x7F00 #(Bits 14-8)

  - platform: modbus_controller
    modbus_controller_id: ${solar_charger_name}_modbus_controller
    id: ${solar_charger_name}_battery_temperature
    name: ${name}_${solar_charger_name}_battery_temperature
    address: 0x103
    unit_of_measurement: '°C'
    register_type: holding
    value_type: U_WORD
    accuracy_decimals: 1
    icon: mdi:thermometer
    bitmask: 0x7F #(Bits 7-0)

  # - platform: modbus_controller
    # modbus_controller_id: ${solar_charger_name}_modbus_controller
    # id: ${solar_charger_name}_load_dc_voltage
    # name: ${name}_${solar_charger_name}_load_dc_voltage
    # address: 0x104
    # register_type: holding
    # value_type: U_WORD
    # accuracy_decimals: 1
    # unit_of_measurement: 'V'
    # skip_updates: 1 
    # icon: mdi:sine-wave
    # filters:
      # - multiply: 0.1
  
  # - platform: modbus_controller
    # modbus_controller_id: ${solar_charger_name}_modbus_controller
    # id: ${solar_charger_name}_load_dc_current
    # name: ${name}_${solar_charger_name}_load_dc_current
    # address: 0x105
    # register_type: holding
    # value_type: U_WORD
    # skip_updates: 1 
    # accuracy_decimals: 2
    # icon: mdi:current-dc
    # unit_of_measurement: 'A'
    # filters:
      # - multiply: 0.01

  # - platform: modbus_controller
    # modbus_controller_id: ${solar_charger_name}_modbus_controller
    # id: ${solar_charger_name}_load_dc_power
    # name: ${name}_${solar_charger_name}_load_dc_power
    # address: 0x106
    # register_type: holding
    # value_type: U_WORD
    # skip_updates: 1 
    # accuracy_decimals: 2
    # icon: mdi:power
    # unit_of_measurement: 'W'

         ############################## Solar Panel Informations ##################

  - platform: modbus_controller
    modbus_controller_id: ${solar_charger_name}_modbus_controller
    id: ${solar_charger_name}_pv_voltage
    name: ${name}_${solar_charger_name}_pv_voltage
    address: 0x107
    reuse_previous_range: true                     # bridge 0x103→0x107
    register_type: holding
    value_type: U_WORD
    accuracy_decimals: 2
    unit_of_measurement: 'V'
    skip_updates: 1
    icon: mdi:sine-wave
    state_class: measurement
    device_class: voltage
    filters:
      - multiply: 0.1

  - platform: modbus_controller
    modbus_controller_id: ${solar_charger_name}_modbus_controller
    id: ${solar_charger_name}_pv_current
    name: ${name}_${solar_charger_name}_pv_current
    address: 0x108
    register_type: holding
    value_type: U_WORD
    skip_updates: 1 
    accuracy_decimals: 2
    icon: mdi:current-dc
    unit_of_measurement: 'A'
    state_class: measurement
    device_class: current
    filters:
      - multiply: 0.01

  - platform: modbus_controller
    modbus_controller_id: ${solar_charger_name}_modbus_controller
    id: ${solar_charger_name}_pv_power
    name: ${name}_${solar_charger_name}_pv_power
    address: 0x109
    register_type: holding
    value_type: U_WORD
    skip_updates: 1 
    accuracy_decimals: 2
    icon: mdi:power
    unit_of_measurement: 'W'
    state_class: measurement
    device_class: power

  - platform: total_daily_energy
    id: ${solar_charger_name}_pv_energy_today
    name: ${name}_${solar_charger_name}_pv_energy_today
    power_id: ${solar_charger_name}_pv_power
    unit_of_measurement: 'kWh'
    state_class: total_increasing
    device_class: energy
    accuracy_decimals: 1
    method: trapezoid
    filters:
        # Multiplication factor from W to kW is 0.001
      - multiply: 0.001
    icon: mdi:counter
    
  - platform: template
    id: ${solar_charger_name}_pv_energy_yesterday
    name: ${name}_${solar_charger_name}_pv_energy_yesterday
    unit_of_measurement: 'kWh'
    accuracy_decimals: 1
    icon: mdi:counter
    state_class: total_increasing
    device_class: energy
    update_interval: ${solar_charger_template_update}
    lambda: |-
      return (id( ${solar_charger_name}_pv_energy_yesterday).state = id( ${solar_charger_name}_pv_energy_yesterday_global ));
    
  # - platform: modbus_controller
    # modbus_controller_id: ${solar_charger_name}_modbus_controller
    # id: ${solar_charger_name}_load_dc_charging_status
    # name: ${name}_${solar_charger_name}_load_dc_charging_status
    # address: 0x010A
    # register_type: holding
    # value_type: U_WORD
    # accuracy_decimals: 0
    # skip_updates: 1
    # bitmask: 1
    # icon: mdi:account-hard-hat
    
        ############################## Battery statistics  ############################

  - platform: modbus_controller
    modbus_controller_id: ${solar_charger_name}_modbus_controller
    id: ${solar_charger_name}_battery_minimum_voltage_today
    name: ${name}_${solar_charger_name}_battery_minimum_voltage_today
    address: 0x010B
    reuse_previous_range: true                     # bridge 0x109→0x10B
    register_type: holding
    value_type: U_WORD
    accuracy_decimals: 1
    unit_of_measurement: 'V'
    state_class: measurement
    device_class: voltage
    skip_updates: 1 
    icon: mdi:sine-wave
    filters:
      - multiply: 0.1

  - platform: modbus_controller
    modbus_controller_id: ${solar_charger_name}_modbus_controller
    id: ${solar_charger_name}_battery_maximum_voltage_today
    name: ${name}_${solar_charger_name}_battery_maximum_voltage_today
    address: 0x010C
    register_type: holding
    value_type: U_WORD
    accuracy_decimals: 2
    unit_of_measurement: 'V'
    state_class: measurement
    device_class: voltage
    skip_updates: 1 
    icon: mdi:sine-wave
    filters:
      - multiply: 0.1

  - platform: modbus_controller
    modbus_controller_id: ${solar_charger_name}_modbus_controller
    id: ${solar_charger_name}_battery_maximum_charging_current_today
    name: ${name}_${solar_charger_name}_battery_maximum_charging_current_today
    address: 0x010D
    register_type: holding
    value_type: U_WORD
    skip_updates: 1 
    accuracy_decimals: 1
    icon: mdi:current-dc
    unit_of_measurement: 'A'
    state_class: measurement
    device_class: current
    filters:
      - multiply: 0.01

  - platform: modbus_controller
    modbus_controller_id: ${solar_charger_name}_modbus_controller
    id: ${solar_charger_name}_battery_maximum_discharging_current_today
    name: ${name}_${solar_charger_name}_battery_maximum_discharging_current_today
    address: 0x010E
    register_type: holding
    value_type: U_WORD
    skip_updates: 1 
    accuracy_decimals: 1
    icon: mdi:current-dc
    unit_of_measurement: 'A'
    state_class: measurement
    device_class: current
    filters:
      - multiply: 0.01
      
  - platform: modbus_controller
    modbus_controller_id: ${solar_charger_name}_modbus_controller
    id: ${solar_charger_name}_battery_maximum_charging_power_current_today
    name: ${name}_${solar_charger_name}_battery_maximum_charging_power_current_today
    address: 0x010F
    register_type: holding
    value_type: U_WORD
    skip_updates: 1 
    accuracy_decimals: 1
    icon: mdi:power
    unit_of_measurement: 'W'
    state_class: measurement
    device_class: power
 
  - platform: modbus_controller
    modbus_controller_id: ${solar_charger_name}_modbus_controller
    id: ${solar_charger_name}_battery_maximum_discharging_power_current_today
    name: ${name}_${solar_charger_name}_battery_maximum_discharging_power_current_today
    address: 0x0110
    register_type: holding
    value_type: U_WORD
    skip_updates: 1 
    accuracy_decimals: 2
    icon: mdi:power
    unit_of_measurement: 'W'
    state_class: measurement
    device_class: power

  - platform: modbus_controller
    modbus_controller_id: ${solar_charger_name}_modbus_controller
    id: ${solar_charger_name}_energy_generation_today
    name: ${name}_${solar_charger_name}_energy_generation_today
    address: 0x0113
    reuse_previous_range: true                     # bridge 0x0110→0x0113
    register_type: holding
    value_type: U_WORD
    skip_updates: 1
    accuracy_decimals: 1
    icon: mdi:power
    unit_of_measurement: 'kWh'
    state_class: total_increasing
    device_class: energy
    filters:
      - multiply: 0.001

  # - platform: modbus_controller
    # modbus_controller_id: ${solar_charger_name}_modbus_controller
    # id: ${solar_charger_name}_energy_consumption_today
    # name: ${name}_${solar_charger_name}_energy_consumption_today
    # address: 0x0114
    # register_type: holding
    # value_type: U_WORD
    # skip_updates: 1 
    # accuracy_decimals: 1
    # icon: mdi:power
    # unit_of_measurement: 'kWh'
    # filters:
      # - multiply: 0.001       
  
      #################### Historical data information ##################

  - platform: modbus_controller
    modbus_controller_id: ${solar_charger_name}_modbus_controller
    id: ${solar_charger_name}_total_number_operating_day
    name: ${name}_${solar_charger_name}_total_number_operating_day
    address: 0x0115
    reuse_previous_range: true                     # bridge 0x0113→0x0115
    register_type: holding
    value_type: U_WORD
    skip_updates: 1
    accuracy_decimals: 0
    state_class: measurement
    icon: mdi:calendar-today

  - platform: modbus_controller
    modbus_controller_id: ${solar_charger_name}_modbus_controller
    id: ${solar_charger_name}_total_number_battery_overdischarge
    name: ${name}_${solar_charger_name}_total_number_battery_overdischarge
    address: 0x0116
    register_type: holding
    value_type: U_WORD
    skip_updates: 1 
    accuracy_decimals: 0
    state_class: measurement
    icon: mdi:flash-alert

  - platform: modbus_controller
    modbus_controller_id: ${solar_charger_name}_modbus_controller
    id: ${solar_charger_name}_total_number_battery_fullcharge
    name: ${name}_${solar_charger_name}_total_number_battery_fullcharge
    address: 0x0117
    register_type: holding
    value_type: U_WORD
    skip_updates: 1 
    accuracy_decimals: 0
    state_class: measurement
    icon: mdi:battery-charging-high

  - platform: modbus_controller
    modbus_controller_id: ${solar_charger_name}_modbus_controller
    id: ${solar_charger_name}_total_charging_ah_battery
    name: ${name}_${solar_charger_name}_total_charging_ah_battery
    address: 0x0118
    register_type: holding
    value_type: U_DWORD
    skip_updates: 1
    accuracy_decimals: 0
    icon: mdi:counter
    unit_of_measurement: 'Ah'

  # - platform: modbus_controller
    # modbus_controller_id: ${solar_charger_name}_modbus_controller
    # id: ${solar_charger_name}_total_discharging_ah_battery
    # name: ${name}_${solar_charger_name}_total_discharging_ah_battery
    # address: 0x011A
    # register_type: holding
    # value_type: U_DWORD
    # skip_updates: 1 
    # accuracy_decimals: 0
    # icon: mdi:power
    # unit_of_measurement: 'Ah'     
    
  - platform: modbus_controller
    modbus_controller_id: ${solar_charger_name}_modbus_controller
    id: ${solar_charger_name}_energy_generation_total
    name: ${name}_${solar_charger_name}_energy_generation_total
    address: 0x011C
    reuse_previous_range: true                     # bridge 0x0118→0x011C
    register_type: holding
    value_type: U_DWORD
    skip_updates: 1
    accuracy_decimals: 1
    icon: mdi:power
    unit_of_measurement: 'kWh'
    state_class: total_increasing
    device_class: energy
    filters:
      - multiply: 0.001

  # - platform: modbus_controller
    # modbus_controller_id: ${solar_charger_name}_modbus_controller
    # id: ${solar_charger_name}_energy_consumption_total
    # name: ${name}_${solar_charger_name}_energy_consumption_total
    # address: 0x011E
    # register_type: holding
    # value_type: U_DWORD
    # skip_updates: 1 
    # accuracy_decimals: 1
    # icon: mdi:power
    # unit_of_measurement: 'kWh'
    # filters:
      # - multiply: 0.001    

  - platform: modbus_controller
    modbus_controller_id: ${solar_charger_name}_modbus_controller
    id: ${solar_charger_name}_warnings_and_errors_hi
    name: ${name}_${solar_charger_name}_warnings_and_errors_hi
    icon: mdi:alert-circle
    address: 0x0121
    register_type: holding
    value_type: U_WORD
    skip_updates: 1
    lambda: |-
      //ESP_LOGD("Register 0x0121","Lambda incoming value=%d - data array size is %d",int(x),data.size());
      id(${solar_charger_name}_warnings_and_errors_hi_template).publish_state(int(x));
      return x;
   
  - platform: template
    id: ${solar_charger_name}_warnings_and_errors_hi_template
    #name: ${solar_charger_name}_warnings_and_errors_hi_template 
    icon: mdi:alert-circle
    accuracy_decimals: 0
    #update_interval: ${solar_charger_template_update}
    on_value:
      then: 
        - script.execute: 
            id: ${solar_charger_name}_warnings_and_errors_hi_script

  - platform: modbus_controller
    modbus_controller_id: ${solar_charger_name}_modbus_controller
    id: ${solar_charger_name}_warnings_and_errors_low
    name: ${name}_${solar_charger_name}_warnings_and_errors_low 
    icon: mdi:alert-circle
    address: 0x0122
    register_type: holding
    value_type: U_WORD
    skip_updates: 1
    lambda: |-
      //ESP_LOGD("Register 0x0122","Lambda incoming value=%d - data array size is %d",int(x),data.size());
      id(${solar_charger_name}_warnings_and_errors_low_template).publish_state(int(x));
      return x;
   
  - platform: template
    id: ${solar_charger_name}_warnings_and_errors_low_template
    #name: ${solar_charger_name}_warnings_and_errors_low_template 
    icon: mdi:alert-circle
    accuracy_decimals: 0
    #update_interval: ${solar_charger_template_update}
    on_value:
      then: 
        - script.execute: 
            id: ${solar_charger_name}_warnings_and_errors_low_script         

             ################## Load informations  ####################
  
  # - platform: modbus_controller
    # modbus_controller_id: ${solar_charger_name}_modbus_controller
    # id: ${solar_charger_name}_street_light_status
    # name: ${name}_${solar_charger_name}_street_light
    # icon: mdi:outdoor-lamp
    # bitmask: 0x8000
    # register_type: holding
    # value_type: U_DWORD
    # skip_updates: 1
    # accuracy_decimals: 0
    # address: 0x0120

  # - platform: modbus_controller
    # modbus_controller_id: ${solar_charger_name}_modbus_controller
    # id: ${solar_charger_name}_street_brightness_level
    # name: ${name}_${solar_charger_name}_street_brightness_level
    # icon: mdi:outdoor-lamp
    # bitmask: 0x7F00
    # register_type: holding
    # value_type: U_DWORD
    # skip_updates: 1 
    # accuracy_decimals: 0
    # address: 0x0120  
    
      ############################ Battery parameters ###################

  - platform: modbus_controller
    modbus_controller_id: ${solar_charger_name}_modbus_controller
    id: ${solar_charger_name}_charging_current_limit
    name: ${name}_${solar_charger_name}_charging_current_limit
    address: 0xE001
    register_type: holding
    value_type: U_WORD
    unit_of_measurement: 'A'
    icon: mdi:current-dc
    state_class: measurement
    device_class: current
    accuracy_decimals: 0
    filters:
      - multiply: 0.01

  - platform: modbus_controller
    modbus_controller_id: ${solar_charger_name}_modbus_controller
    id: ${solar_charger_name}_battery_capacity
    name: ${name}_${solar_charger_name}_battery_capacity
    address: 0xE002
    register_type: holding
    value_type: U_WORD
    unit_of_measurement: 'Ah'
    state_class: total_increasing
    device_class: energy
    icon: mdi:car-battery
    accuracy_decimals: 0

  - platform: modbus_controller
    modbus_controller_id: ${solar_charger_name}_modbus_controller
    id: ${solar_charger_name}_battery_voltage_setting
    name: ${name}_${solar_charger_name}_battery_voltage_setting
    address: 0xE003
    register_type: holding
    value_type: U_WORD
    skip_updates: 1
    bitmask: 0xFF00 #(Bits 15-8)
    accuracy_decimals: 0
    unit_of_measurement: 'V'
    state_class: measurement
    device_class: voltage
    icon: mdi:car-battery 
    
  - platform: modbus_controller
    modbus_controller_id: ${solar_charger_name}_modbus_controller
    id: ${solar_charger_name}_battery_voltage_recognized
    name: ${name}_${solar_charger_name}_battery_voltage_recognized
    address: 0xE003
    register_type: holding
    value_type: U_WORD
    skip_updates: 1
    bitmask: 0xFF #(Bits 15-8)
    accuracy_decimals: 0
    unit_of_measurement: 'V'
    icon: mdi:car-battery
    state_class: measurement
    device_class: voltage
    lambda: |-
      //ESP_LOGD("RegE003 sensor", "raw value (%d)", (int)x);
      id(${solar_charger_name}_battery_reco_global) = (int)x;
      return {};

  - platform: modbus_controller
    modbus_controller_id: ${solar_charger_name}_modbus_controller
    id: ${solar_charger_name}_battery_type
    name: ${name}_${solar_charger_name}_battery_type
    address: 0xE004
    register_type: holding
    value_type: U_WORD
    skip_updates: 1
    icon: mdi:car-battery 
      
  ################# Battery voltage sensors ##########
    
          ########  1 ########

  - platform: modbus_controller
    modbus_controller_id: ${solar_charger_name}_modbus_controller
    id: ${solar_charger_name}_over_voltage_threshold
    name: ${name}_${solar_charger_name}_over_voltage_threshold
    address: 0xE005
    register_type: holding
    value_type: U_WORD
    accuracy_decimals: 1
    unit_of_measurement: 'V'
    state_class: measurement
    device_class: voltage
    skip_updates: 1
    lambda: |-
      return x*0.1*id(${solar_charger_name}_battery_coefficient);  
    icon: mdi:sine-wave

          ########  2 ########

  - platform: modbus_controller
    modbus_controller_id: ${solar_charger_name}_modbus_controller
    id: ${solar_charger_name}_charging_voltage_limit
    name: ${name}_${solar_charger_name}_charging_voltage_limit
    address: 0xE006
    register_type: holding
    value_type: U_WORD
    accuracy_decimals: 1
    unit_of_measurement: 'V'
    state_class: measurement
    device_class: voltage
    skip_updates: 1
    lambda: |-
      return x*0.1*id(${solar_charger_name}_battery_coefficient);  
    icon: mdi:sine-wave 

              ########  3 ########
  
  - platform: modbus_controller
    modbus_controller_id: ${solar_charger_name}_modbus_controller
    id: ${solar_charger_name}_equalizing_charge_voltage
    name: ${name}_${solar_charger_name}_equalizing_charge_voltage
    address: 0xE007
    register_type: holding
    value_type: U_WORD
    accuracy_decimals: 1
    unit_of_measurement: 'V'
    state_class: measurement
    device_class: voltage
    skip_updates: 1
    lambda: |-
      return x*0.1*id(${solar_charger_name}_battery_coefficient);  
    icon: mdi:sine-wave

            ########  4 ########        
  
  - platform: modbus_controller
    modbus_controller_id: ${solar_charger_name}_modbus_controller
    id: ${solar_charger_name}_boost_voltage
    name: ${name}_${solar_charger_name}_boost_voltage
    address: 0xE008
    register_type: holding
    value_type: U_WORD
    accuracy_decimals: 1
    unit_of_measurement: 'V'
    state_class: measurement
    device_class: voltage
    skip_updates: 1
    lambda: |-
      return x*0.1*id(${solar_charger_name}_battery_coefficient);  
    icon: mdi:sine-wave

          ######## 5 ########
   
  - platform: modbus_controller
    modbus_controller_id: ${solar_charger_name}_modbus_controller
    id: ${solar_charger_name}_float_voltage
    name: ${name}_${solar_charger_name}_float_voltage
    address: 0xE009
    register_type: holding
    value_type: U_WORD
    accuracy_decimals: 1
    unit_of_measurement: 'V'
    skip_updates: 1
    lambda: |-
      return x*0.1*id(${solar_charger_name}_battery_coefficient);  
    icon: mdi:sine-wave


            ######## 6 ########

  - platform: modbus_controller
    modbus_controller_id: ${solar_charger_name}_modbus_controller
    id: ${solar_charger_name}_boost_charging_recovery_voltage
    name: ${name}_${solar_charger_name}_boost_charging_recovery_voltage
    address: 0xE00A
    register_type: holding
    value_type: U_WORD
    accuracy_decimals: 1
    unit_of_measurement: 'V'
    state_class: measurement
    device_class: voltage
    skip_updates: 1
    lambda: |-
      return x*0.1*id(${solar_charger_name}_battery_coefficient);  
    icon: mdi:sine-wave

              ######## 7 ########

  - platform: modbus_controller
    modbus_controller_id: ${solar_charger_name}_modbus_controller
    id: ${solar_charger_name}_over_discharge_recovery_voltage
    name: ${name}_${solar_charger_name}_over_discharge_recovery_voltage
    address: 0xE00B
    register_type: holding
    value_type: U_WORD
    accuracy_decimals: 1
    unit_of_measurement: 'V'
    state_class: measurement
    device_class: voltage
    skip_updates: 1
    lambda: |-
      return x*0.1*id(${solar_charger_name}_battery_coefficient);  
    icon: mdi:sine-wave

            ######## 8 ########

  - platform: modbus_controller
    modbus_controller_id: ${solar_charger_name}_modbus_controller
    id: ${solar_charger_name}_under_voltage_warning
    name: ${name}_${solar_charger_name}_under_voltage_warning
    address: 0xE00C
    register_type: holding
    value_type: U_WORD
    accuracy_decimals: 1
    unit_of_measurement: 'V'
    state_class: measurement
    device_class: voltage
    skip_updates: 1
    lambda: |-
      return x*0.1*id(${solar_charger_name}_battery_coefficient);  
    icon: mdi:sine-wave

        ######## 9 ########

  - platform: modbus_controller
    modbus_controller_id: ${solar_charger_name}_modbus_controller
    id: ${solar_charger_name}_over_discharge_voltage
    name: ${name}_${solar_charger_name}_over_discharge_voltage
    address: 0xE00D
    register_type: holding
    value_type: U_WORD
    accuracy_decimals: 1
    unit_of_measurement: 'V'
    state_class: measurement
    device_class: voltage
    skip_updates: 1
    lambda: |-
      return x*0.1*id(${solar_charger_name}_battery_coefficient);  
    icon: mdi:sine-wave

        ######## 10 ########

  - platform: modbus_controller
    modbus_controller_id: ${solar_charger_name}_modbus_controller
    id: ${solar_charger_name}_discharge_limit_voltage
    name: ${name}_${solar_charger_name}_discharge_limit_voltage
    address: 0xE00E
    register_type: holding
    value_type: U_WORD
    accuracy_decimals: 1
    unit_of_measurement: 'V'
    state_class: measurement
    device_class: voltage
    skip_updates: 1
    lambda: |-
      return x*0.1*id(${solar_charger_name}_battery_coefficient);  
    icon: mdi:sine-wave   

      ############## Delay  ##############
  
  - platform: modbus_controller
    modbus_controller_id: ${solar_charger_name}_modbus_controller
    id: ${solar_charger_name}_overdischarge_time_delay
    name: ${name}_${solar_charger_name}_overdischarge_time_delay
    address: 0xE010
    reuse_previous_range: true                     # bridge 0xE00E→0xE010
    register_type: holding
    value_type: U_WORD
    accuracy_decimals: 0
    unit_of_measurement: 's'
    state_class: measurement
    icon: mdi:timer-sand
    skip_updates: 1
   
  - platform: modbus_controller
    modbus_controller_id: ${solar_charger_name}_modbus_controller
    id: ${solar_charger_name}_equalizing_charging_time
    name: ${name}_${solar_charger_name}_equalizing_charging_time
    address: 0xE011
    value_type: U_WORD
    register_type: holding
    unit_of_measurement: 'min'
    state_class: measurement
    icon: mdi:timer-sand
    accuracy_decimals: 0
    skip_updates: 1

  - platform: modbus_controller
    modbus_controller_id: ${solar_charger_name}_modbus_controller
    id: ${solar_charger_name}_boost_charging_time
    name: ${name}_${solar_charger_name}_boost_charging_time
    address: 0xE012
    value_type: U_WORD
    register_type: holding
    unit_of_measurement: 'min'
    state_class: measurement
    icon: mdi:timer-sand
    accuracy_decimals: 0
    skip_updates: 1

  - platform: modbus_controller
    modbus_controller_id: ${solar_charger_name}_modbus_controller
    id: ${solar_charger_name}_equalizing_charging_interval
    name: ${name}_${solar_charger_name}_equalizing_charging_interval
    address: 0xE013
    value_type: U_WORD
    register_type: holding
    unit_of_measurement: 'day'
    state_class: measurement
    icon: mdi:timer-sand
    accuracy_decimals: 0
    skip_updates: 1 

  - platform: modbus_controller
    modbus_controller_id: ${solar_charger_name}_modbus_controller
    id: ${solar_charger_name}_temperature_compensation_factor
    name: ${name}_${solar_charger_name}_temperature_compensation_factor
    address: 0xE014
    register_type: holding
    value_type: U_WORD
    accuracy_decimals: 0
    unit_of_measurement: 'mV/°C/2V'
    state_class: measurement
    icon: mdi:thermometer
    skip_updates: 1
    filters:
      - multiply: -1

  # - platform: modbus_controller
    # modbus_controller_id: ${solar_charger_name}_modbus_controller
    # id: ${solar_charger_name}_load_working_mode
    # name: ${name}_${solar_charger_name}_load_working_mode
    # address: 0xE01D
    # register_type: holding
    # value_type: U_WORD
    # accuracy_decimals: 0
    # icon: mdi:account-hard-hat
    # skip_updates: 1

# switch:
  
  # - platform: modbus_controller
    # modbus_controller_id: ${solar_charger_name}_modbus_controller
    # id: ${solar_charger_name}_load_on_off_command
    # name: ${name}_${solar_charger_name}_load_on_off_command
    # register_type: holding
    # address: 0x010A
    # bitmask: 1

  # - platform: template
    # id: ${solar_charger_name}_load_dc_on_off_command
    # name: ${name}_${solar_charger_name}_load_dc_on_off_command
    # optimistic: true
    # turn_on_action:
      # - script.execute: ${solar_charger_name}_turn_on_dc_load_script
    # turn_off_action:
      # - script.execute: ${solar_charger_name}_turn_off_dc_load_script

select:

  - platform: template
    id: ${solar_charger_name}_battery_voltage_setting_select
    name: ${name}_${solar_charger_name}_battery_voltage_setting_select
    optimistic: true
    options:
      - '12V'
      - '24V'
      - '36V'
      - '48V'
      - 'User defined'
    initial_option: '48V'
    restore_value: true
    icon: mdi:car-battery
    on_value:
      then: 
        - lambda: !lambda |-
            id(${solar_charger_name}_battery_coefficient) = (i + 1);
        - script.execute: ${solar_charger_name}_update_template_numbers_script 

        - script.execute: 
            id: ${solar_charger_name}_write_E003_register_script

  # - platform: modbus_controller
    # modbus_controller_id: ${solar_charger_name}_modbus_controller
    # id: ${solar_charger_name}_load_charging_mode_select
    # name: ${name}_${solar_charger_name}_load_charging_mode_select
    # address: 0xE01D
    # value_type: U_WORD
    # icon: mdi:list-status
    # optionsmap:
      # "Sole control, light control over on/off of load": 0
      # "Load turned on by light control and goes off after +1h": 1
      # "Load turned on by light control and goes off after +2h": 2
      # "Load turned on by light control and goes off after +3h": 3
      # "Load turned on by light control and goes off after +4h": 4
      # "Load turned on by light control and goes off after +5h": 5
      # "Load turned on by light control and goes off after +6h": 6
      # "Load turned on by light control and goes off after +7h": 7
      # "Load turned on by light control and goes off after +8h": 8
      # "Load turned on by light control and goes off after +9h": 9
      # "Load turned on by light control and goes off after +10h": 10
      # "Load turned on by light control and goes off after +11h": 11
      # "Load turned on by light control and goes off after +12h": 12
      # "Load turned on by light control and goes off after +13h": 13
      # "Load turned on by light control and goes off after +14h": 14
      # "Manual mode": 15
      # "Debugging mode": 16
      # "Normal mode": 17
 
  - platform: modbus_controller
    modbus_controller_id: ${solar_charger_name}_modbus_controller
    id: ${solar_charger_name}_battery_type_select
    name: ${name}_${solar_charger_name}_battery_type_select
    address: 0xE004
    value_type: U_WORD
    icon: mdi:car-battery
    optionsmap:
      "User defined": 0
      "Open (FLD)": 1
      "Sealed (SLD)": 2
      "Gel": 3
      "Lithium": 4

number: 
      ############## Delay  ##############
      
  - platform: modbus_controller
    modbus_controller_id: ${solar_charger_name}_modbus_controller
    id: ${solar_charger_name}_overdischarge_time_delay_number
    name: ${name}_${solar_charger_name}_overdischarge_time_delay_number
    address: 0xE010
    value_type: U_WORD
    unit_of_measurement: 's'
    icon: mdi:timer-sand
    min_value: 0
    max_value: 120
    step:  1
    mode: 'slider'

  - platform: modbus_controller
    modbus_controller_id: ${solar_charger_name}_modbus_controller
    id: ${solar_charger_name}_equalizing_charging_time_number
    name: ${name}_${solar_charger_name}_equalizing_charging_time_number
    address: 0xE011
    value_type: U_WORD
    unit_of_measurement: 'min'
    icon: mdi:timer-sand
    min_value: 0
    max_value: 300
    step:  10
    mode: 'slider'

  - platform: modbus_controller
    modbus_controller_id: ${solar_charger_name}_modbus_controller
    id: ${solar_charger_name}_boost_charging_time_number
    name: ${name}_${solar_charger_name}_boost_charging_time_number
    address: 0xE012
    value_type: U_WORD
    unit_of_measurement: 'min'
    icon: mdi:timer-sand
    min_value: 0
    max_value: 300
    step:  10
    mode: 'slider'

  - platform: modbus_controller
    modbus_controller_id: ${solar_charger_name}_modbus_controller
    id: ${solar_charger_name}_equalizing_charging_interval_number
    name: ${name}_${solar_charger_name}_equalizing_charging_interval_number
    address: 0xE013
    value_type: U_WORD
    unit_of_measurement: 'day'
    icon: mdi:timer-sand
    min_value: 0
    max_value: 255
    step:  5
    mode: 'slider'  

  - platform: modbus_controller
    modbus_controller_id: ${solar_charger_name}_modbus_controller
    id: ${solar_charger_name}_temperature_compensation_coefficient_number
    name: ${name}_${solar_charger_name}_temperature_compensation_coefficient_number
    address: 0xE014
    value_type: U_WORD
    unit_of_measurement: 'mV/°C/2V'
    icon: mdi:thermometer
    min_value: -5
    max_value: 0
    step:  1
    multiply: -1
    mode: 'slider' 

          ################# Battery's voltages ##############

             ######### 1 #########

  - platform: template
    id: ${solar_charger_name}_over_voltage_threshold_number
    name: ${name}_${solar_charger_name}_over_voltage_threshold_number
    optimistic: true
    unit_of_measurement: 'V'
    icon: mdi:sine-wave
    min_value: 14
    max_value: 16
    step:  0.1
    initial_value: 15
    restore_value: true
    mode: 'slider'
    on_value:
      then: 
        - script.execute: ${solar_charger_name}_write_E005_E00E_registers_script
 
             ######### 2 #########
             
  - platform: template
    id: ${solar_charger_name}_charging_voltage_limit_number
    name: ${name}_${solar_charger_name}_charging_voltage_limit_number
    optimistic: true
    unit_of_measurement: 'V'
    icon: mdi:sine-wave
    min_value: 14
    max_value: 15.5
    step: 0.1
    initial_value: 14.9
    restore_value: true
    mode: 'slider'
    on_value:
      then: 
        - script.execute: ${solar_charger_name}_write_E005_E00E_registers_script
  
            ######### 3 #########

  - platform: template
    id: ${solar_charger_name}_equalizing_charge_voltage_number
    name: ${name}_${solar_charger_name}_equalizing_charge_voltage_number
    optimistic: true
    unit_of_measurement: 'V'
    icon: mdi:sine-wave
    min_value: 12
    max_value: 14.5
    step: 0.1
    initial_value: 14
    restore_value: true
    mode: 'slider'
    on_value:
      then: 
        - script.execute: ${solar_charger_name}_write_E005_E00E_registers_script

          ######### 4 #########
 
  - platform: template
    id: ${solar_charger_name}_boost_voltage_number
    name: ${name}_${solar_charger_name}_boost_voltage_number
    optimistic: true
    unit_of_measurement: 'V'
    icon: mdi:sine-wave
    min_value: 12
    max_value: 14.5
    step: 0.1
    initial_value: 14
    restore_value: true
    mode: 'slider'
    on_value:
      then: 
        - script.execute: ${solar_charger_name}_write_E005_E00E_registers_script

          ######### 5 #########

  - platform: template
    id: ${solar_charger_name}_float_voltage_number
    name: ${name}_${solar_charger_name}_float_voltage_number
    optimistic: true
    unit_of_measurement: 'V'
    icon: mdi:sine-wave
    min_value: 12
    max_value: 14.5
    step: 0.1
    initial_value: 14
    restore_value: true
    mode: 'slider'
    on_value:
      then: 
        - script.execute: ${solar_charger_name}_write_E005_E00E_registers_script
         
             ######### 6 #########

  - platform: template
    id: ${solar_charger_name}_boost_charging_recovery_voltage_number
    name: ${name}_${solar_charger_name}_boost_charging_recovery_voltage_number
    optimistic: true
    unit_of_measurement: 'V'
    icon: mdi:sine-wave
    min_value: 12
    max_value: 14.5
    step: 0.1
    initial_value: 14
    restore_value: true
    mode: 'slider'
    on_value:
      then: 
        - script.execute: ${solar_charger_name}_write_E005_E00E_registers_script

          ######### 7 #########

  - platform: template
    id: ${solar_charger_name}_over_discharge_recovery_voltage_number
    name: ${name}_${solar_charger_name}_over_discharge_recovery_voltage_number
    optimistic: true
    unit_of_measurement: 'V'
    icon: mdi:sine-wave
    min_value: 11
    max_value: 13
    step: 0.1
    initial_value: 12.6
    restore_value: true
    mode: 'slider'
    on_value:
      then: 
        - script.execute: ${solar_charger_name}_write_E005_E00E_registers_script

         ######### 8 #########

  - platform: template
    id: ${solar_charger_name}_under_voltage_warning_number
    name: ${name}_${solar_charger_name}_under_voltage_warning_number
    optimistic: true
    unit_of_measurement: 'V'
    icon: mdi:sine-wave
    min_value: 11
    max_value: 12.6
    step: 0.1
    initial_value: 12.0
    restore_value: true
    mode: 'slider'
    on_value:
      then: 
        - script.execute: ${solar_charger_name}_write_E005_E00E_registers_script 

         ######### 9 #########

  - platform: template
    id: ${solar_charger_name}_over_discharge_voltage_number
    name: ${name}_${solar_charger_name}_over_discharge_voltage_number
    optimistic: true
    unit_of_measurement: 'V'
    icon: mdi:sine-wave
    min_value: 10
    max_value: 12
    step: 0.1
    initial_value: 11.1
    restore_value: true
    mode: 'slider'
    on_value:
      then: 
        - script.execute: ${solar_charger_name}_write_E005_E00E_registers_script 

         ######### 10 #########

  - platform: template
    id: ${solar_charger_name}_discharge_limit_voltage_number
    name: ${name}_${solar_charger_name}_discharge_limit_voltage_number
    optimistic: true
    unit_of_measurement: 'V'
    icon: mdi:sine-wave
    min_value: 9.8
    max_value: 12
    step:  0.1
    initial_value: 10.1
    restore_value: true
    mode: 'slider'
    on_value:
      then: 
        - script.execute: ${solar_charger_name}_write_E005_E00E_registers_script

     ############ Charging current ##########
  
  - platform: modbus_controller
    modbus_controller_id: ${solar_charger_name}_modbus_controller
    id: ${solar_charger_name}_charging_current_limit_number
    name: ${name}_${solar_charger_name}_charging_current_limit_number
    address: 0xE001
    value_type: U_WORD
    unit_of_measurement: 'A'
    icon: mdi:current-dc
    min_value: 2
    max_value: 100
    step:  2
    mode: 'slider'
    multiply: 100

  - platform: modbus_controller
    modbus_controller_id: ${solar_charger_name}_modbus_controller
    id: ${solar_charger_name}_battery_capacity_number
    name: ${name}_${solar_charger_name}_battery_capacity_number
    address: 0xE002
    value_type: U_WORD
    unit_of_measurement: 'Ah'
    icon: mdi:car-battery
    min_value: 50
    max_value: 1500
    step:  10
    mode: 'slider'

text_sensor:
  # - platform: modbus_controller
    # modbus_controller_id: ${solar_charger_name}_modbus_controller
    # id: ${solar_charger_name}_product_type
    # name: ${name}_${solar_charger_name}_product_type
    # bitmask: 0
    # register_type: holding
    # address: 0x00B
    # skip_updates: 10
    # raw_encode: HEXBYTES
    # lambda: |-
      # uint16_t value = modbus_controller::word_from_hex_str(x, 0);
      # switch (value) {
        # case 0: return std::string("Controller");
        # case 1: return std::string("Inverter");
        # default: return std::string("Unknown");
      # }
      # return x;

  - platform: modbus_controller
    modbus_controller_id: ${solar_charger_name}_modbus_controller
    id: ${solar_charger_name}_charging_mode
    name: ${name}_${solar_charger_name}_charging_mode
    icon: mdi:list-status
    #bitmask: 0
    register_type: holding
    address: 0x0120
    reuse_previous_range: true                     # bridge 0x011C→0x0120
    raw_encode: HEXBYTES
    lambda: |-
      uint16_t value = modbus::helpers::word_from_hex_str(x, 0);
      switch (value) {
        case 0: return std::string("Charging desactivated");
        case 1: return std::string("Charging activated");
        case 2: return std::string("MPPT charge mode");
        case 3: return std::string("Equalizing charge mode");
        case 4: return std::string("Boost charge mode");
        case 5: return std::string("Float charge mode");
        case 6: return std::string("Current limiting");
        default: return std::string("Unknown");
      }
      return x;

  - platform: modbus_controller
    modbus_controller_id: ${solar_charger_name}_modbus_controller
    id: ${solar_charger_name}_product_model
    name: ${name}_${solar_charger_name}_product_model
    register_type: holding
    address: 0x00C
    response_size: 16
    raw_encode: NONE
    skip_updates: 10
  
  # - platform: template
    # id: ${solar_charger_name}_warnings_and_errors_hi_text
    # name: ${name}_${solar_charger_name}_warnings_and_errors_hi_text
    # icon: mdi:alert-circle
    
  - platform: template
    id: ${solar_charger_name}_warnings_and_errors_hi_text
    name: ${name}_${solar_charger_name}_warnings_and_errors_hi_text
    icon: mdi:alert-circle
    lambda: |-
      return id(${solar_charger_name}_warnings_and_errors_hi_text).state; 
     

  # - platform: template
  #   id: ${solar_charger_name}_warnings_and_errors_low_text
  #   name: ${solar_charger_name}_warnings_and_errors_low_text
  #   icon: mdi:alert-circle    

#   - platform: template
#     id: ${solar_charger_name}_warnings_and_errors_low_text
#     name: ${name}_${solar_charger_name}_warnings_and_errors_low_text
#     icon: mdi:alert-circle  

  - platform: template
    id: ${solar_charger_name}_warnings_and_errors_low_text
    name: ${name}_${solar_charger_name}_warnings_and_errors_low_text
    icon: mdi:alert-circle
    lambda: |-
      return id(${solar_charger_name}_warnings_and_errors_low_text).state; 

  - platform: template
    id: ${solar_charger_name}_charger_status_text
    name: ${name}_${solar_charger_name}_battery_type_text
    icon: mdi:car-battery
    update_interval: ${solar_charger_text_update}
    lambda: |-
      if (isnan(id(${solar_charger_name}_battery_type).state)) { 
        return {"KO"};
      }
      else {
        static const char *battery_list[] = {"User defined","Open (FLD)", "Sealed (SLD)", "Gel" , "Lithium"};
        return {battery_list[int(id(${solar_charger_name}_battery_type).state)]};
      }
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
