SeByDocKy/pvbrain2/pvbrain2/inverter/sofar/device_sofar.yaml

modbus_controller:
  - id: ${inverter_name}_modbus_controller
    address: ${inverter_modbus_address}
    modbus_id: ${inverter_modbus_id}
    setup_priority: -10
    update_interval: ${inverter_update_interval}
    
text_sensor:
  - platform: modbus_controller
    modbus_controller_id: ${inverter_name}_modbus_controller
    name: ${name}_${inverter_name}_state
    id: ${inverter_name}_state
    address: 0x0200
    register_type: holding
    raw_encode: HEXBYTES
    lambda: |-
      uint16_t value = modbus::helpers::word_from_hex_str(x, 0);
      switch (value) {
        case 0: return std::string("waiting");
        case 1: return std::string("charging check");
        case 2: return std::string("charging");
        case 3: return std::string("discharging check");
        case 4: return std::string("discharging");
        case 5: return std::string("EPS");
        case 6: return std::string("fault");
        case 7: return std::string("permanent fault");
        default: return std::string("Unknown");
      }
      return x;

sensor:
  - platform: modbus_controller
    modbus_controller_id: ${inverter_name}_modbus_controller
    name: ${name}_${inverter_name}_battery_power
    id: ${inverter_name}_battery_power
    address: 0x020D
    register_type: holding
    value_type: S_WORD
    unit_of_measurement: 'W'
    device_class: power
    accuracy_decimals: 2
    icon: "mdi:lightning-bolt"
    
  - platform: modbus_controller
    modbus_controller_id: ${inverter_name}_modbus_controller
    name: ${name}_${inverter_name}_battery_voltage
    id: ${inverter_name}_battery_voltage
    address: 0x020E
    register_type: holding
    value_type: S_WORD
    unit_of_measurement: 'V'
    device_class: power
    accuracy_decimals: 2
    icon: "mdi:sine-wave"
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
